drewsum/Thermal_Camera/rev_a/hdw/Thermal_Camera/Battery_Management.kicad_sch

## KiCad design rev_a/hdw/Thermal_Camera/Battery_Management.kicad_sch (2024-10-11)

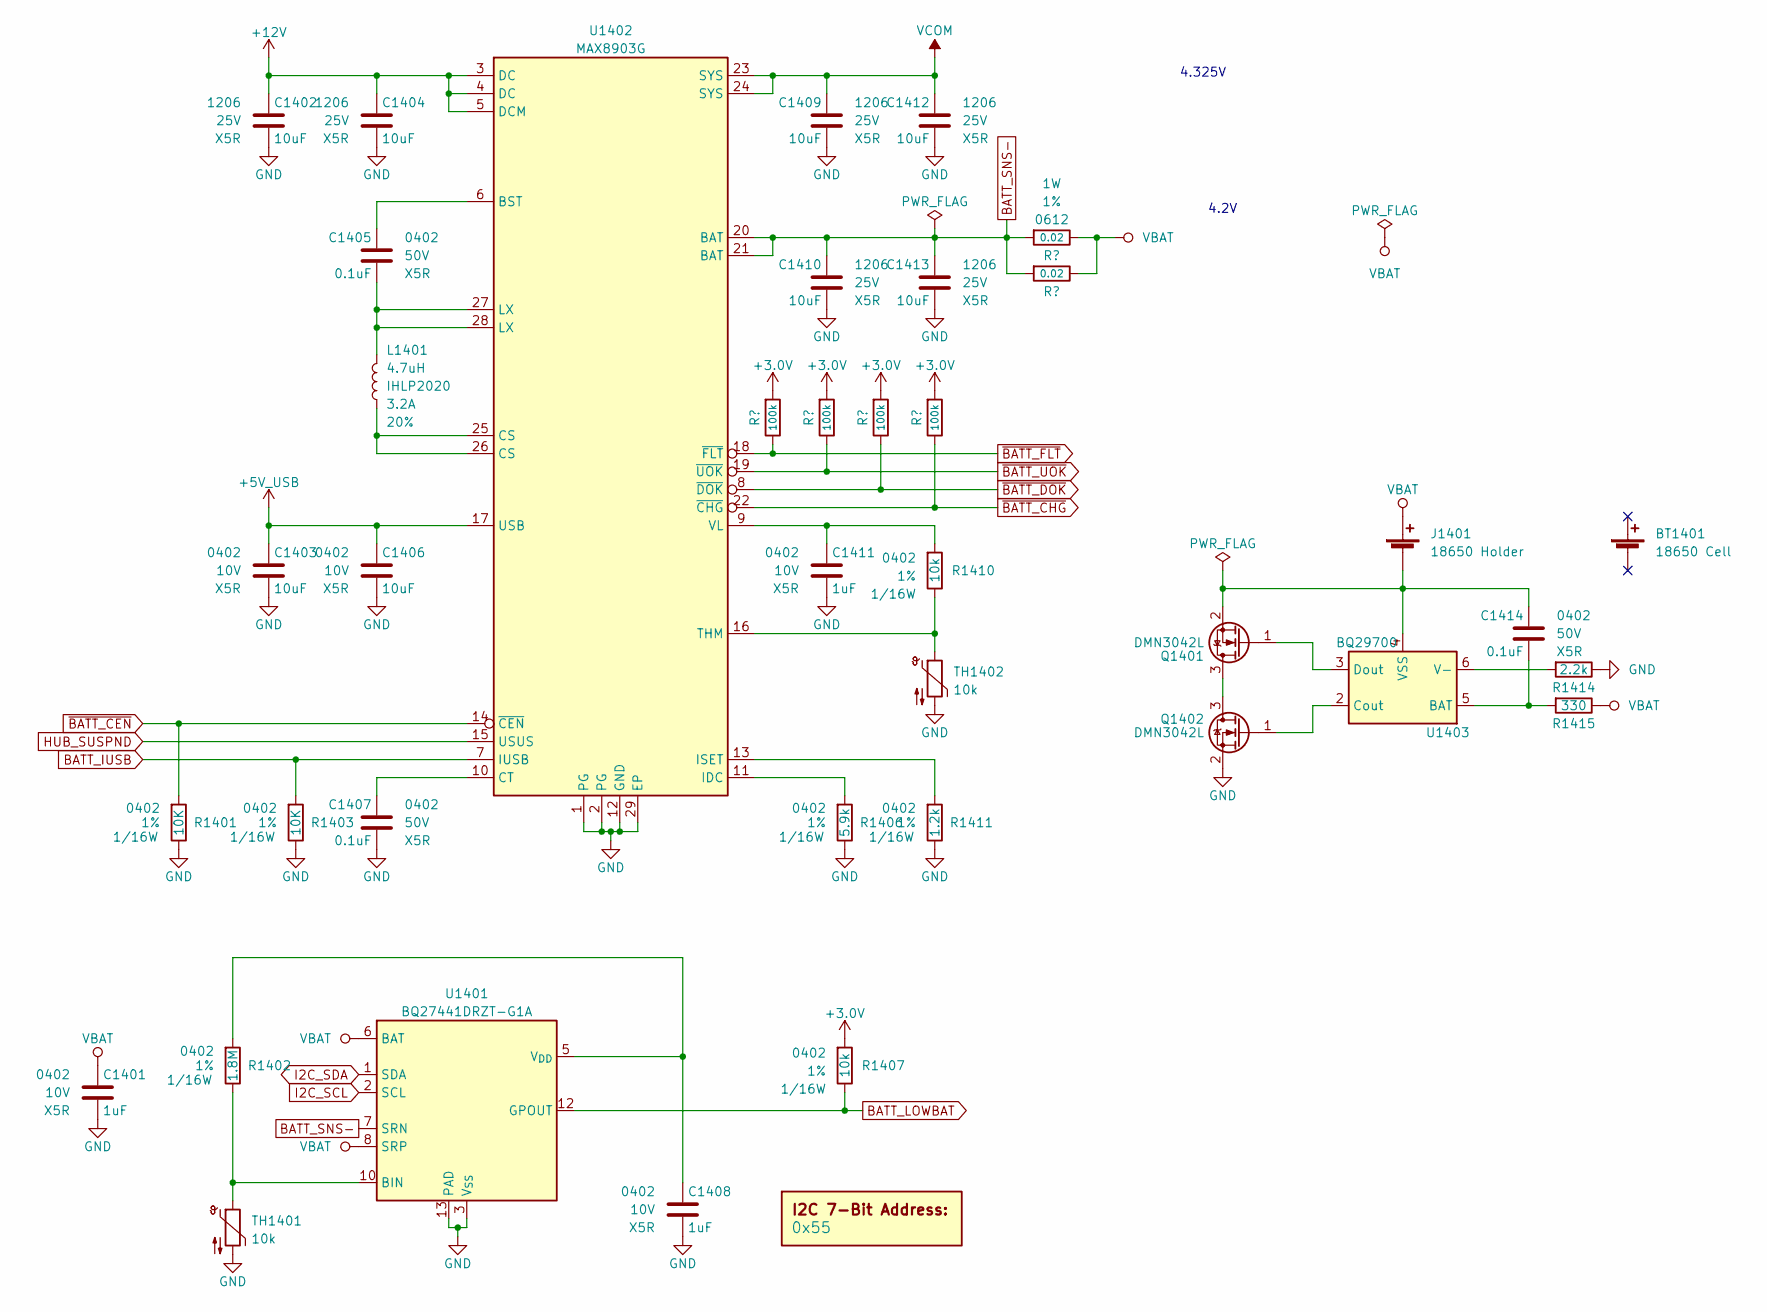
[picture p4: schematic Battery_Management.kicad_sch]

Parts:
BT1401: 18650 Cell; Digi-Key PN 1568-1488-ND
C1401, C1408, C1411: 1uF; C_0402; Voltage 10V; Digi-Key PN 311-1439-1-ND
C1402, C1404, C1409, C1410, C1412, C1413: 10uF; C_1206; Voltage 25V; Digi-Key PN 399-8153-1-ND
C1403, C1406: 10uF; C_0402; Voltage 10V; Digi-Key PN 490-GRM155R61A106ME11DCT-ND
C1405, C1407, C1414: 0.1uF; C_0402; Voltage 50V; Digi-Key PN 490-10697-1-ND
DOC1401: 0x55
J1401: 18650 Holder; BatteryHolder_MPD_BH-18650-PC2; Digi-Key PN BK-18650-PC2-ND
L1401: 4.7uH; L_Vishay_IHLP-2020; Tolerance 20%; Digi-Key PN 541-1222-1-ND
Q1401, Q1402: DMN3042L; SOT-23; Digi-Key PN DMN3042L-7DICT-ND
R1401, R1403: 10K; R_0402; Tolerance 1%; Digi-Key PN RMCF0402FT10K0CT-ND
R1402: 1.8M; R_0402; Tolerance 1%; Digi-Key PN RMCF0402FT1M80CT-ND
R1404, R1405, R1408, R1409: 100k; R_0402; Tolerance 1%; Digi-Key PN RMCF0402FT100KCT-ND
R1406: 5.9k; R_0402; Tolerance 1%; Digi-Key PN RMCF0402FT5K90CT-ND
R1407, R1410: 10k; R_0402; Tolerance 1%; Digi-Key PN RMCF0402FT10K0CT-ND
R1411: 1.2k; R_0402; Tolerance 1%; Digi-Key PN RMCF0402FT1K20CT-ND
R1412, R1413: 0.02; R_0612; Tolerance 1%; Digi-Key PN P16010CT-ND
R1414: 2.2k; R_0402; Tolerance 1%; Digi-Key PN RMCF0402FT2K20CT-ND
R1415: 330; R_0402; Tolerance 1%; Digi-Key PN RMCF0402FT330RCT-ND
TH1401, TH1402: 10k; R_0402; Digi-Key PN 445-174911-1-ND
U1401: BQ27441DRZT-G1A; Texas_S-PDSO-N12; Digi-Key PN 296-37271-1-ND
U1402: MAX8903G; QFN-28-1EP_4x4mm_P0.4mm_EP2.6x2.6mm; Digi-Key PN MAX8903GETI+-ND
U1403: BQ29700; WSON-6_1.5x1.5mm_P0.5mm; Digi-Key PN 296-43985-1-ND

Connections:
+3.0V: R1404.1, R1405.1, R1407.1, R1408.1, R1409.1
+5V_USB: C1403.1, C1406.1, U1402.17 (USB)
+12V: C1402.1, C1404.1, U1402.3 (DC), U1402.4 (DC), U1402.5 (DCM)
BATT_IUSB: R1403.1, U1402.7 (IUSB)
BATT_LOWBAT: R1407.2, U1401.12 (GPOUT)
BATT_SNS-: C1410.1, C1413.1, R1412.1, R1413.1, U1401.7 (SRN), U1402.20 (BAT), U1402.21 (BAT)
GND: C1401.2, C1402.2, C1403.2, C1404.2, C1406.2, C1407.2, C1408.2, C1409.2, C1410.2, C1411.2, C1412.2, C1413.2, Q1402.2 (S), R1401.2, R1403.2, R1406.2, R1411.2, R1414.2, TH1401.2, TH1402.2, U1401.3 (V_{SS}), U1401.13 (PAD), U1402.1 (PG), U1402.2 (PG), U1402.12 (GND), U1402.29 (EP)
HUB_SUSPND: U1402.15 (USUS)
I2C_SCL: U1401.2 (SCL)
I2C_SDA: U1401.1 (SDA)
unnamed: C1405.1, U1402.6 (BST)
unnamed: C1405.2, L1401.2, U1402.27 (LX), U1402.28 (LX)
unnamed: C1407.1, U1402.10 (CT)
unnamed: C1408.1, R1402.1, U1401.5 (V_{DD})
unnamed: C1411.1, R1410.1, U1402.9 (VL)
unnamed: C1414.1, J1401.2 (-), Q1401.2 (S), U1403.4 (VSS)
unnamed: C1414.2, R1415.1, U1403.5 (BAT)
unnamed: L1401.1, U1402.25 (CS), U1402.26 (CS)
unnamed: Q1401.1 (G), U1403.3 (Dout)
unnamed: Q1401.3 (D), Q1402.3 (D)
unnamed: Q1402.1 (G), U1403.2 (Cout)
unnamed: R1402.2, TH1401.1, U1401.10 (BIN)
unnamed: R1406.1, U1402.11 (IDC)
unnamed: R1410.2, TH1402.1, U1402.16 (THM)
unnamed: R1411.1, U1402.13 (ISET)
unnamed: R1414.1, U1403.6 (V-)
VBAT: C1401.1, J1401.1 (+), R1412.2, R1413.2, R1415.2, U1401.6 (BAT), U1401.8 (SRP)
VCOM: C1409.1, C1412.1, U1402.23 (SYS), U1402.24 (SYS)
~BATT_CEN: R1401.1, U1402.14 (~CEN)
~BATT_CHG: R1409.2, U1402.22 (~CHG)
~BATT_DOK: R1408.2, U1402.8 (~DOK)
~BATT_FLT: R1404.2, U1402.18 (~FLT)
~BATT_UOK: R1405.2, U1402.19 (~UOK)

Notes on the sheet:
4.325V
4.2V
