drewsum/Thermal_Camera/rev_a/hdw/Thermal_Camera/Capacitive_Touch.kicad_sch

## KiCad design rev_a/hdw/Thermal_Camera/Capacitive_Touch.kicad_sch (2024-10-11)

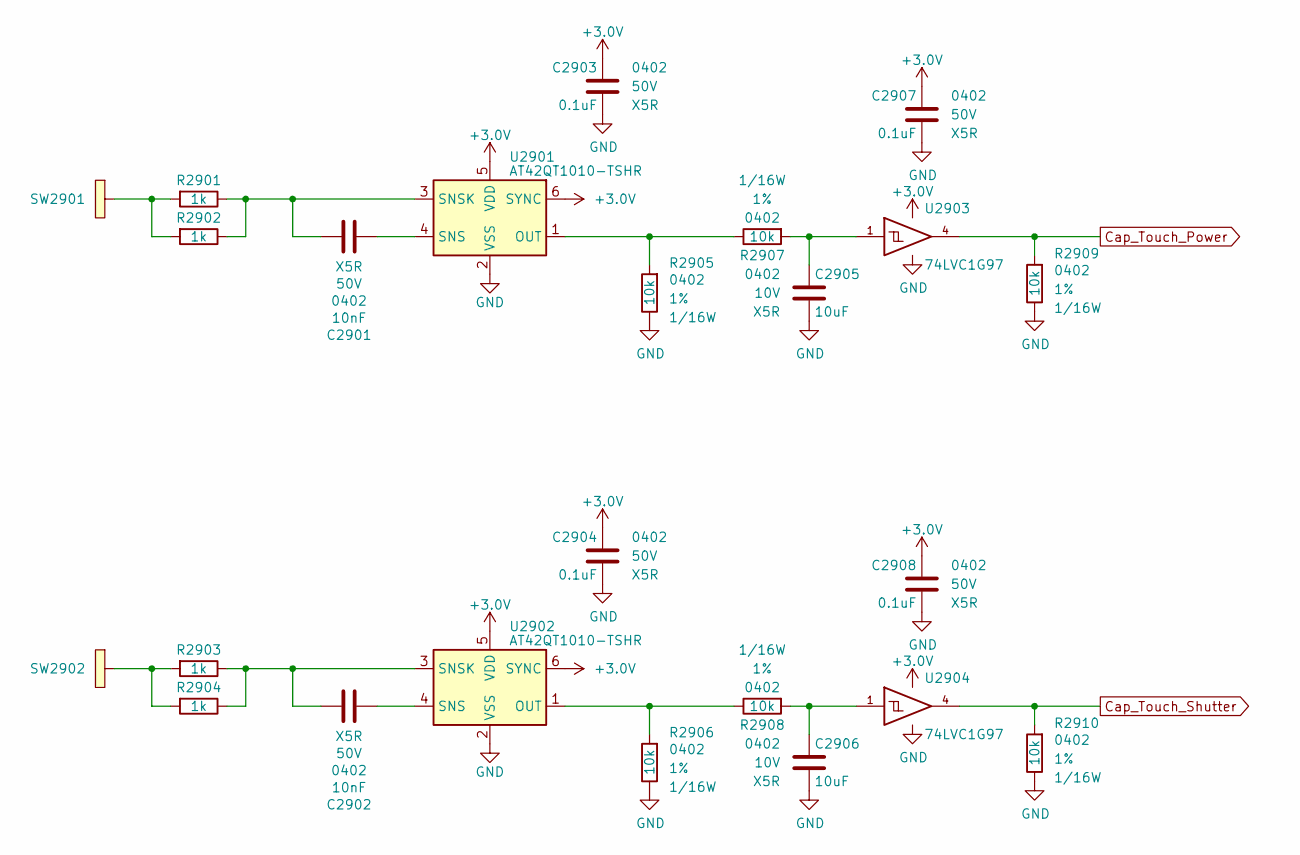
[picture p5: schematic Capacitive_Touch.kicad_sch]

Parts:
C2901, C2902: 10nF; C_0402; Voltage 50V; Digi-Key PN 445-12201-1-ND
C2903, C2904, C2907, C2908: 0.1uF; C_0402; Voltage 50V; Digi-Key PN 490-10697-1-ND
C2905, C2906: 10uF; C_0402; Voltage 10V; Digi-Key PN 490-GRM155R61A106ME11DCT-ND
R2901, R2902, R2903, R2904: 1k; R_0402; Tolerance 1%; Digi-Key PN RMCF0402FT1K00CT-ND
R2905, R2906, R2907, R2908, R2909, R2910: 10k; R_0402; Tolerance 1%; Digi-Key PN RMCF0402FT10K0CT-ND
SW2901, SW2902: Cap_Touch; Capacitive_Touch_Pad
U2901, U2902: AT42QT1010-TSHR; SOT-23-6; Digi-Key PN AT42QT1010-TSHRCT-ND
U2903, U2904: 74LVC1G97; SOT-363_SC-70-6; Digi-Key PN 296-15582-1-ND

Connections:
+3.0V: C2903.1, C2904.1, C2907.1, C2908.1, U2901.5 (VDD), U2901.6 (SYNC), U2902.5 (VDD), U2902.6 (SYNC), U2903.5 (VCC), U2904.5 (VCC)
Cap_Touch_Power: R2909.1, U2903.4
Cap_Touch_Shutter: R2910.1, U2904.4
GND: C2903.2, C2904.2, C2905.2, C2906.2, C2907.2, C2908.2, R2905.2, R2906.2, R2909.2, R2910.2, U2901.2 (VSS), U2902.2 (VSS), U2903.2 (GND), U2903.3 (GND), U2903.6 (GND), U2904.2 (GND), U2904.3 (GND), U2904.6 (GND)
unnamed: C2901.1, U2901.4 (SNS)
unnamed: C2901.2, R2901.2, R2902.2, U2901.3 (SNSK)
unnamed: C2902.1, U2902.4 (SNS)
unnamed: C2902.2, R2903.2, R2904.2, U2902.3 (SNSK)
unnamed: C2905.1, R2907.1, U2903.1
unnamed: C2906.1, R2908.1, U2904.1
unnamed: R2901.1, R2902.1, SW2901.1
unnamed: R2903.1, R2904.1, SW2902.1
unnamed: R2905.1, R2907.2, U2901.1 (OUT)
unnamed: R2906.1, R2908.2, U2902.1 (OUT)
