drewsum/Thermal_Camera/rev_a/hdw/Thermal_Camera/Elapsed_Time_Counter.kicad_sch

## KiCad design rev_a/hdw/Thermal_Camera/Elapsed_Time_Counter.kicad_sch (2024-10-11)

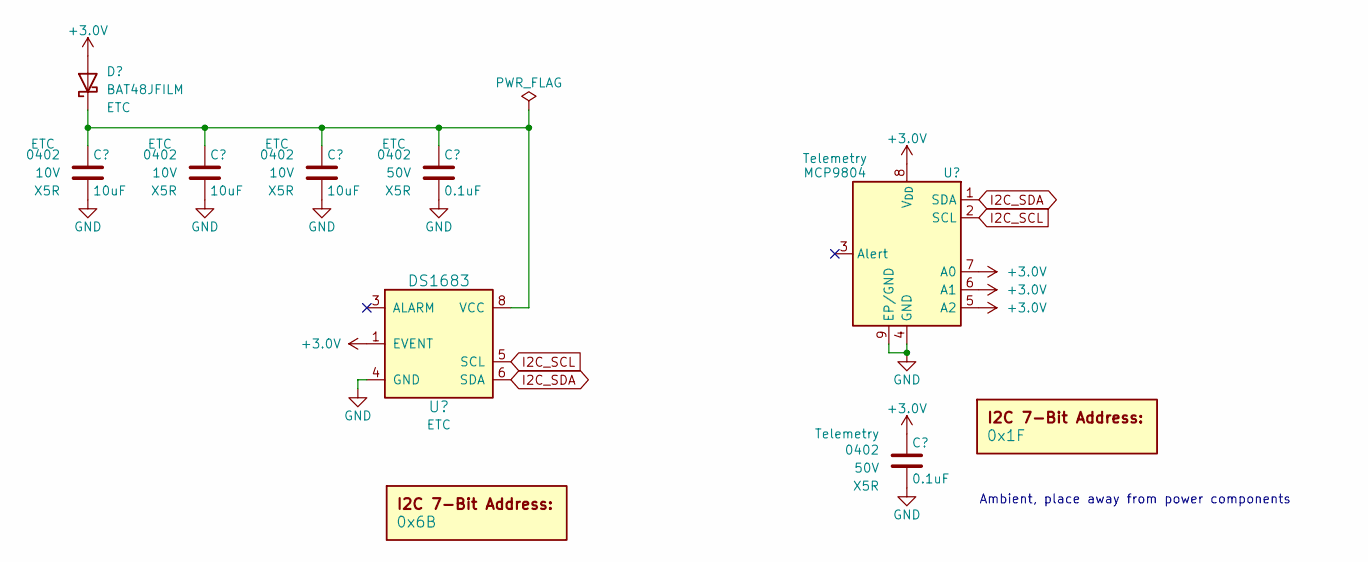
[picture p6: schematic Elapsed_Time_Counter.kicad_sch]

Parts:
C2301, C2302, C2303: 10uF; C_0402; Voltage 10V; Digi-Key PN 490-GRM155R61A106ME11DCT-ND
C2304, C2305: 0.1uF; C_0402; Voltage 50V; Digi-Key PN 490-10697-1-ND
D2301: BAT48JFILM; D_SOD-323; Digi-Key PN 497-5711-1-ND
DOC2301: 0x6B
DOC2302: 0x1F
U2301: DS1683; SOIC-8_3.9x4.9mm_Pitch1.27mm; Digi-Key PN DS1683S+-ND
U2302: MCP9804; DFN-8-1EP_3x2mm_P0.5mm_EP1.3x1.5mm; Digi-Key PN MCP9804T-E/MCCT-ND

Connections:
+3.0V: C2305.1, D2301.2 (A), U2301.1 (EVENT), U2302.5 (A2), U2302.6 (A1), U2302.7 (A0), U2302.8 (V_{DD})
GND: C2301.2, C2302.2, C2303.2, C2304.2, C2305.2, U2301.4 (GND), U2302.4 (GND), U2302.9 (EP/GND)
I2C_SCL: U2301.5 (SCL), U2302.2 (SCL)
I2C_SDA: U2301.6 (SDA), U2302.1 (SDA)
unnamed: C2301.1, C2302.1, C2303.1, C2304.1, D2301.1 (K), U2301.8 (VCC)

Notes on the sheet:
Ambient, place away from power components
