drewsum/Thermal_Camera/rev_a/hdw/Thermal_Camera/External_Storage.kicad_sch

## KiCad design rev_a/hdw/Thermal_Camera/External_Storage.kicad_sch (2024-10-11)

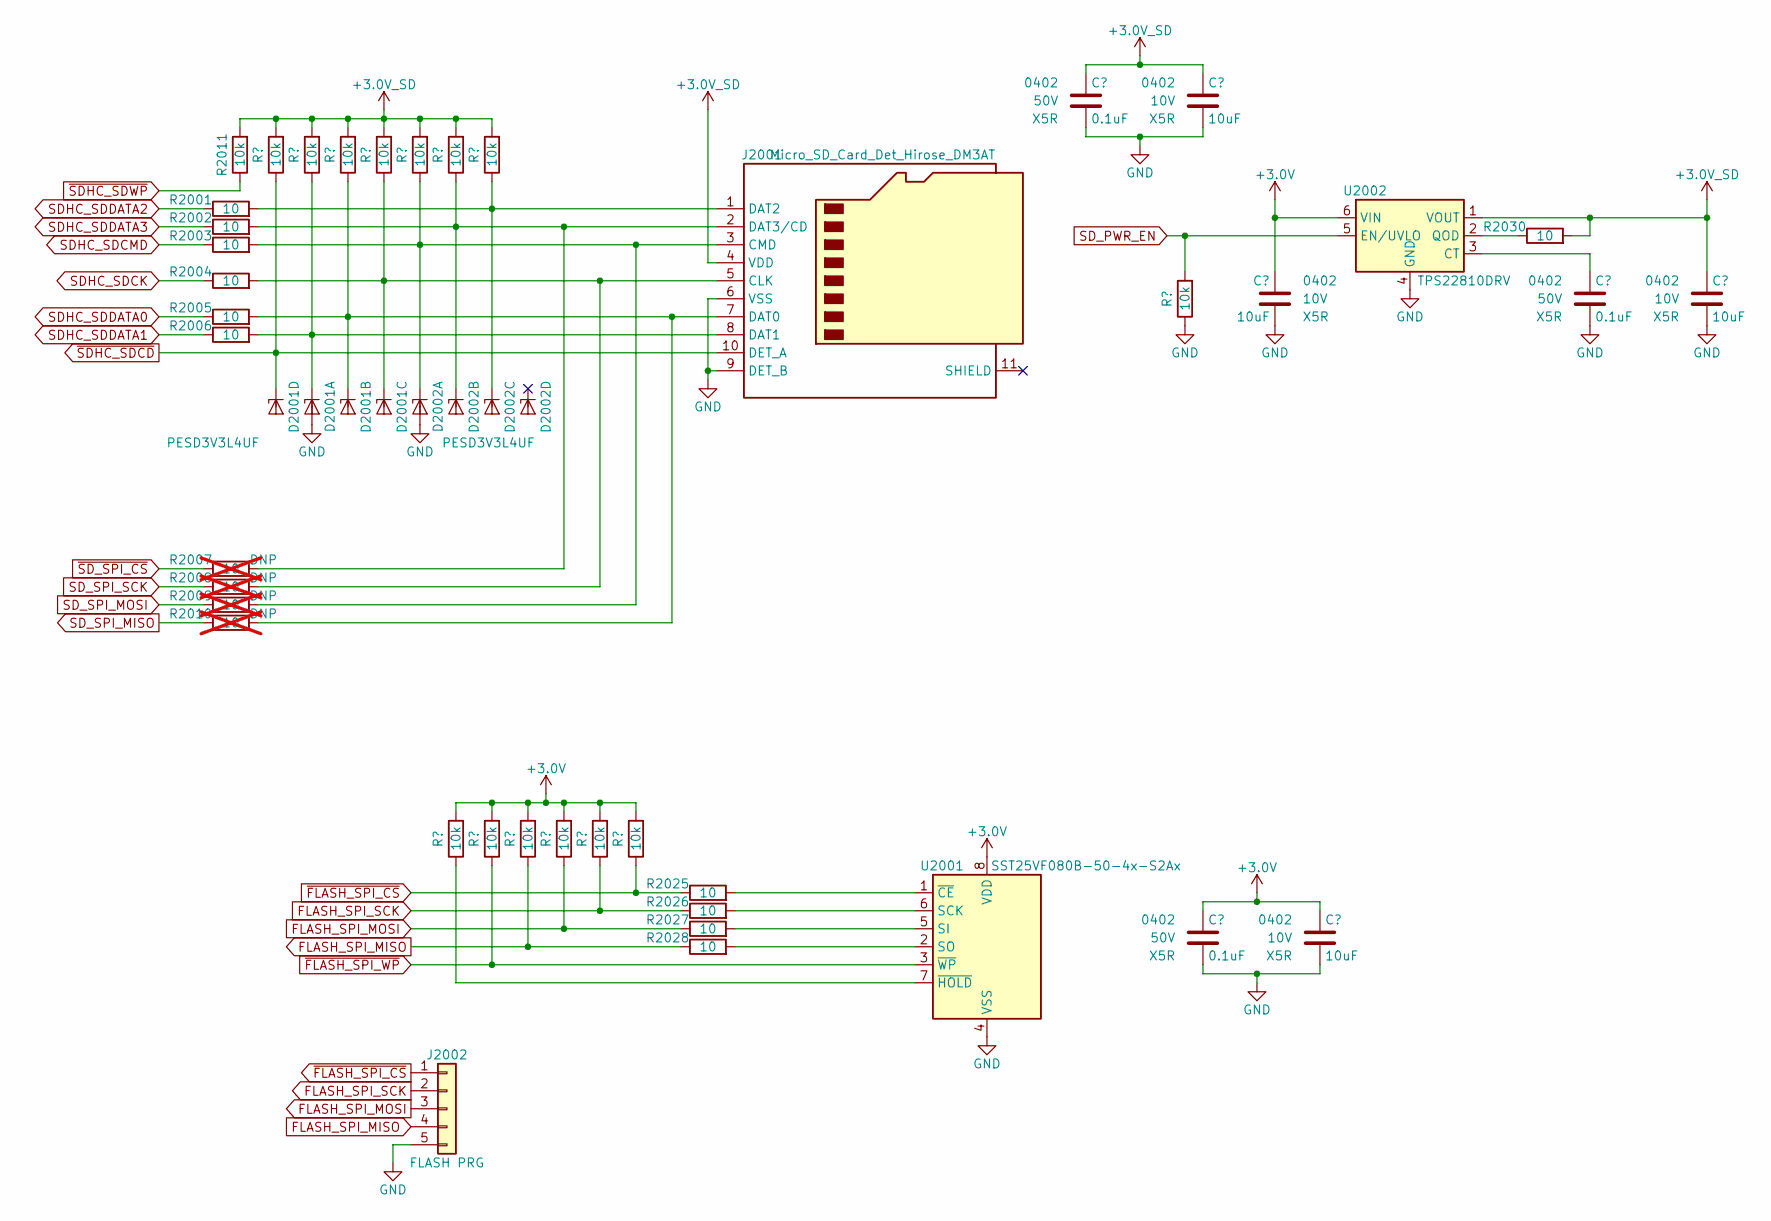
[picture p7: schematic External_Storage.kicad_sch]

Parts:
C2001, C2003, C2006: 0.1uF; C_0402; Voltage 50V; Digi-Key PN 490-10697-1-ND
C2002, C2004, C2005, C2007: 10uF; C_0402; Voltage 10V; Digi-Key PN 490-GRM155R61A106ME11DCT-ND
D2001, D2002: PESD3V3L4UF; SOT-886
J2001: Micro_SD_Card_Det_Hirose_DM3AT; Hirose_DM3AT-SF-PEJM5; Digi-Key PN HR1964CT-ND
J2002: FLASH PRG; PinSocket_1x05_P2.54mm_Vertical
R2001, R2002, R2003, R2004, R2005, R2006, R2025, R2026, R2027, R2028, R2030: 10; R_0402; Tolerance 1%; Digi-Key PN RMCF0402FT10R0CT-ND
R2007, R2008, R2009, R2010: 10; R_0402; Tolerance 1%; Digi-Key PN RMCF0402FT10R0CT-ND; not fitted
R2011, R2012, R2013, R2014, R2015, R2016, R2017, R2018, R2019, R2020, R2021, R2022, R2023, R2024, R2029: 10k; R_0402; Tolerance 1%; Digi-Key PN RMCF0402FT10K0CT-ND
U2001: SST25VF080B-50-4x-S2Ax; SOIC-8_5.275x5.275mm_P1.27mm; Digi-Key PN SST25VF080B-50-4C-S2AF-ND
U2002: TPS22810DRV; WSON-6-1EP_2x2mm_P0.65mm_EP1x1.6mm; Digi-Key PN 296-47868-1-ND

Connections:
+3.0V: C2003.1, C2004.1, C2005.1, R2018.1, R2020.1, R2021.1, R2022.1, R2023.1, R2024.1, U2001.8 (VDD), U2002.6 (VIN)
+3.0V_SD: C2001.1, C2002.1, C2007.1, J2001.4 (VDD), R2011.1, R2012.1, R2013.1, R2014.1, R2015.1, R2016.1, R2017.1, R2019.1, R2030.1, U2002.1 (VOUT)
FLASH_SPI_MISO: J2002.4, R2021.2, R2028.2
FLASH_SPI_MOSI: J2002.3, R2022.2, R2027.2
FLASH_SPI_SCK: J2002.2, R2023.2, R2026.2
GND: C2001.2, C2002.2, C2003.2, C2004.2, C2005.2, C2006.2, C2007.2, D2001.2 (A), D2001.5 (A), D2002.2 (A), D2002.5 (A), J2001.6 (VSS), J2001.9 (DET_B), J2002.5, R2029.2, U2001.4 (VSS), U2002.4 (GND), U2002.7 (GND)
unnamed: C2006.1, U2002.3 (CT)
unnamed: D2001.1 (K1), J2001.8 (DAT1), R2006.1, R2013.2
unnamed: D2001.3 (K2), J2001.7 (DAT0), R2005.1, R2010.1, R2014.2
unnamed: D2001.4 (K3), J2001.5 (CLK), R2004.1, R2008.1, R2015.2
unnamed: D2002.1 (K1), J2001.3 (CMD), R2003.1, R2009.1, R2016.2
unnamed: D2002.3 (K2), J2001.2 (DAT3/CD), R2002.1, R2007.1, R2017.2
unnamed: D2002.4 (K3), J2001.1 (DAT2), R2001.1, R2019.2
unnamed: R2018.2, U2001.7 (~HOLD)
unnamed: R2025.1, U2001.1 (~CE)
unnamed: R2026.1, U2001.6 (SCK)
unnamed: R2027.1, U2001.5 (SI)
unnamed: R2028.1, U2001.2 (SO)
unnamed: R2030.2, U2002.2 (QOD)
SDHC_SDCK: R2004.2
SDHC_SDCMD: R2003.2
SDHC_SDDATA0: R2005.2
SDHC_SDDATA1: R2006.2
SDHC_SDDATA2: R2001.2
SDHC_SDDATA3: R2002.2
SD_PWR_EN: R2029.1, U2002.5 (EN/UVLO)
SD_SPI_MISO: R2010.2
SD_SPI_MOSI: R2009.2
SD_SPI_SCK: R2008.2
~FLASH_SPI_CS: J2002.1, R2024.2, R2025.2
~FLASH_SPI_WP: R2020.2, U2001.3 (~WP)
~SDHC_SDCD: D2001.6 (K4), J2001.10 (DET_A), R2012.2
~SDHC_SDWP: R2011.2
~SD_SPI_CS: R2007.2
