drewsum/Thermal_Camera/rev_a/hdw/Thermal_Camera/FLIR_Lepton_Sensor.kicad_sch

## KiCad design rev_a/hdw/Thermal_Camera/FLIR_Lepton_Sensor.kicad_sch (2024-10-11)

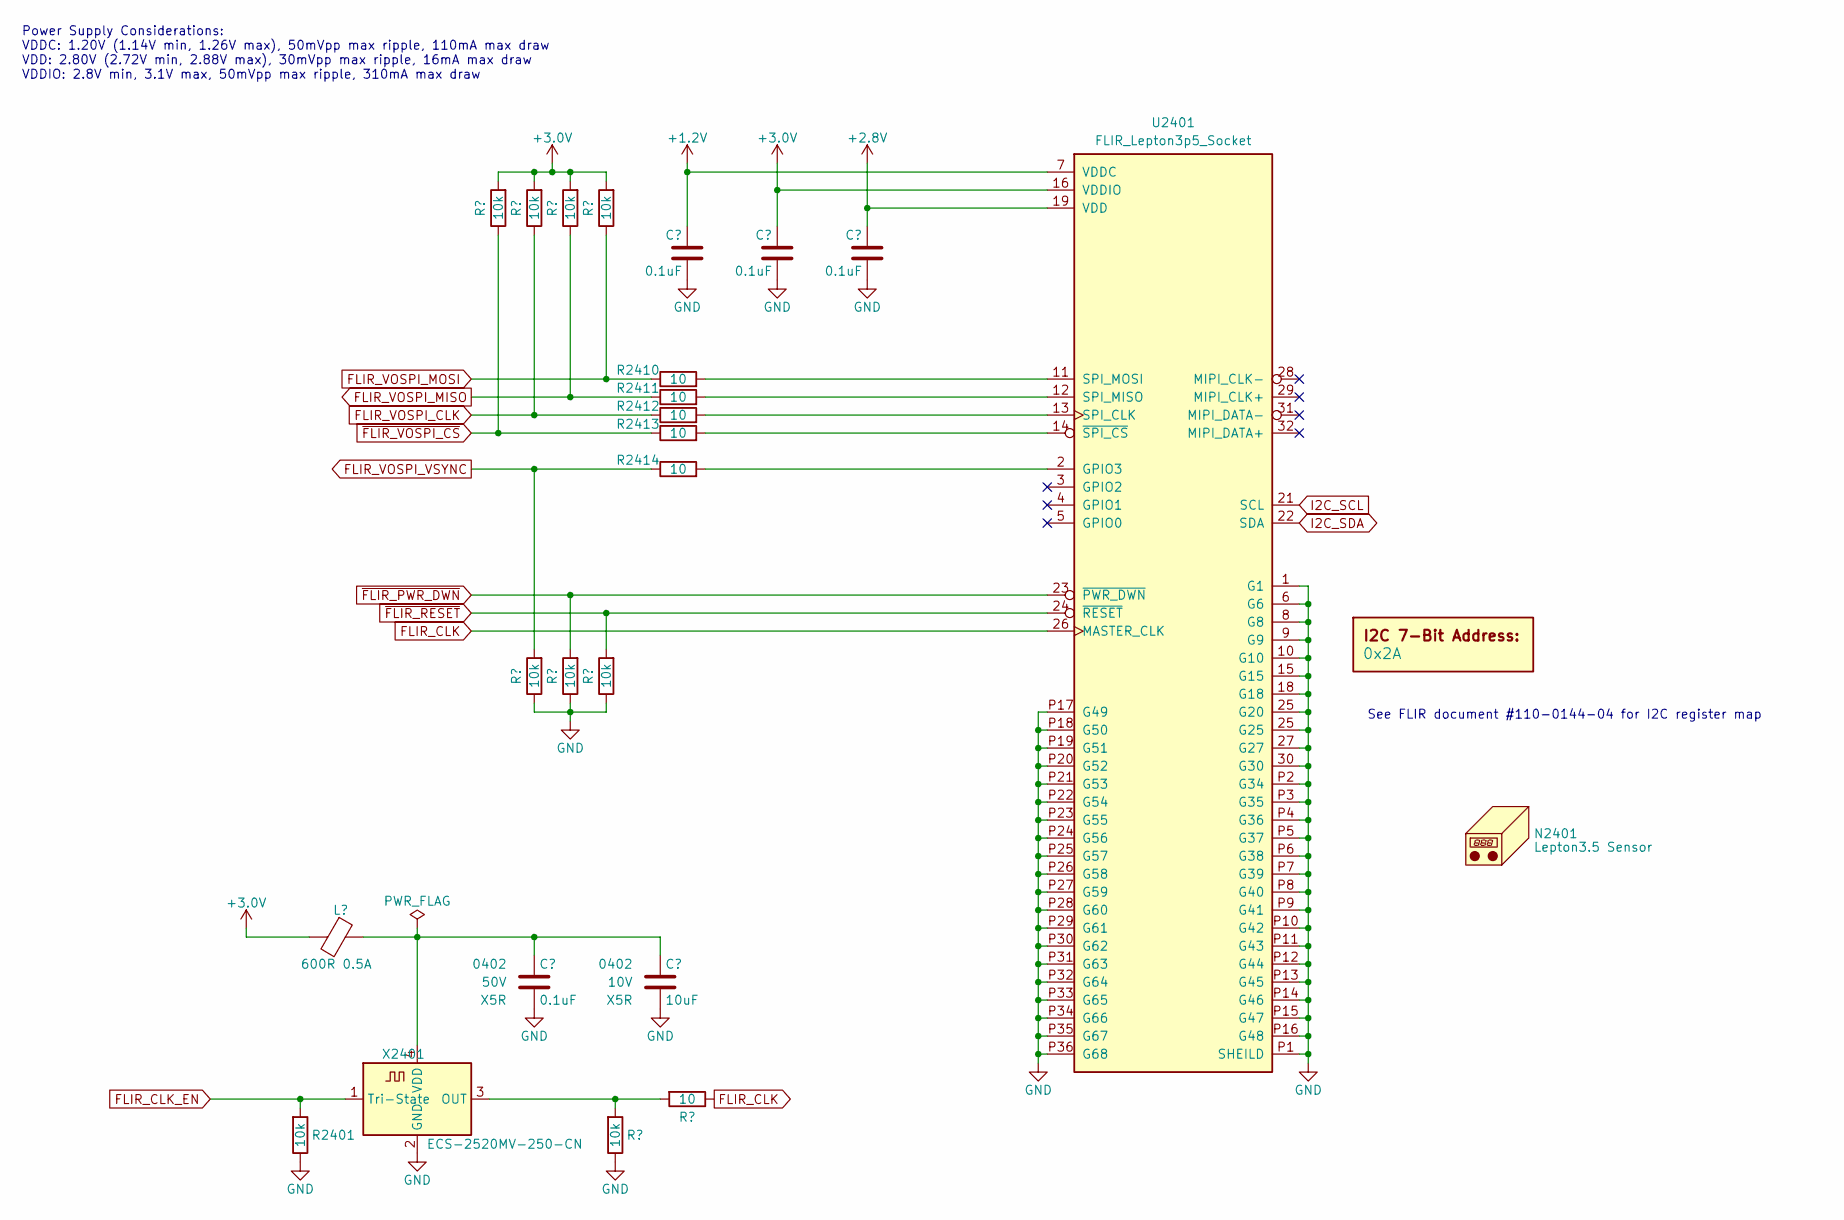
[picture p8: schematic FLIR_Lepton_Sensor.kicad_sch]

Parts:
C2401, C2403, C2404, C2405: 0.1uF; C_0402; Voltage 50V; Digi-Key PN 490-10697-1-ND
C2402: 10uF; C_0402; Voltage 10V; Digi-Key PN 490-GRM155R61A106ME11DCT-ND
DOC2401: 0x2A
L2401: 600R 0.5A; L_0402
N2401: Lepton3.5 Sensor; Digi-Key PN 500-0771-01-ND
R2401, R2402, R2403, R2404, R2405, R2406, R2407, R2408, R2409: 10k; R_0402; Tolerance 1%; Digi-Key PN RMCF0402FT10K0CT-ND
R2410, R2411, R2412, R2413, R2414, R2415: 10; R_0402; Tolerance 1%; Digi-Key PN RMCF0402FT10R0CT-ND
U2401: FLIR_Lepton3p5_Socket; MOLEX_105028-1001; Digi-Key PN 1050281001
X2401: ECS-2520MV-250-CN; Oscillator_SMD_ECS_2520MV-xxx-xx-4Pin_2.5x2.0mm; Digi-Key PN XC2752CT-ND

Connections:
+1.2V: C2403.1, U2401.7 (VDDC)
+2.8V: C2405.1, U2401.19 (VDD)
+3.0V: C2404.1, L2401.2, R2402.1, R2403.1, R2405.1, R2407.1, U2401.16 (VDDIO)
FLIR_CLK: R2415.2, U2401.26 (MASTER_CLK)
FLIR_CLK_EN: R2401.1, X2401.1 (Tri-State)
FLIR_VOSPI_CLK: R2403.2, R2412.2
FLIR_VOSPI_MISO: R2405.2, R2411.2
FLIR_VOSPI_MOSI: R2407.2, R2410.2
FLIR_VOSPI_VSYNC: R2404.1, R2414.2
GND: C2401.2, C2402.2, C2403.2, C2404.2, C2405.2, R2401.2, R2404.2, R2406.2, R2408.2, R2409.2, U2401.1 (G1), U2401.6 (G6), U2401.8 (G8), U2401.9 (G9), U2401.10 (G10), U2401.15 (G15), U2401.18 (G18), U2401.25 (G20), U2401.27 (G27), U2401.30 (G30), U2401.P1 (SHEILD), U2401.P2 (G34), U2401.P3 (G35), U2401.P4 (G36), U2401.P5 (G37), U2401.P6 (G38), U2401.P7 (G39), U2401.P8 (G40), U2401.P9 (G41), U2401.P10 (G42), U2401.P11 (G43), U2401.P12 (G44), U2401.P13 (G45), U2401.P14 (G46), U2401.P15 (G47), U2401.P16 (G48), U2401.P17 (G49), U2401.P18 (G50), U2401.P19 (G51), U2401.P20 (G52), U2401.P21 (G53), U2401.P22 (G54), U2401.P23 (G55), U2401.P24 (G56), U2401.P25 (G57), U2401.P26 (G58), U2401.P27 (G59), U2401.P28 (G60), U2401.P29 (G61), U2401.P30 (G62), U2401.P31 (G63), U2401.P32 (G64), U2401.P33 (G65), U2401.P34 (G66), U2401.P35 (G67), U2401.P36 (G68), X2401.2 (GND)
I2C_SCL: U2401.21 (SCL)
I2C_SDA: U2401.22 (SDA)
unnamed: C2401.1, C2402.1, L2401.1, X2401.4 (VDD)
unnamed: R2409.1, R2415.1, X2401.3 (OUT)
unnamed: R2410.1, U2401.11 (SPI_MOSI)
unnamed: R2411.1, U2401.12 (SPI_MISO)
unnamed: R2412.1, U2401.13 (SPI_CLK)
unnamed: R2413.1, U2401.14 (~SPI_CS)
unnamed: R2414.1, U2401.2 (GPIO3)
~FLIR_PWR_DWN: R2406.1, U2401.23 (~PWR_DWN)
~FLIR_RESET: R2408.1, U2401.24 (~RESET)
~FLIR_VOSPI_CS: R2402.2, R2413.2

Notes on the sheet:
Power Supply Considerations: VDDC: 1.20V (1.14V min, 1.26V max), 50mVpp max ripple, 110mA max draw VDD: 2.80V (2.72V min, 2.88V max), 30mVpp max ripple, 16mA max draw VDDIO: 2.8V min, 3.1V max, 50mVpp max ripple, 310mA max draw
See FLIR document #110-0144-04 for I2C register map
