drewsum/Thermal_Camera/rev_a/hdw/Thermal_Camera/Graphic_LCD.kicad_sch

## KiCad design rev_a/hdw/Thermal_Camera/Graphic_LCD.kicad_sch (2024-10-11)

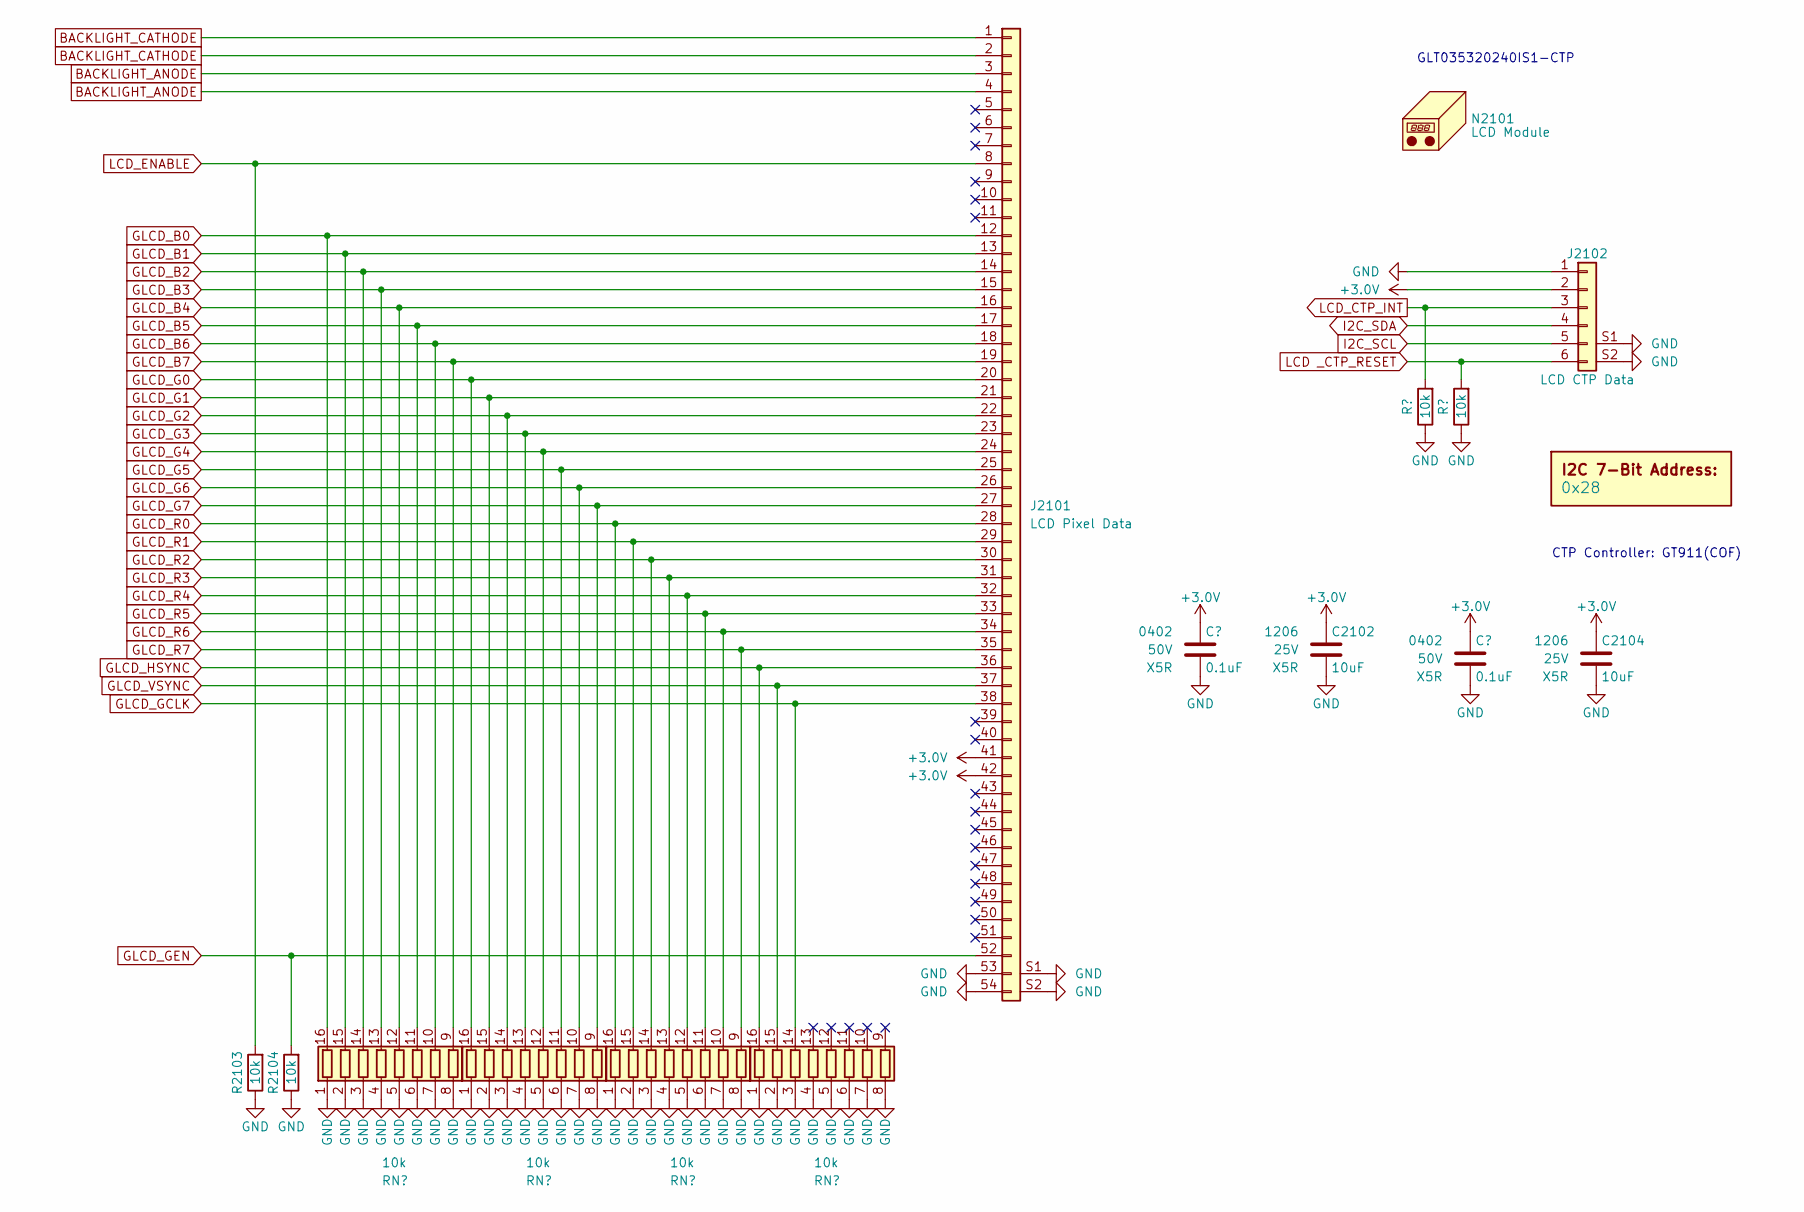
[picture p9: schematic Graphic_LCD.kicad_sch]

Parts:
C2101, C2103: 0.1uF; C_0402; Voltage 50V; Digi-Key PN 490-10697-1-ND
C2102, C2104: 10uF; C_1206; Voltage 25V; Digi-Key PN 399-8153-1-ND
DOC2101: 0x28
J2101: LCD Pixel Data; GCT_FFC2B35-54-G_REVA2; Digi-Key PN 2073-FFC2B35-54-GCT-ND
J2102: LCD CTP Data; GCT_FFC2B35-06-G_REVA2; Digi-Key PN 2073-FFC2B35-06-GCT-ND
N2101: LCD Module; GLT035320240IS1-CTP; Digi-Key PN GLT035320240IS1-CTP
R2101, R2102, R2103, R2104: 10k; R_0402; Tolerance 1%; Digi-Key PN RMCF0402FT10K0CT-ND
RN2101, RN2102, RN2103, RN2104: 10k; R_Array_Convex_8x0602; Tolerance 1%; Digi-Key PN Y1103CT-ND

Connections:
+3.0V: C2101.1, C2102.1, C2103.1, C2104.1, J2101.41, J2101.42, J2102.2
BACKLIGHT_ANODE: J2101.3, J2101.4
BACKLIGHT_CATHODE: J2101.1, J2101.2
GLCD_B0: J2101.12, RN2101.16 (R1.2)
GLCD_B1: J2101.13, RN2101.15 (R2.2)
GLCD_B2: J2101.14, RN2101.14 (R3.2)
GLCD_B3: J2101.15, RN2101.13 (R4.2)
GLCD_B4: J2101.16, RN2101.12 (R5.2)
GLCD_B5: J2101.17, RN2101.11 (R6.2)
GLCD_B6: J2101.18, RN2101.10 (R7.2)
GLCD_B7: J2101.19, RN2101.9 (R8.2)
GLCD_G0: J2101.20, RN2102.16 (R1.2)
GLCD_G1: J2101.21, RN2102.15 (R2.2)
GLCD_G2: J2101.22, RN2102.14 (R3.2)
GLCD_G3: J2101.23, RN2102.13 (R4.2)
GLCD_G4: J2101.24, RN2102.12 (R5.2)
GLCD_G5: J2101.25, RN2102.11 (R6.2)
GLCD_G6: J2101.26, RN2102.10 (R7.2)
GLCD_G7: J2101.27, RN2102.9 (R8.2)
GLCD_GCLK: J2101.38, RN2104.14 (R3.2)
GLCD_GEN: J2101.52, R2104.1
GLCD_HSYNC: J2101.36, RN2104.16 (R1.2)
GLCD_R0: J2101.28, RN2103.16 (R1.2)
GLCD_R1: J2101.29, RN2103.15 (R2.2)
GLCD_R2: J2101.30, RN2103.14 (R3.2)
GLCD_R3: J2101.31, RN2103.13 (R4.2)
GLCD_R4: J2101.32, RN2103.12 (R5.2)
GLCD_R5: J2101.33, RN2103.11 (R6.2)
GLCD_R6: J2101.34, RN2103.10 (R7.2)
GLCD_R7: J2101.35, RN2103.9 (R8.2)
GLCD_VSYNC: J2101.37, RN2104.15 (R2.2)
GND: C2101.2, C2102.2, C2103.2, C2104.2, J2101.53, J2101.54, J2101.S1, J2101.S2, J2102.1, J2102.S1, J2102.S2, R2101.2, R2102.2, R2103.2, R2104.2, RN2101.1 (R1.1), RN2101.2 (R2.1), RN2101.3 (R3.1), RN2101.4 (R4.1), RN2101.5 (R5.1), RN2101.6 (R6.1), RN2101.7 (R7.1), RN2101.8 (R8.1), RN2102.1 (R1.1), RN2102.2 (R2.1), RN2102.3 (R3.1), RN2102.4 (R4.1), RN2102.5 (R5.1), RN2102.6 (R6.1), RN2102.7 (R7.1), RN2102.8 (R8.1), RN2103.1 (R1.1), RN2103.2 (R2.1), RN2103.3 (R3.1), RN2103.4 (R4.1), RN2103.5 (R5.1), RN2103.6 (R6.1), RN2103.7 (R7.1), RN2103.8 (R8.1), RN2104.1 (R1.1), RN2104.2 (R2.1), RN2104.3 (R3.1), RN2104.4 (R4.1), RN2104.5 (R5.1), RN2104.6 (R6.1), RN2104.7 (R7.1), RN2104.8 (R8.1)
I2C_SCL: J2102.5
I2C_SDA: J2102.4
LCD _CTP_RESET: J2102.6, R2102.1
LCD_CTP_INT: J2102.3, R2101.1
LCD_ENABLE: J2101.8, R2103.1

Notes on the sheet:
GLT035320240IS1-CTP
CTP Controller: GT911(COF)
