drewsum/Thermal_Camera/rev_a/hdw/Thermal_Camera/LCD_Backlight_Power_Supply.kicad_sch

## KiCad design rev_a/hdw/Thermal_Camera/LCD_Backlight_Power_Supply.kicad_sch (2024-10-11)

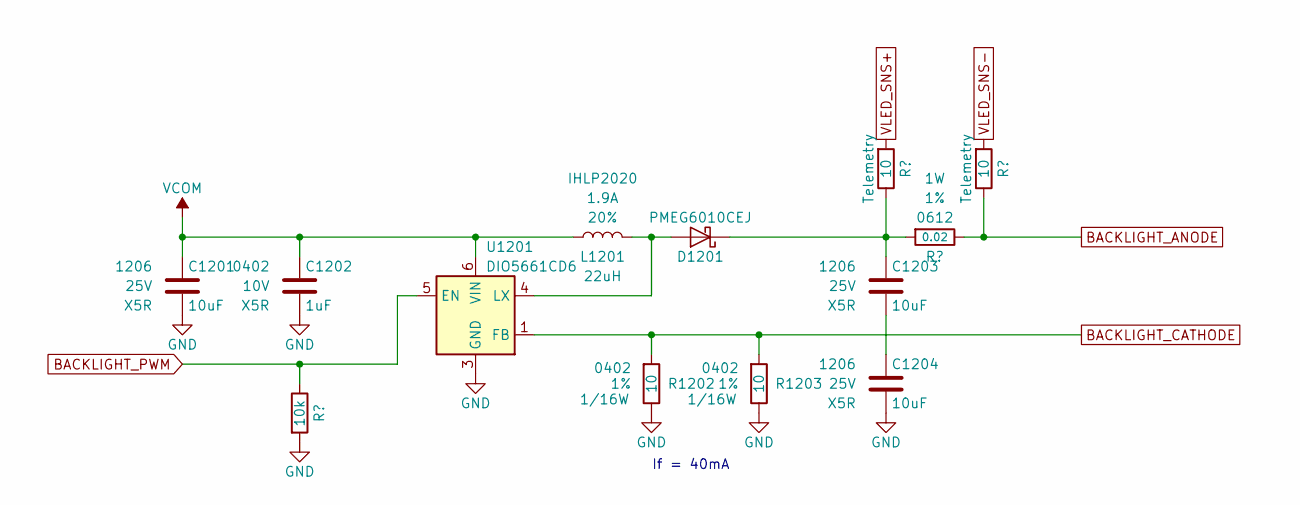
[picture p10: schematic LCD_Backlight_Power_Supply.kicad_sch]

Parts:
C1201, C1203, C1204: 10uF; C_1206; Voltage 25V; Digi-Key PN 399-8153-1-ND
C1202: 1uF; C_0402; Voltage 10V; Digi-Key PN 311-1439-1-ND
D1201: PMEG6010CEJ; D_SOD-323F; Digi-Key PN 1727-3882-1-ND
L1201: 22uH; L_Vishay_IHLP-2020; Tolerance 20%; Digi-Key PN 541-1243-1-ND
R1201: 10k; R_0402; Tolerance 1%; Digi-Key PN RMCF0402FT10K0CT-ND
R1202, R1203, R1204, R1206: 10; R_0402; Tolerance 1%; Digi-Key PN RMCF0402FT10R0CT-ND
R1205: 0.02; R_0612; Tolerance 1%; Digi-Key PN P16010CT-ND
U1201: DIO5661CD6; DFN-6-1EP_2x2mm_P0.65mm_EP1x1.6mm

Connections:
BACKLIGHT_ANODE: R1205.2, R1206.2
BACKLIGHT_CATHODE: R1202.1, R1203.1, U1201.1 (FB)
BACKLIGHT_PWM: R1201.2, U1201.5 (EN)
GND: C1201.2, C1202.2, C1204.2, R1201.1, R1202.2, R1203.2, U1201.3 (GND), U1201.7 (GND)
unnamed: C1203.1, D1201.1 (K), R1204.2, R1205.1
unnamed: C1203.2, C1204.1
unnamed: D1201.2 (A), L1201.2, U1201.4 (LX)
VCOM: C1201.1, C1202.1, L1201.1, U1201.6 (VIN)
VLED_SNS+: R1204.1
VLED_SNS-: R1206.1

Notes on the sheet:
If = 40mA
