drewsum/Thermal_Camera/rev_a/hdw/Thermal_Camera/LCD_Backlight_Telemetry.kicad_sch

## KiCad design rev_a/hdw/Thermal_Camera/LCD_Backlight_Telemetry.kicad_sch (2024-10-11)

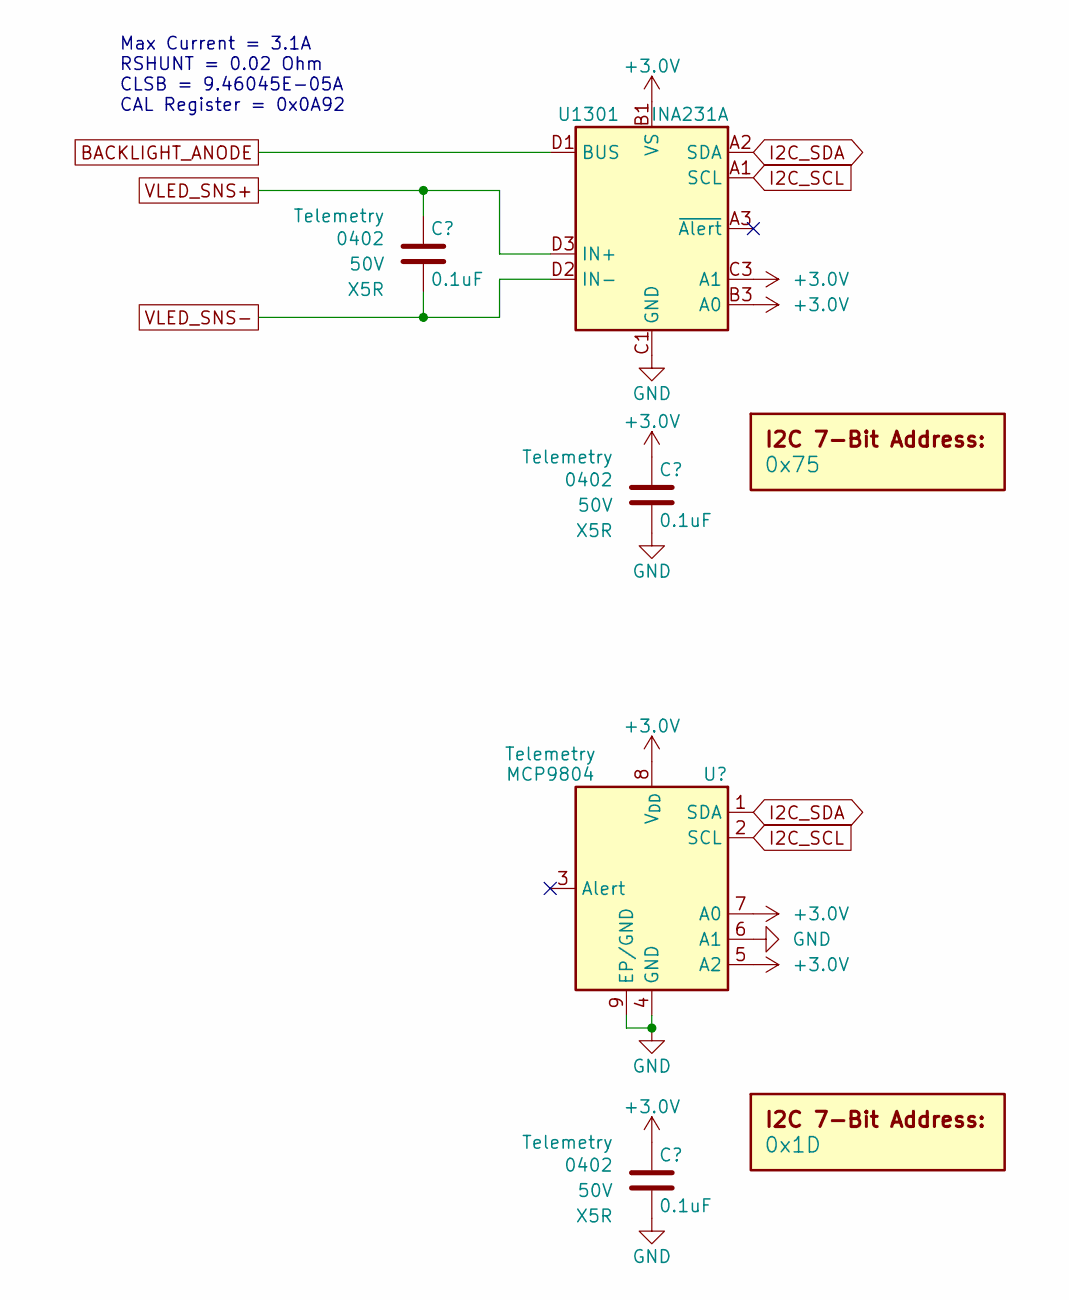
[picture p11: schematic LCD_Backlight_Telemetry.kicad_sch]

Parts:
C1301, C1302, C1303: 0.1uF; C_0402; Voltage 50V; Digi-Key PN 490-10697-1-ND
DOC1301: 0x75
DOC1302: 0x1D
U1301: INA231A; Texas_DSBGA-12_1.65x1.39mm_Layout3x4_P0.4mm; Digi-Key PN 296-41263-1-ND
U1302: MCP9804; DFN-8-1EP_3x2mm_P0.5mm_EP1.3x1.5mm; Digi-Key PN MCP9804T-E/MCCT-ND

Connections:
+3.0V: C1302.1, C1303.1, U1301.B1 (VS), U1301.B3 (A0), U1301.C3 (A1), U1302.5 (A2), U1302.7 (A0), U1302.8 (V_{DD})
BACKLIGHT_ANODE: U1301.D1 (BUS)
GND: C1302.2, C1303.2, U1301.C1 (GND), U1302.4 (GND), U1302.6 (A1), U1302.9 (EP/GND)
I2C_SCL: U1301.A1 (SCL), U1302.2 (SCL)
I2C_SDA: U1301.A2 (SDA), U1302.1 (SDA)
VLED_SNS+: C1301.1, U1301.D3 (IN+)
VLED_SNS-: C1301.2, U1301.D2 (IN-)

Notes on the sheet:
Max Current = 3.1A RSHUNT = 0.02 Ohm CLSB = 9.46045E-05A CAL Register = 0x0A92
