drewsum/Thermal_Camera/rev_a/hdw/Thermal_Camera/Mechanical.kicad_sch

## KiCad design rev_a/hdw/Thermal_Camera/Mechanical.kicad_sch (2024-10-11)

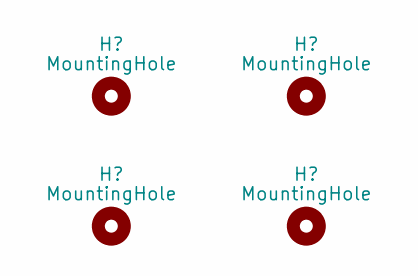
[picture p12: schematic Mechanical.kicad_sch]

Parts:
H3001, H3002, H3003, H3004: MountingHole; MountingHole_3mm
