drewsum/Thermal_Camera/rev_a/hdw/Thermal_Camera/PGOOD_LEDs.kicad_sch

## KiCad design rev_a/hdw/Thermal_Camera/PGOOD_LEDs.kicad_sch (2024-10-11)

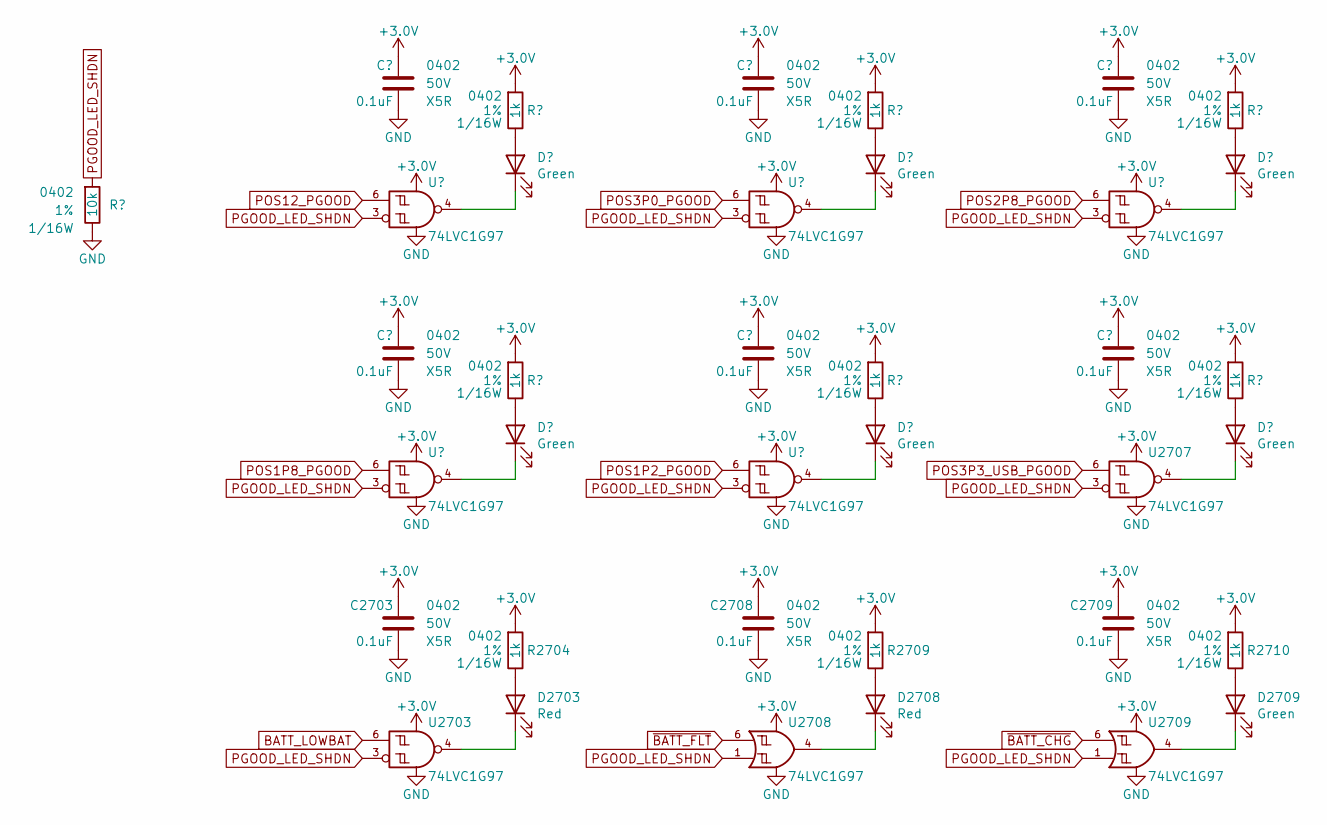
[picture p13: schematic PGOOD_LEDs.kicad_sch]

Parts:
C2701, C2702, C2703, C2704, C2705, C2706, C2707, C2708, C2709: 0.1uF; C_0402; Voltage 50V; Digi-Key PN 490-10697-1-ND
D2701, D2702, D2704, D2705, D2706, D2707, D2709: Green; LED_0402; Digi-Key PN 1497-1219-1-ND
D2703, D2708: Red; LED_0402; Digi-Key PN VLMS1500-GS08CT-ND
R2701: 10k; R_0402; Tolerance 1%; Digi-Key PN RMCF0402FT10K0CT-ND
R2702, R2703, R2704, R2705, R2706, R2707, R2708, R2709, R2710: 1k; R_0402; Tolerance 1%; Digi-Key PN RMCF0402FT1K00CT-ND
U2701, U2702, U2703, U2704, U2705, U2706, U2707: 74LVC1G97; SOT-363_SC-70-6; Digi-Key PN 296-15582-1-ND
U2708, U2709: 74LVC1G97; SOT-363_SC-70-6

Connections:
+3.0V: C2701.1, C2702.1, C2703.1, C2704.1, C2705.1, C2706.1, C2707.1, C2708.1, C2709.1, R2702.1, R2703.1, R2704.1, R2705.1, R2706.1, R2707.1, R2708.1, R2709.1, R2710.1, U2701.1 (VCC), U2701.5 (VCC), U2702.1 (VCC), U2702.5 (VCC), U2703.1 (VCC), U2703.5 (VCC), U2704.1 (VCC), U2704.5 (VCC), U2705.1 (VCC), U2705.5 (VCC), U2706.1 (VCC), U2706.5 (VCC), U2707.1 (VCC), U2707.5 (VCC), U2708.3 (VCC), U2708.5 (VCC), U2709.3 (VCC), U2709.5 (VCC)
BATT_LOWBAT: U2703.6
GND: C2701.2, C2702.2, C2703.2, C2704.2, C2705.2, C2706.2, C2707.2, C2708.2, C2709.2, R2701.2, U2701.2 (GND), U2702.2 (GND), U2703.2 (GND), U2704.2 (GND), U2705.2 (GND), U2706.2 (GND), U2707.2 (GND), U2708.2 (GND), U2709.2 (GND)
unnamed: D2701.1 (K), U2701.4
unnamed: D2701.2 (A), R2702.2
unnamed: D2702.1 (K), U2702.4
unnamed: D2702.2 (A), R2703.2
unnamed: D2703.1 (K), U2703.4
unnamed: D2703.2 (A), R2704.2
unnamed: D2704.1 (K), U2704.4
unnamed: D2704.2 (A), R2705.2
unnamed: D2705.1 (K), U2705.4
unnamed: D2705.2 (A), R2706.2
unnamed: D2706.1 (K), U2706.4
unnamed: D2706.2 (A), R2707.2
unnamed: D2707.1 (K), U2707.4
unnamed: D2707.2 (A), R2708.2
unnamed: D2708.1 (K), U2708.4
unnamed: D2708.2 (A), R2709.2
unnamed: D2709.1 (K), U2709.4
unnamed: D2709.2 (A), R2710.2
PGOOD_LED_SHDN: R2701.1, U2701.3, U2702.3, U2703.3, U2704.3, U2705.3, U2706.3, U2707.3, U2708.1, U2709.1
POS1P2_PGOOD: U2705.6
POS1P8_PGOOD: U2702.6
POS2P8_PGOOD: U2706.6
POS3P0_PGOOD: U2704.6
POS3P3_USB_PGOOD: U2707.6
POS12_PGOOD: U2701.6
~BATT_CHG: U2709.6
~BATT_FLT: U2708.6
