drewsum/Thermal_Camera/rev_a/hdw/Thermal_Camera/PIC32MZ_DA_1.kicad_sch

## KiCad design rev_a/hdw/Thermal_Camera/PIC32MZ_DA_1.kicad_sch (2024-10-11)

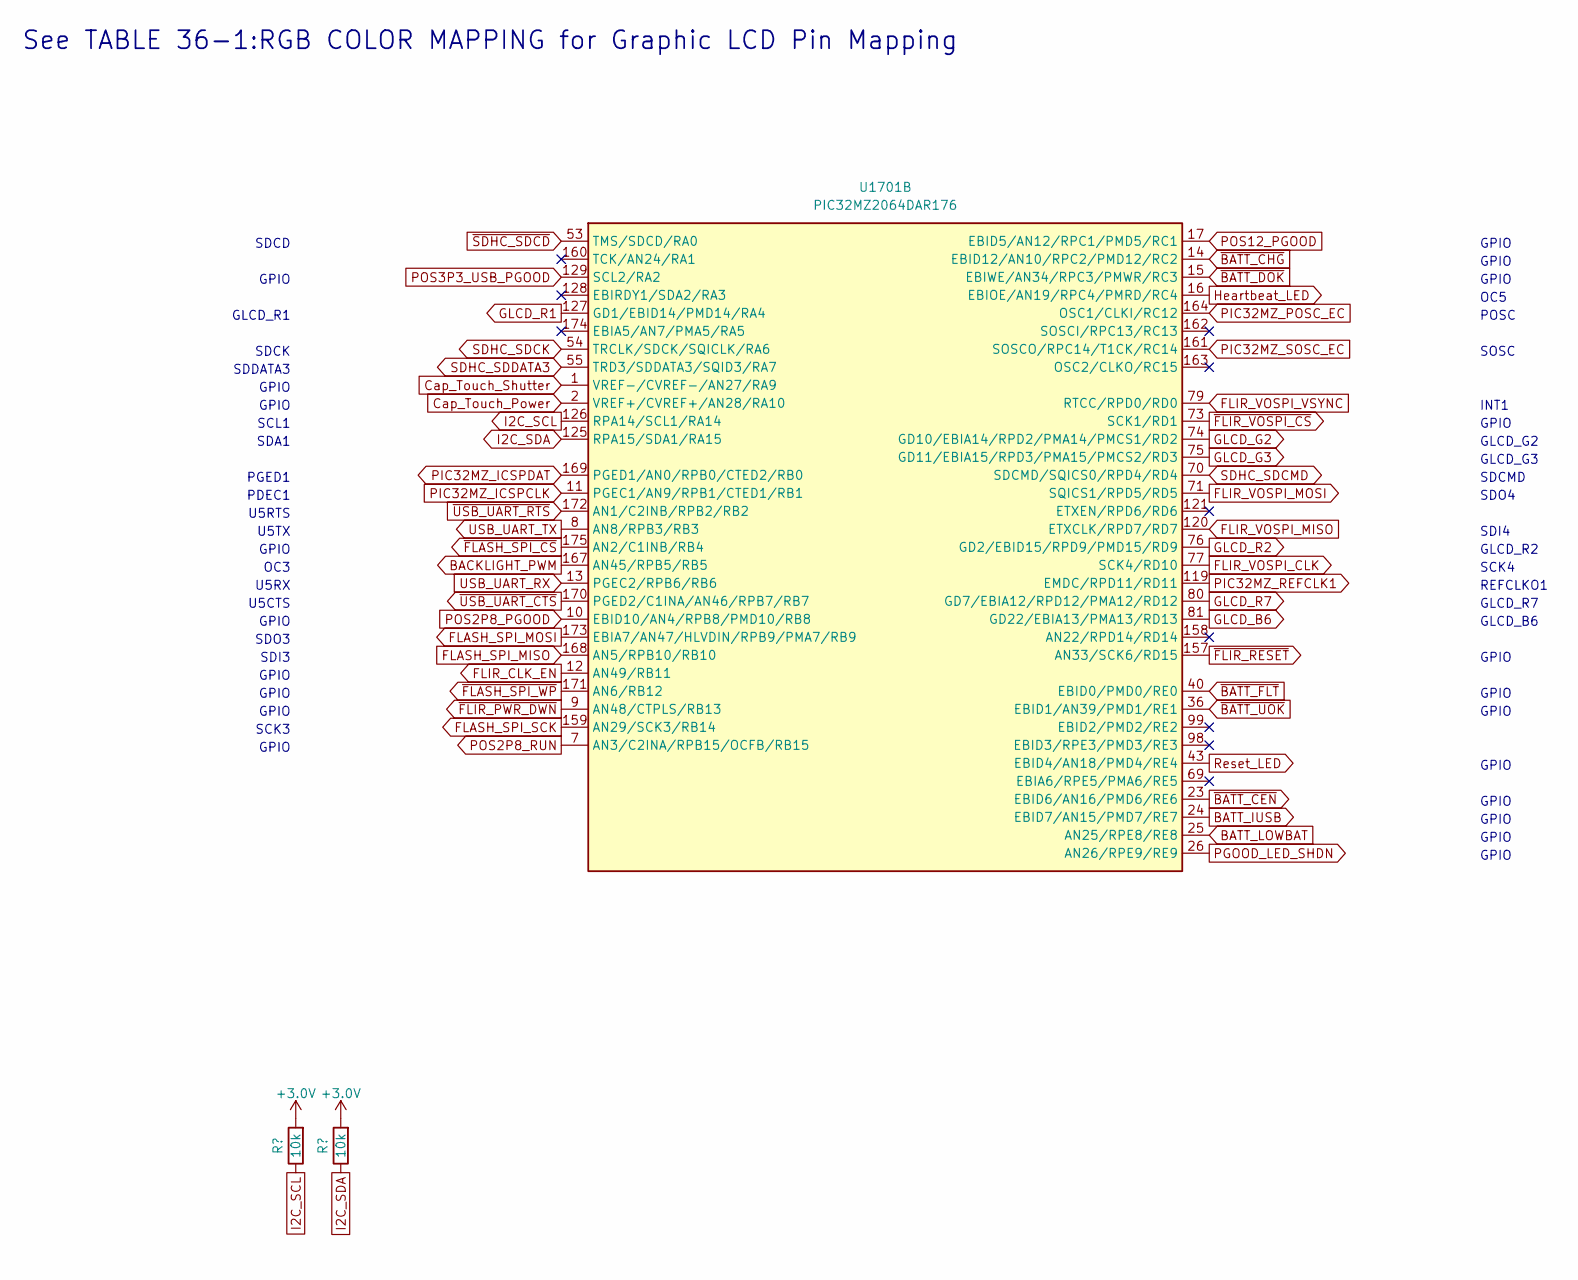
[picture p14: schematic PIC32MZ_DA_1.kicad_sch]

Parts:
R1801, R1802: 10k; R_0402; Tolerance 1%; Digi-Key PN RMCF0402FT10K0CT-ND
U1701: PIC32MZ2064DAR176; LQFP-176_20x20mm_P0.4mm_7p9x7p9mm_EP; Digi-Key PN PIC32MZ2064DAR176-I/2J-ND

Connections:
+3.0V: R1801.1, R1802.1
BACKLIGHT_PWM: U1701.167 (AN45/RPB5/RB5)
BATT_IUSB: U1701.24 (EBID7/AN15/PMD7/RE7)
BATT_LOWBAT: U1701.25 (AN25/RPE8/RE8)
Cap_Touch_Power: U1701.2 (VREF+/CVREF+/AN28/RA10)
Cap_Touch_Shutter: U1701.1 (VREF-/CVREF-/AN27/RA9)
FLASH_SPI_MISO: U1701.168 (AN5/RPB10/RB10)
FLASH_SPI_MOSI: U1701.173 (EBIA7/AN47/HLVDIN/RPB9/PMA7/RB9)
FLASH_SPI_SCK: U1701.159 (AN29/SCK3/RB14)
FLIR_CLK_EN: U1701.12 (AN49/RB11)
FLIR_VOSPI_CLK: U1701.77 (SCK4/RD10)
FLIR_VOSPI_MISO: U1701.120 (ETXCLK/RPD7/RD7)
FLIR_VOSPI_MOSI: U1701.71 (SQICS1/RPD5/RD5)
FLIR_VOSPI_VSYNC: U1701.79 (RTCC/RPD0/RD0)
GLCD_B6: U1701.81 (GD22/EBIA13/PMA13/RD13)
GLCD_G2: U1701.74 (GD10/EBIA14/RPD2/PMA14/PMCS1/RD2)
GLCD_G3: U1701.75 (GD11/EBIA15/RPD3/PMA15/PMCS2/RD3)
GLCD_R1: U1701.127 (GD1/EBID14/PMD14/RA4)
GLCD_R2: U1701.76 (GD2/EBID15/RPD9/PMD15/RD9)
GLCD_R7: U1701.80 (GD7/EBIA12/RPD12/PMA12/RD12)
Heartbeat_LED: U1701.16 (EBIOE/AN19/RPC4/PMRD/RC4)
I2C_SCL: R1801.2, U1701.126 (RPA14/SCL1/RA14)
I2C_SDA: R1802.2, U1701.125 (RPA15/SDA1/RA15)
PGOOD_LED_SHDN: U1701.26 (AN26/RPE9/RE9)
PIC32MZ_ICSPCLK: U1701.11 (PGEC1/AN9/RPB1/CTED1/RB1)
PIC32MZ_ICSPDAT: U1701.169 (PGED1/AN0/RPB0/CTED2/RB0)
PIC32MZ_POSC_EC: U1701.164 (OSC1/CLKI/RC12)
PIC32MZ_REFCLK1: U1701.119 (EMDC/RPD11/RD11)
PIC32MZ_SOSC_EC: U1701.161 (SOSCO/RPC14/T1CK/RC14)
POS2P8_PGOOD: U1701.10 (EBID10/AN4/RPB8/PMD10/RB8)
POS2P8_RUN: U1701.7 (AN3/C2INA/RPB15/OCFB/RB15)
POS3P3_USB_PGOOD: U1701.129 (SCL2/RA2)
POS12_PGOOD: U1701.17 (EBID5/AN12/RPC1/PMD5/RC1)
Reset_LED: U1701.43 (EBID4/AN18/PMD4/RE4)
SDHC_SDCK: U1701.54 (TRCLK/SDCK/SQICLK/RA6)
SDHC_SDCMD: U1701.70 (SDCMD/SQICS0/RPD4/RD4)
SDHC_SDDATA3: U1701.55 (TRD3/SDDATA3/SQID3/RA7)
USB_UART_RX: U1701.13 (PGEC2/RPB6/RB6)
USB_UART_TX: U1701.8 (AN8/RPB3/RB3)
~BATT_CEN: U1701.23 (EBID6/AN16/PMD6/RE6)
~BATT_CHG: U1701.14 (EBID12/AN10/RPC2/PMD12/RC2)
~BATT_DOK: U1701.15 (EBIWE/AN34/RPC3/PMWR/RC3)
~BATT_FLT: U1701.40 (EBID0/PMD0/RE0)
~BATT_UOK: U1701.36 (EBID1/AN39/PMD1/RE1)
~FLASH_SPI_CS: U1701.175 (AN2/C1INB/RB4)
~FLASH_SPI_WP: U1701.171 (AN6/RB12)
~FLIR_PWR_DWN: U1701.9 (AN48/CTPLS/RB13)
~FLIR_RESET: U1701.157 (AN33/SCK6/RD15)
~FLIR_VOSPI_CS: U1701.73 (SCK1/RD1)
~SDHC_SDCD: U1701.53 (TMS/SDCD/RA0)
~USB_UART_CTS: U1701.170 (PGED2/C1INA/AN46/RPB7/RB7)
~USB_UART_RTS: U1701.172 (AN1/C2INB/RPB2/RB2)

Notes on the sheet:
PGED1
GPIO
POSC
U5TX
U5CTS
SCK4
SDCMD
OC5
SOSC
SDO3
SDCK
SCL1
OC3
GLCD_G3
GLCD_B6
SDI3
REFCLKO1
U5RTS
U5RX
SDI4
SDDATA3
INT1
GLCD_R2
GLCD_G2
PDEC1
SDCD
GLCD_R7
SDO4
GLCD_R1
SCK3
SDA1
See TABLE 36-1:RGB COLOR MAPPING for Graphic LCD Pin Mapping
