drewsum/Thermal_Camera/rev_a/hdw/Thermal_Camera/PIC32MZ_DA_Clocking.kicad_sch

## KiCad design rev_a/hdw/Thermal_Camera/PIC32MZ_DA_Clocking.kicad_sch (2024-10-11)

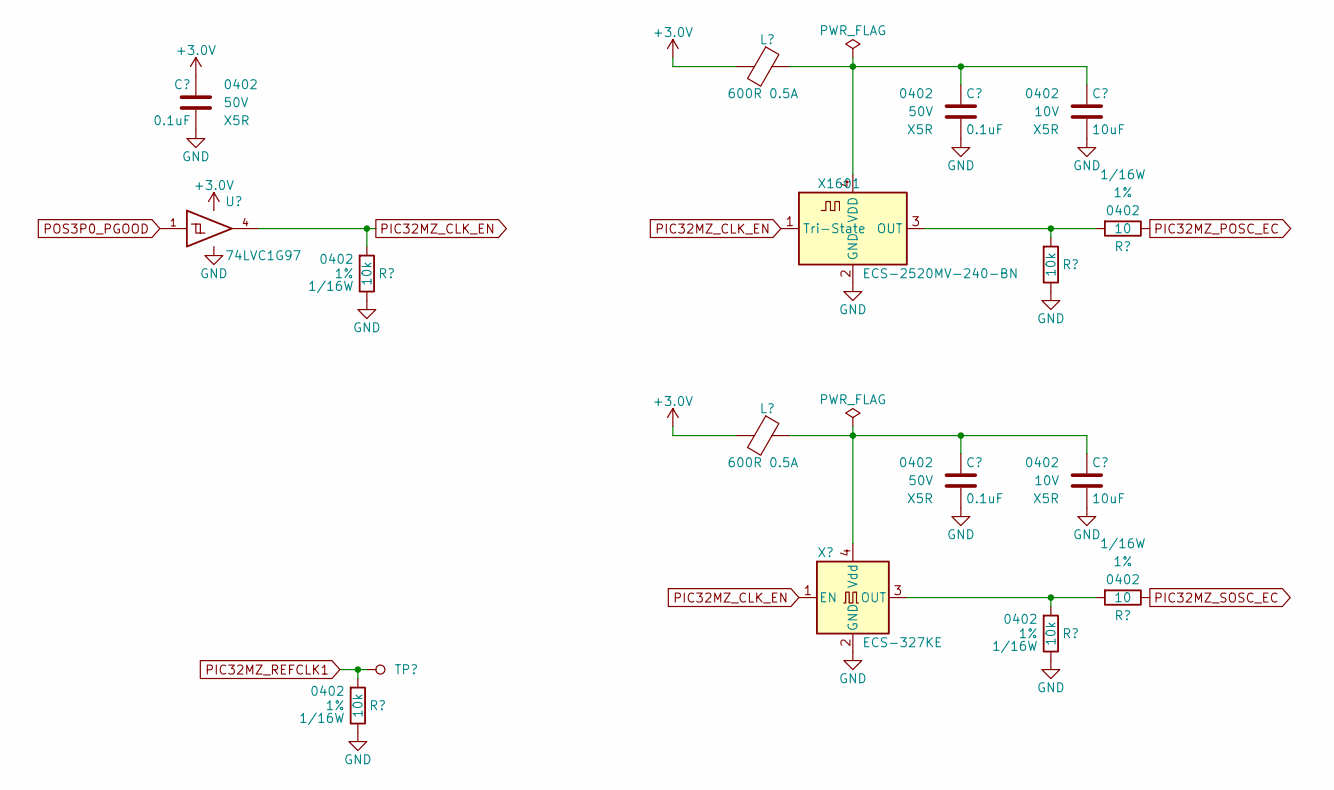
[picture p15: schematic PIC32MZ_DA_Clocking.kicad_sch]

Parts:
C1601, C1602, C1603: 0.1uF; C_0402; Voltage 50V; Digi-Key PN 490-10697-1-ND
C1604, C1605: 10uF; C_0402; Voltage 10V; Digi-Key PN 490-GRM155R61A106ME11DCT-ND
L1601, L1602: 600R 0.5A; L_0402
R1601, R1602, R1603, R1604: 10k; R_0402; Tolerance 1%; Digi-Key PN RMCF0402FT10K0CT-ND
R1605, R1606: 10; R_0402; Tolerance 1%; Digi-Key PN RMCF0402FT10R0CT-ND
TP1601: TP; Test_Point
U1601: 74LVC1G97; SOT-363_SC-70-6; Digi-Key PN 296-15582-1-ND
X1601: ECS-2520MV-240-BN; Oscillator_SMD_ECS_2520MV-xxx-xx-4Pin_2.5x2.0mm; Digi-Key PN XC2750CT-ND
X1602: ECS-327KE; Digi-Key PN XC1751CT-ND

Connections:
+3.0V: C1601.1, L1601.2, L1602.2, U1601.5 (VCC)
GND: C1601.2, C1602.2, C1603.2, C1604.2, C1605.2, R1601.2, R1602.2, R1603.2, R1604.2, U1601.2 (GND), U1601.3 (GND), U1601.6 (GND), X1601.2 (GND), X1602.2 (GND)
unnamed: C1602.1, C1604.1, L1601.1, X1601.4 (VDD)
unnamed: C1603.1, C1605.1, L1602.1, X1602.4 (Vdd)
unnamed: R1603.1, R1605.1, X1601.3 (OUT)
unnamed: R1604.1, R1606.1, X1602.3 (OUT)
PIC32MZ_CLK_EN: R1602.1, U1601.4, X1601.1 (Tri-State), X1602.1 (EN)
PIC32MZ_POSC_EC: R1605.2
PIC32MZ_REFCLK1: R1601.1, TP1601.1
PIC32MZ_SOSC_EC: R1606.2
POS3P0_PGOOD: U1601.1
