drewsum/Thermal_Camera/rev_a/hdw/Thermal_Camera/PIC32MZ_DA_Power.kicad_sch

## KiCad design rev_a/hdw/Thermal_Camera/PIC32MZ_DA_Power.kicad_sch (2024-10-11)

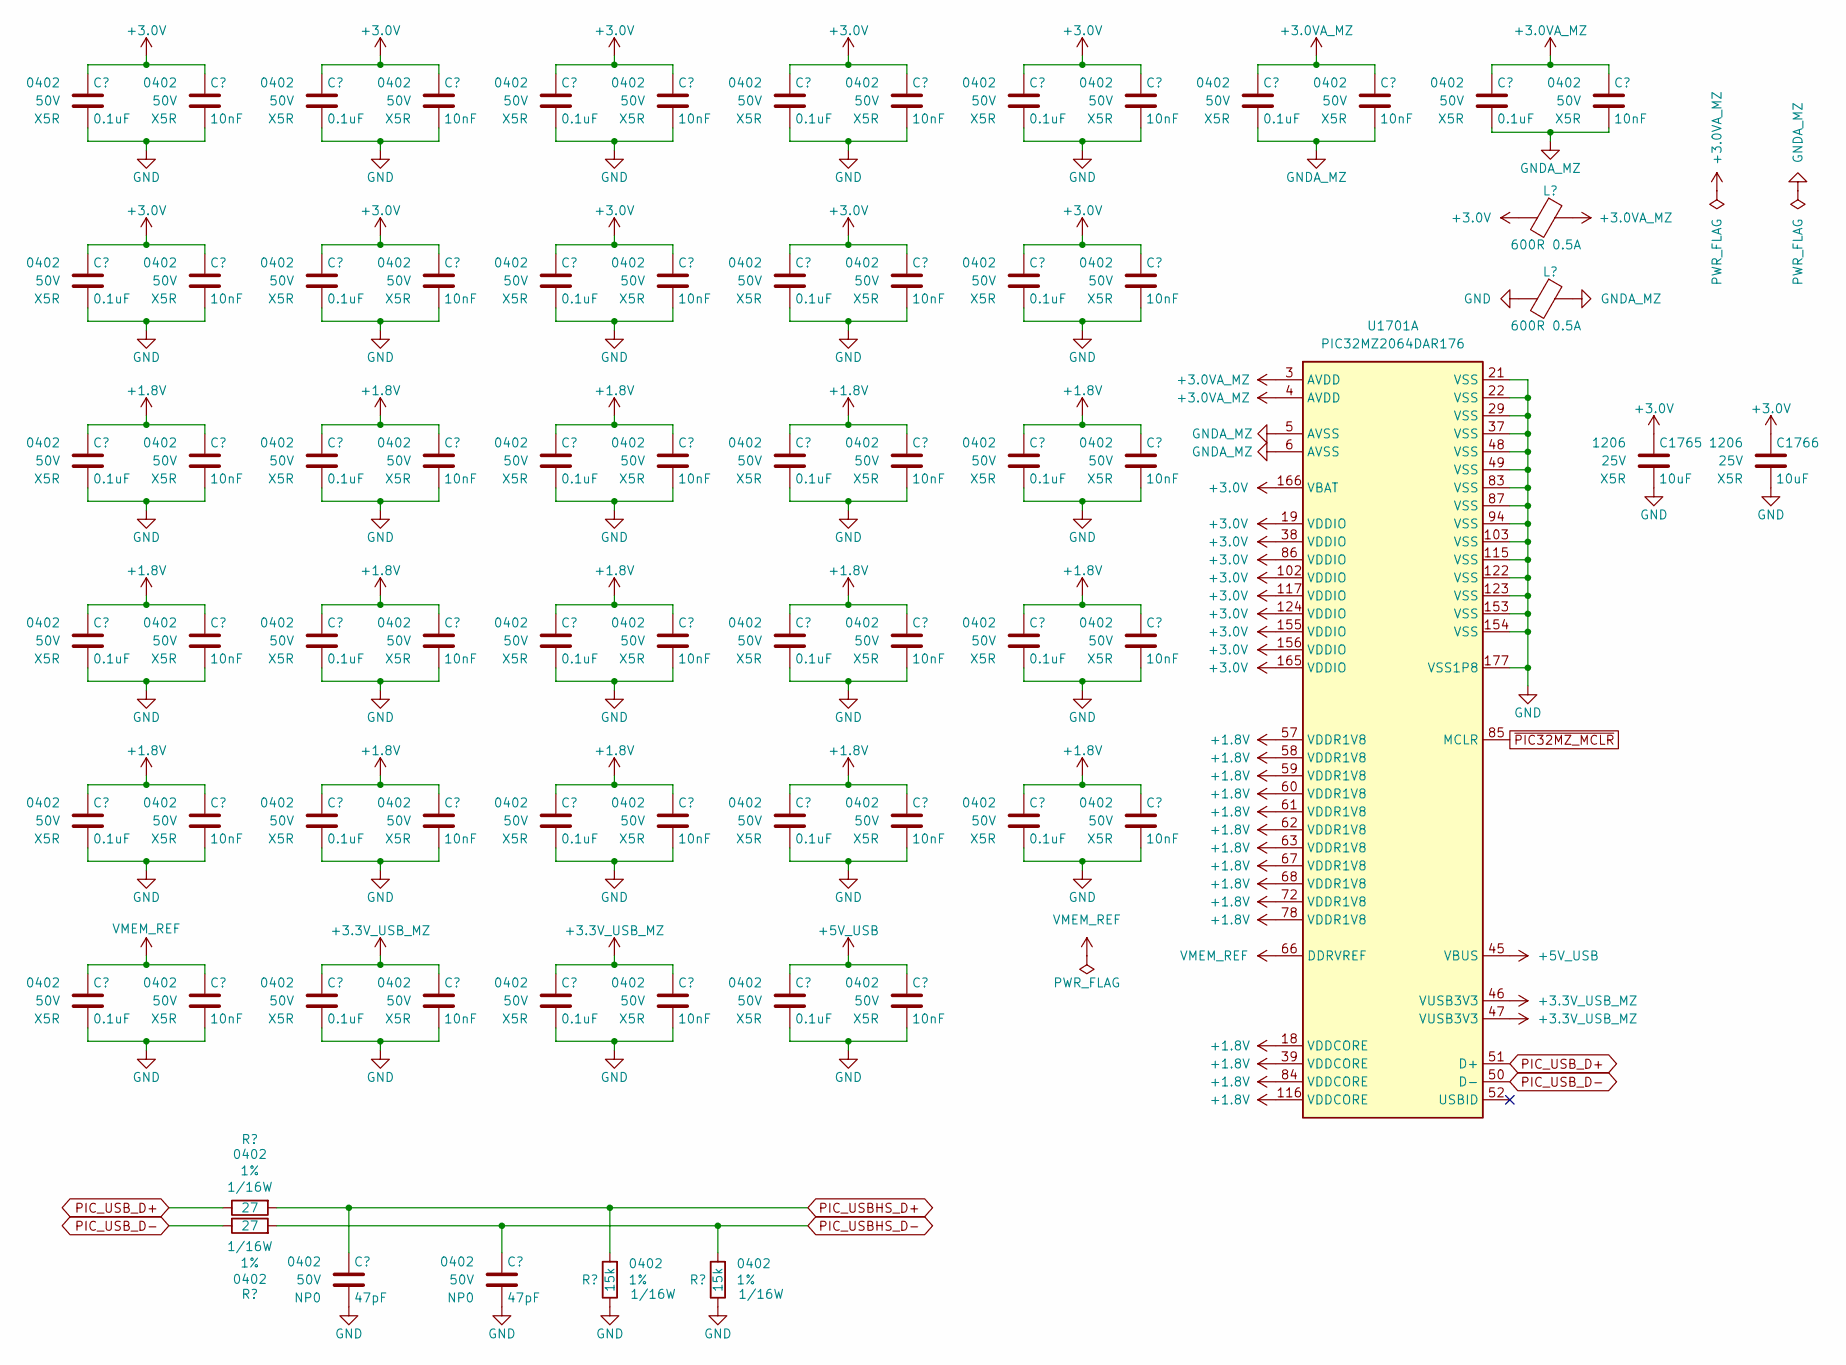
[picture p16: schematic PIC32MZ_DA_Power.kicad_sch]

Parts:
C1701, C1702, C1703, C1704, C1705, C1706, C1713, C1714, C1715, C1716, C1717, C1718, C1727, C1728, C1729, C1730, C1731, C1732, C1739, C1740, C1741, C1742, C1743, C1744, C1751, C1752, C1753, C1754, C1755, C1761, C1763: 0.1uF; C_0402; Voltage 50V; Digi-Key PN 490-10697-1-ND
C1707, C1708, C1709, C1710, C1711, C1712, C1720, C1721, C1722, C1723, C1724, C1725, C1733, C1734, C1735, C1736, C1737, C1738, C1745, C1746, C1747, C1748, C1749, C1750, C1756, C1757, C1758, C1759, C1760, C1762, C1764: 10nF; C_0402; Voltage 50V; Digi-Key PN 445-12201-1-ND
C1719, C1726: 47pF; C_0402; Voltage 50V; Digi-Key PN 490-5942-1-ND
C1765, C1766: 10uF; C_1206; Voltage 25V; Digi-Key PN 399-8153-1-ND
L1701, L1702: 600R 0.5A; L_0402
R1701, R1702: 27; R_0402; Tolerance 1%; Digi-Key PN RMCF0402FT27R0CT-ND
R1703, R1704: 15k; R_0402; Tolerance 1%; Digi-Key PN RMCF0402FT15K0CT-ND
U1701: PIC32MZ2064DAR176; LQFP-176_20x20mm_P0.4mm_7p9x7p9mm_EP; Digi-Key PN PIC32MZ2064DAR176-I/2J-ND

Connections:
+1.8V: C1703.1, C1704.1, C1705.1, C1709.1, C1710.1, C1711.1, C1715.1, C1716.1, C1717.1, C1722.1, C1723.1, C1724.1, C1729.1, C1730.1, C1731.1, C1735.1, C1736.1, C1737.1, C1741.1, C1742.1, C1743.1, C1747.1, C1748.1, C1749.1, C1753.1, C1754.1, C1755.1, C1758.1, C1759.1, C1760.1, U1701.18 (VDDCORE), U1701.39 (VDDCORE), U1701.57 (VDDR1V8), U1701.58 (VDDR1V8), U1701.59 (VDDR1V8), U1701.60 (VDDR1V8), U1701.61 (VDDR1V8), U1701.62 (VDDR1V8), U1701.63 (VDDR1V8), U1701.67 (VDDR1V8), U1701.68 (VDDR1V8), U1701.72 (VDDR1V8), U1701.78 (VDDR1V8), U1701.84 (VDDCORE), U1701.116 (VDDCORE)
+3.0V: C1701.1, C1702.1, C1707.1, C1708.1, C1713.1, C1714.1, C1720.1, C1721.1, C1727.1, C1728.1, C1733.1, C1734.1, C1739.1, C1740.1, C1745.1, C1746.1, C1751.1, C1752.1, C1756.1, C1757.1, C1765.1, C1766.1, L1701.2, U1701.19 (VDDIO), U1701.38 (VDDIO), U1701.86 (VDDIO), U1701.102 (VDDIO), U1701.117 (VDDIO), U1701.124 (VDDIO), U1701.155 (VDDIO), U1701.156 (VDDIO), U1701.165 (VDDIO), U1701.166 (VBAT)
+3.0VA_MZ: C1761.1, C1762.1, C1763.1, C1764.1, L1701.1, U1701.3 (AVDD), U1701.4 (AVDD)
+3.3V_USB_MZ: C1718.1, C1725.1, C1732.1, C1738.1, U1701.46 (VUSB3V3), U1701.47 (VUSB3V3)
+5V_USB: C1744.1, C1750.1, U1701.45 (VBUS)
GND: C1701.2, C1702.2, C1703.2, C1704.2, C1705.2, C1706.2, C1707.2, C1708.2, C1709.2, C1710.2, C1711.2, C1712.2, C1713.2, C1714.2, C1715.2, C1716.2, C1717.2, C1718.2, C1719.2, C1720.2, C1721.2, C1722.2, C1723.2, C1724.2, C1725.2, C1726.2, C1727.2, C1728.2, C1729.2, C1730.2, C1731.2, C1732.2, C1733.2, C1734.2, C1735.2, C1736.2, C1737.2, C1738.2, C1739.2, C1740.2, C1741.2, C1742.2, C1743.2, C1744.2, C1745.2, C1746.2, C1747.2, C1748.2, C1749.2, C1750.2, C1751.2, C1752.2, C1753.2, C1754.2, C1755.2, C1756.2, C1757.2, C1758.2, C1759.2, C1760.2, C1765.2, C1766.2, L1702.2, R1703.2, R1704.2, U1701.21 (VSS), U1701.22 (VSS), U1701.29 (VSS), U1701.37 (VSS), U1701.48 (VSS), U1701.49 (VSS), U1701.83 (VSS), U1701.87 (VSS), U1701.94 (VSS), U1701.103 (VSS), U1701.115 (VSS), U1701.122 (VSS), U1701.123 (VSS), U1701.153 (VSS), U1701.154 (VSS), U1701.177 (VSS1P8)
GNDA_MZ: C1761.2, C1762.2, C1763.2, C1764.2, L1702.1, U1701.5 (AVSS), U1701.6 (AVSS)
PIC_USBHS_D+: C1719.1, R1701.1, R1703.1
PIC_USBHS_D-: C1726.1, R1702.1, R1704.1
PIC_USB_D+: R1701.2, U1701.51 (D+)
PIC_USB_D-: R1702.2, U1701.50 (D-)
VMEM_REF: C1706.1, C1712.1, U1701.66 (DDRVREF)
~PIC32MZ_MCLR: U1701.85 (MCLR)
