drewsum/Thermal_Camera/rev_a/hdw/Thermal_Camera/PIC32MZ_DA_Programming.kicad_sch

## KiCad design rev_a/hdw/Thermal_Camera/PIC32MZ_DA_Programming.kicad_sch (2024-10-11)

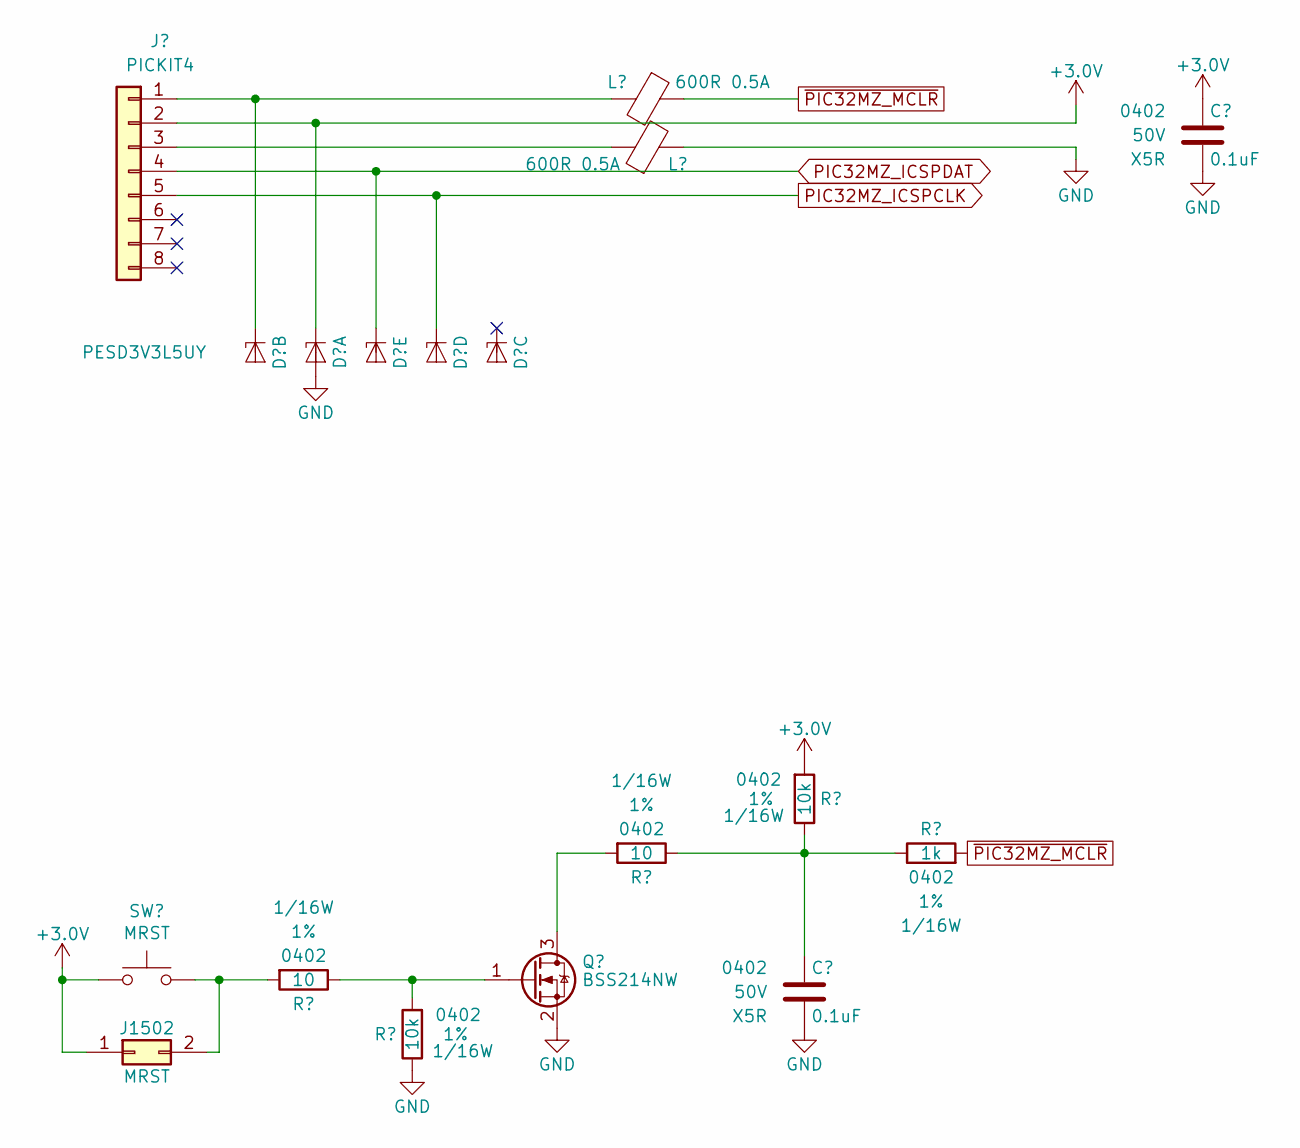
[picture p17: schematic PIC32MZ_DA_Programming.kicad_sch]

Parts:
C1501, C1502: 0.1uF; C_0402; Voltage 50V; Digi-Key PN 490-10697-1-ND
D1501: PESD3V3L5UY; SOT-363_SC-70-6; Digi-Key PN 1727-3828-1-ND
J1501: PICKIT4; PICKIT4_Header
J1502: MRST; PinHeader_1x02_P2.54mm_Vertical
L1501, L1502: 600R 0.5A; L_0402
Q1501: BSS214NW; SOT-323_SC-70; Digi-Key PN BSS214NWH6327XTSA1CT-ND
R1501, R1503: 10; R_0402; Tolerance 1%; Digi-Key PN RMCF0402FT10R0CT-ND
R1502, R1504: 10k; R_0402; Tolerance 1%; Digi-Key PN RMCF0402FT10K0CT-ND
R1505: 1k; R_0402; Tolerance 1%; Digi-Key PN RMCF0402FT1K00CT-ND
SW1501: MRST; SW_PUSH_6mm

Connections:
+3.0V: C1502.1, D1501.1 (K1), J1501.2, J1502.1, R1504.1, SW1501.1
GND: C1501.2, C1502.2, D1501.2 (A), L1502.2, Q1501.2 (S), R1502.2
unnamed: C1501.1, R1503.2, R1504.2, R1505.2
unnamed: D1501.3 (K2), J1501.1, L1501.2
unnamed: J1501.3, L1502.1
unnamed: J1502.2, R1501.1, SW1501.2
unnamed: Q1501.1 (G), R1501.2, R1502.1
unnamed: Q1501.3 (D), R1503.1
PIC32MZ_ICSPCLK: D1501.5 (K4), J1501.5
PIC32MZ_ICSPDAT: D1501.6 (K5), J1501.4
~PIC32MZ_MCLR: L1501.1, R1505.1
