drewsum/Thermal_Camera/rev_a/hdw/Thermal_Camera/POS1P2_Power_Supply.kicad_sch

## KiCad design rev_a/hdw/Thermal_Camera/POS1P2_Power_Supply.kicad_sch (2024-10-11)

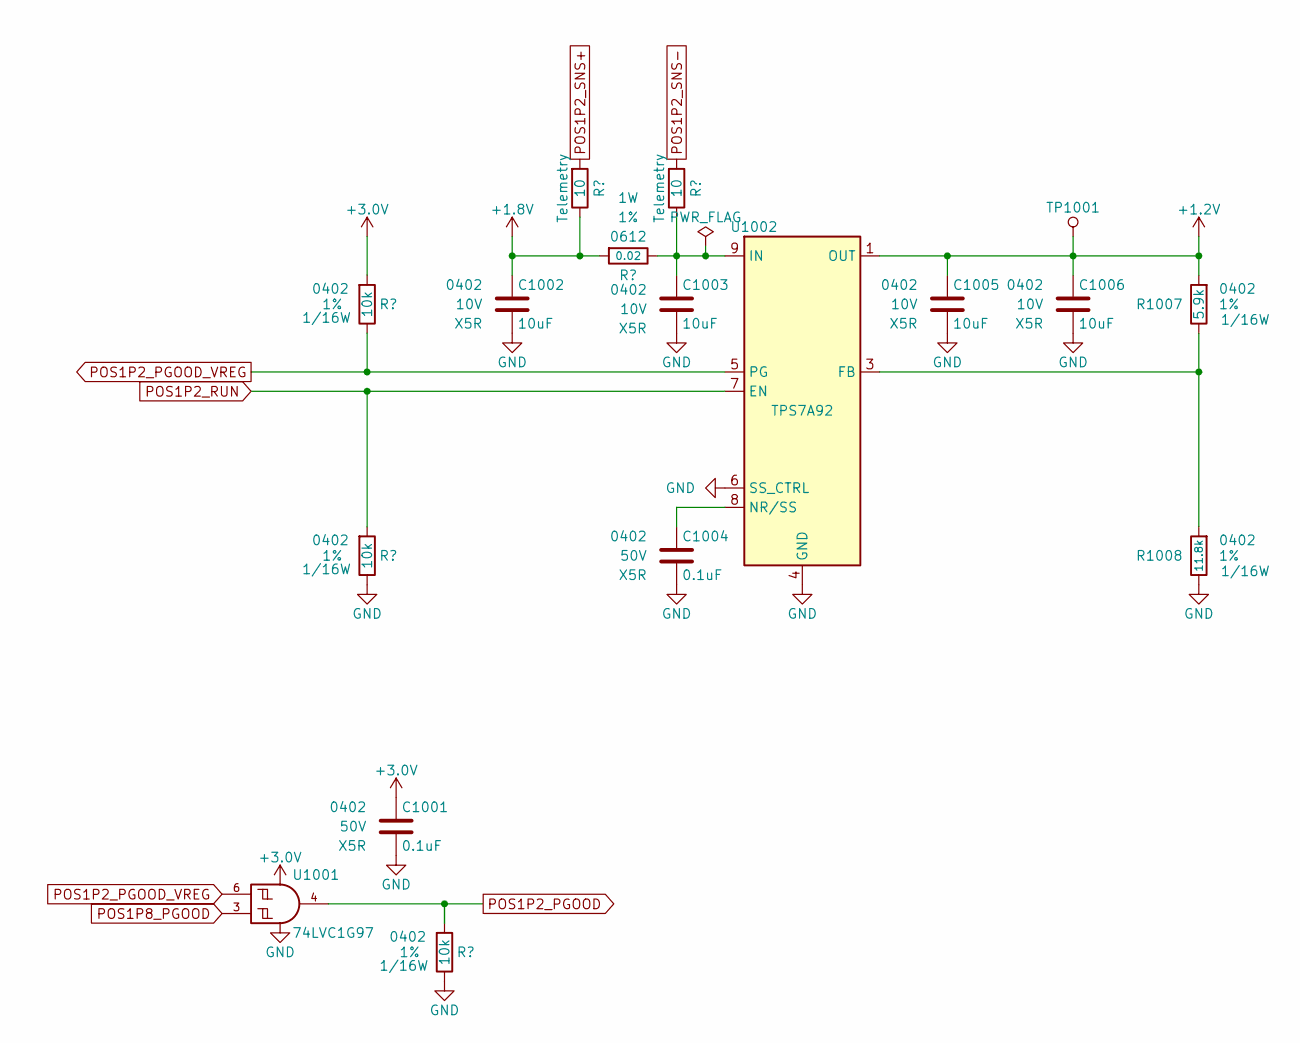
[picture p18: schematic POS1P2_Power_Supply.kicad_sch]

Parts:
C1001, C1004: 0.1uF; C_0402; Voltage 50V; Digi-Key PN 490-10697-1-ND
C1002, C1003, C1005, C1006: 10uF; C_0402; Voltage 10V; Digi-Key PN 490-GRM155R61A106ME11DCT-ND
R1001, R1002, R1003: 10k; R_0402; Tolerance 1%; Digi-Key PN RMCF0402FT10K0CT-ND
R1004, R1006: 10; R_0402; Tolerance 1%; Digi-Key PN RMCF0402FT10R0CT-ND
R1005: 0.02; R_0612; Tolerance 1%; Digi-Key PN P16010CT-ND
R1007: 5.9k; R_0402; Tolerance 1%; Digi-Key PN RMCF0402FT5K90CT-ND
R1008: 11.8k; R_0402; Tolerance 1%; Digi-Key PN RMCF0402FT11K8CT-ND
TP1001: TP; Test_Point
U1001: 74LVC1G97; SOT-363_SC-70-6; Digi-Key PN 296-15582-1-ND
U1002: TPS7A92; Texas_S-PDSO-N10_EP1.2x2mm; Digi-Key PN TPS7A9201DSKR

Connections:
+1.2V: C1005.1, C1006.1, R1007.1, TP1001.1, U1002.1 (OUT), U1002.2 (OUT)
+1.8V: C1002.1, R1004.2, R1005.1
+3.0V: C1001.1, R1001.1, U1001.5 (VCC)
GND: C1001.2, C1002.2, C1003.2, C1004.2, C1005.2, C1006.2, R1002.2, R1003.2, R1008.2, U1001.1 (GND), U1001.2 (GND), U1002.4 (GND), U1002.6 (SS_CTRL), U1002.11 (GND)
unnamed: C1003.1, R1005.2, R1006.2, U1002.9 (IN), U1002.10 (IN)
unnamed: C1004.1, U1002.8 (NR/SS)
unnamed: R1007.2, R1008.1, U1002.3 (FB)
POS1P2_PGOOD: R1003.1, U1001.4
POS1P2_PGOOD_VREG: R1001.2, U1001.6, U1002.5 (PG)
POS1P2_RUN: R1002.1, U1002.7 (EN)
POS1P2_SNS+: R1004.1
POS1P2_SNS-: R1006.1
POS1P8_PGOOD: U1001.3
