drewsum/Thermal_Camera/rev_a/hdw/Thermal_Camera/POS1P2_Telemetry.kicad_sch

## KiCad design rev_a/hdw/Thermal_Camera/POS1P2_Telemetry.kicad_sch (2024-10-11)

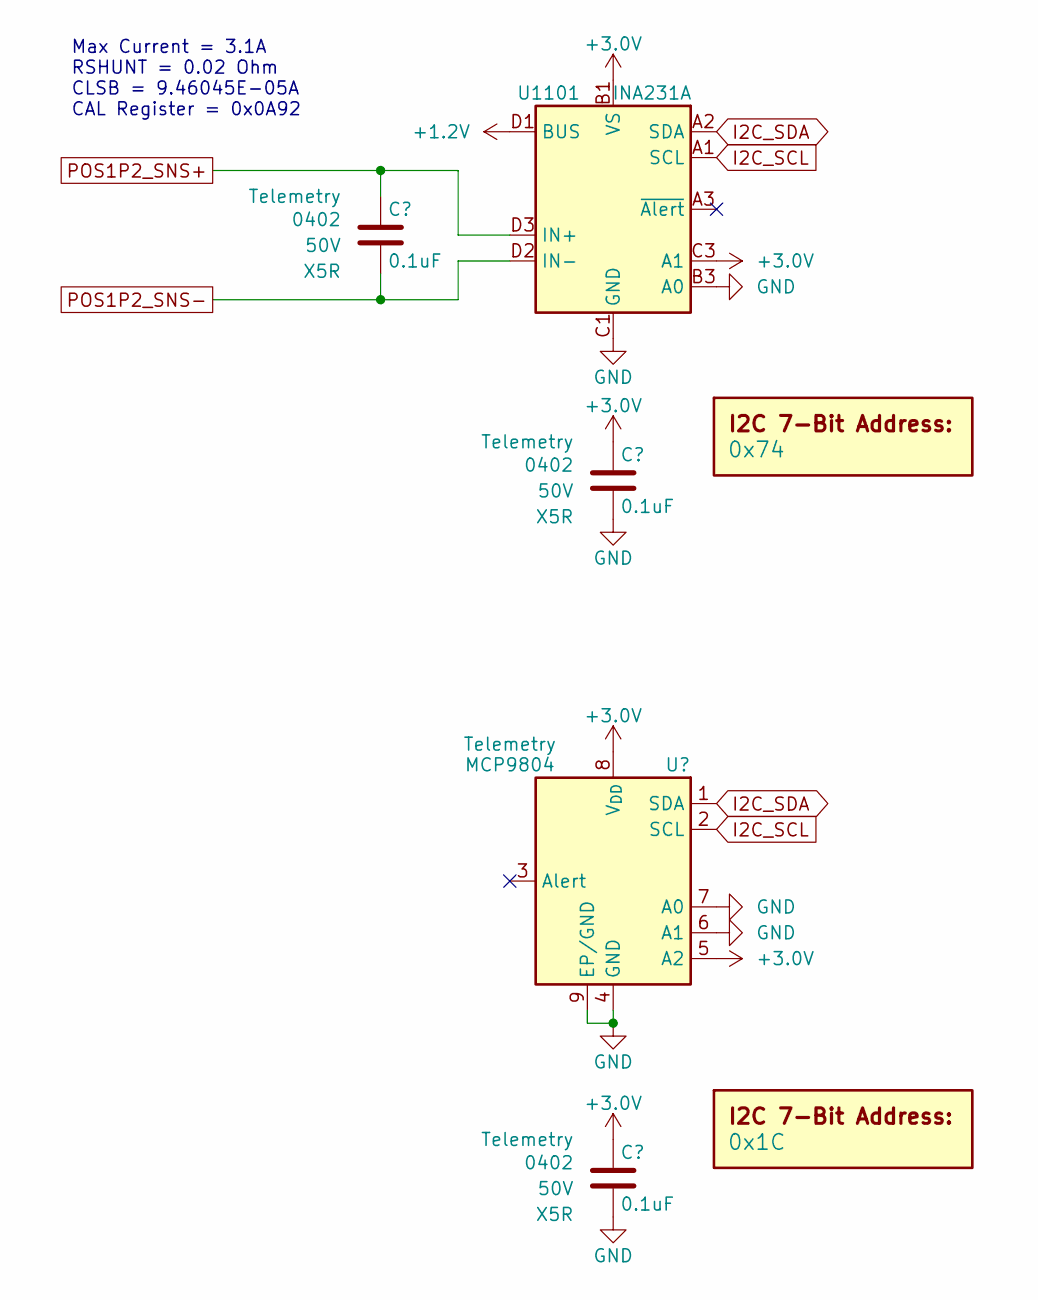
[picture p19: schematic POS1P2_Telemetry.kicad_sch]

Parts:
C1101, C1102, C1103: 0.1uF; C_0402; Voltage 50V; Digi-Key PN 490-10697-1-ND
DOC1101: 0x74
DOC1102: 0x1C
U1101: INA231A; Texas_DSBGA-12_1.65x1.39mm_Layout3x4_P0.4mm; Digi-Key PN 296-41263-1-ND
U1102: MCP9804; DFN-8-1EP_3x2mm_P0.5mm_EP1.3x1.5mm; Digi-Key PN MCP9804T-E/MCCT-ND

Connections:
+1.2V: U1101.D1 (BUS)
+3.0V: C1102.1, C1103.1, U1101.B1 (VS), U1101.C3 (A1), U1102.5 (A2), U1102.8 (V_{DD})
GND: C1102.2, C1103.2, U1101.B3 (A0), U1101.C1 (GND), U1102.4 (GND), U1102.6 (A1), U1102.7 (A0), U1102.9 (EP/GND)
I2C_SCL: U1101.A1 (SCL), U1102.2 (SCL)
I2C_SDA: U1101.A2 (SDA), U1102.1 (SDA)
POS1P2_SNS+: C1101.1, U1101.D3 (IN+)
POS1P2_SNS-: C1101.2, U1101.D2 (IN-)

Notes on the sheet:
Max Current = 3.1A RSHUNT = 0.02 Ohm CLSB = 9.46045E-05A CAL Register = 0x0A92
