drewsum/Thermal_Camera/rev_a/hdw/Thermal_Camera/POS1P8_Power_Supply.kicad_sch

## KiCad design rev_a/hdw/Thermal_Camera/POS1P8_Power_Supply.kicad_sch (2024-10-11)

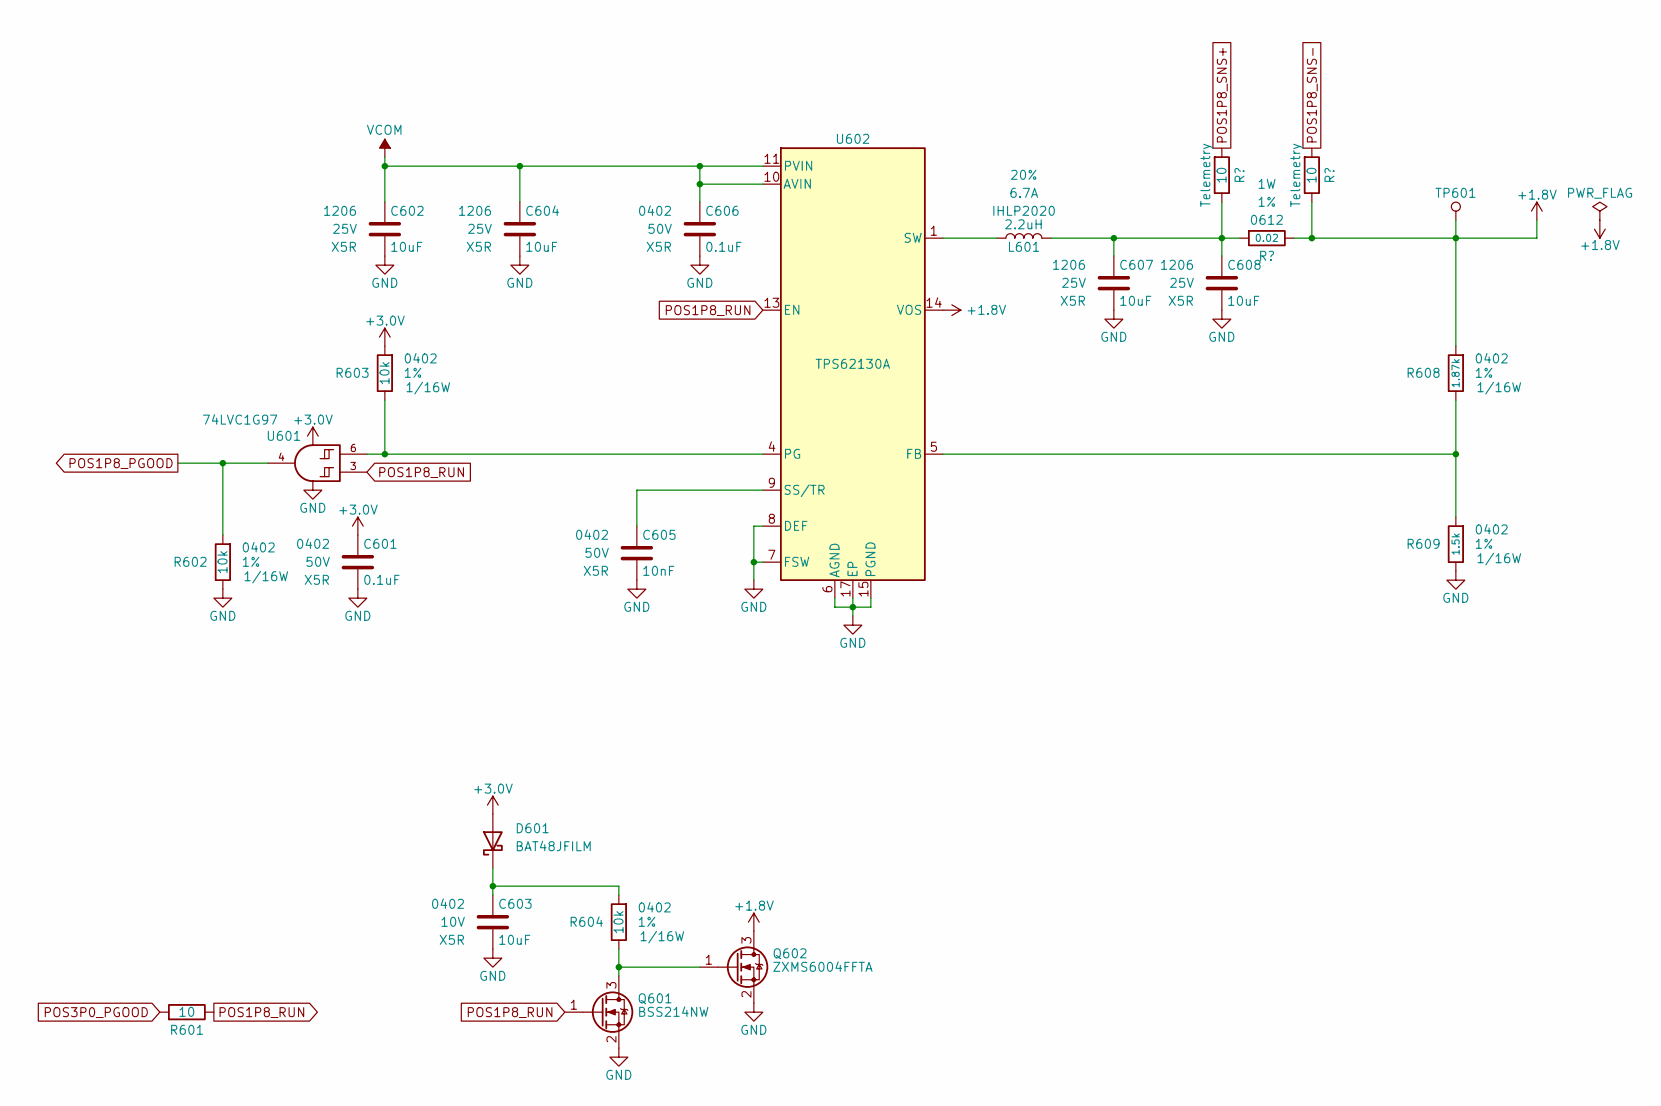
[picture p20: schematic POS1P8_Power_Supply.kicad_sch]

Parts:
C601, C606: 0.1uF; C_0402; Voltage 50V; Digi-Key PN 490-10697-1-ND
C602, C604, C607, C608: 10uF; C_1206; Voltage 25V; Digi-Key PN 399-8153-1-ND
C603: 10uF; C_0402; Voltage 10V; Digi-Key PN 490-GRM155R61A106ME11DCT-ND
C605: 10nF; C_0402; Voltage 50V; Digi-Key PN 445-12201-1-ND
D601: BAT48JFILM; D_SOD-323; Digi-Key PN 497-5711-1-ND
L601: 2.2uH; L_Vishay_IHLP-2020; Tolerance 20%; Digi-Key PN 541-1236-1-ND
Q601: BSS214NW; SOT-323_SC-70; Digi-Key PN BSS214NWH6327XTSA1CT-ND
Q602: ZXMS6004FFTA; SOT-23; Digi-Key PN ZXMS6004FFCT-ND
R601, R605, R607: 10; R_0402; Tolerance 1%; Digi-Key PN RMCF0402FT10R0CT-ND
R602, R603, R604: 10k; R_0402; Tolerance 1%; Digi-Key PN RMCF0402FT10K0CT-ND
R606: 0.02; R_0612; Tolerance 1%; Digi-Key PN P16010CT-ND
R608: 1.87k; R_0402; Tolerance 1%; Digi-Key PN RMCF0402FT1K87CT-ND
R609: 1.5k; R_0402; Tolerance 1%; Digi-Key PN RMCF0402FT1K50CT-ND
TP601: TP; Test_Point
U601: 74LVC1G97; SOT-363_SC-70-6; Digi-Key PN 296-15582-1-ND
U602: TPS62130A; QFN-16-1EP_3x3mm_P0.5mm_EP1.75x1.75mm; Digi-Key PN 296-39446-1-ND

Connections:
+1.8V: Q602.3 (D), R606.2, R607.2, R608.1, TP601.1, U602.14 (VOS)
+3.0V: C601.1, D601.2 (A), R603.1, U601.5 (VCC)
GND: C601.2, C602.2, C603.2, C604.2, C605.2, C606.2, C607.2, C608.2, Q601.2 (S), Q602.2 (S), R602.2, R609.2, U601.1 (GND), U601.2 (GND), U602.6 (AGND), U602.7 (FSW), U602.8 (DEF), U602.15 (PGND), U602.16 (PGND), U602.17 (EP)
unnamed: C603.1, D601.1 (K), R604.1
unnamed: C605.1, U602.9 (SS/TR)
unnamed: C607.1, C608.1, L601.2, R605.2, R606.1
unnamed: L601.1, U602.1 (SW), U602.2 (SW), U602.3 (SW)
unnamed: Q601.3 (D), Q602.1 (G), R604.2
unnamed: R603.2, U601.6, U602.4 (PG)
unnamed: R608.2, R609.1, U602.5 (FB)
POS1P8_PGOOD: R602.1, U601.4
POS1P8_RUN: Q601.1 (G), R601.2, U601.3, U602.13 (EN)
POS1P8_SNS+: R605.1
POS1P8_SNS-: R607.1
POS3P0_PGOOD: R601.1
VCOM: C602.1, C604.1, C606.1, U602.10 (AVIN), U602.11 (PVIN), U602.12 (PVIN)
