drewsum/Thermal_Camera/rev_a/hdw/Thermal_Camera/POS1P8_Telemetry.kicad_sch

## KiCad design rev_a/hdw/Thermal_Camera/POS1P8_Telemetry.kicad_sch (2024-10-11)

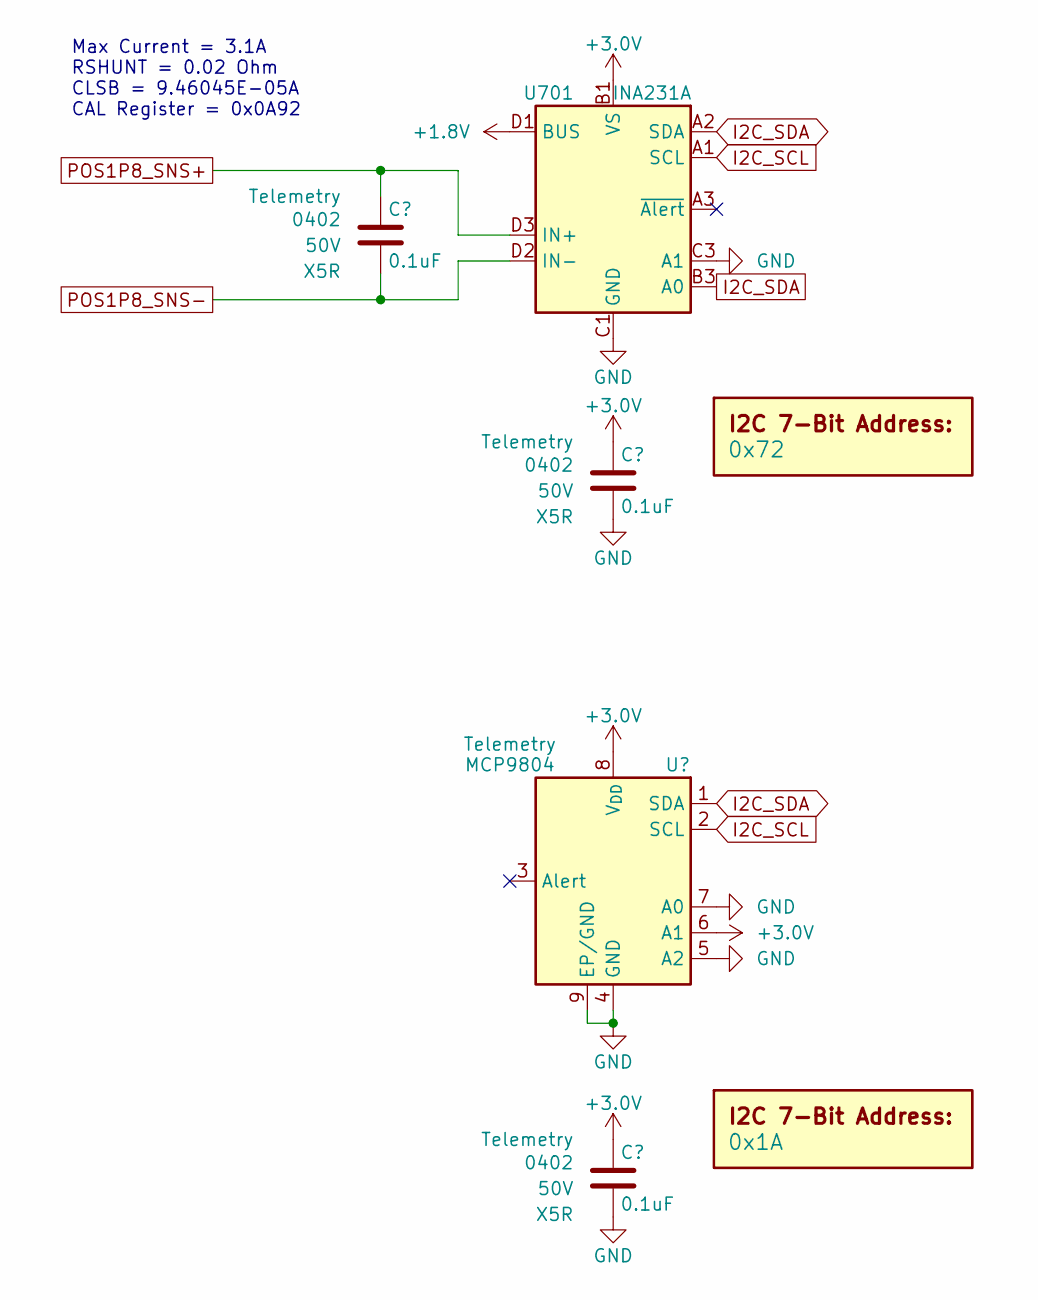
[picture p21: schematic POS1P8_Telemetry.kicad_sch]

Parts:
C701, C702, C703: 0.1uF; C_0402; Voltage 50V; Digi-Key PN 490-10697-1-ND
DOC701: 0x72
DOC702: 0x1A
U701: INA231A; Texas_DSBGA-12_1.65x1.39mm_Layout3x4_P0.4mm; Digi-Key PN 296-41263-1-ND
U702: MCP9804; DFN-8-1EP_3x2mm_P0.5mm_EP1.3x1.5mm; Digi-Key PN MCP9804T-E/MCCT-ND

Connections:
+1.8V: U701.D1 (BUS)
+3.0V: C702.1, C703.1, U701.B1 (VS), U702.6 (A1), U702.8 (V_{DD})
GND: C702.2, C703.2, U701.C1 (GND), U701.C3 (A1), U702.4 (GND), U702.5 (A2), U702.7 (A0), U702.9 (EP/GND)
I2C_SCL: U701.A1 (SCL), U702.2 (SCL)
I2C_SDA: U701.A2 (SDA), U701.B3 (A0), U702.1 (SDA)
POS1P8_SNS+: C701.1, U701.D3 (IN+)
POS1P8_SNS-: C701.2, U701.D2 (IN-)

Notes on the sheet:
Max Current = 3.1A RSHUNT = 0.02 Ohm CLSB = 9.46045E-05A CAL Register = 0x0A92
