drewsum/Thermal_Camera/rev_a/hdw/Thermal_Camera/POS2P8_Power_Supply.kicad_sch

## KiCad design rev_a/hdw/Thermal_Camera/POS2P8_Power_Supply.kicad_sch (2024-10-11)

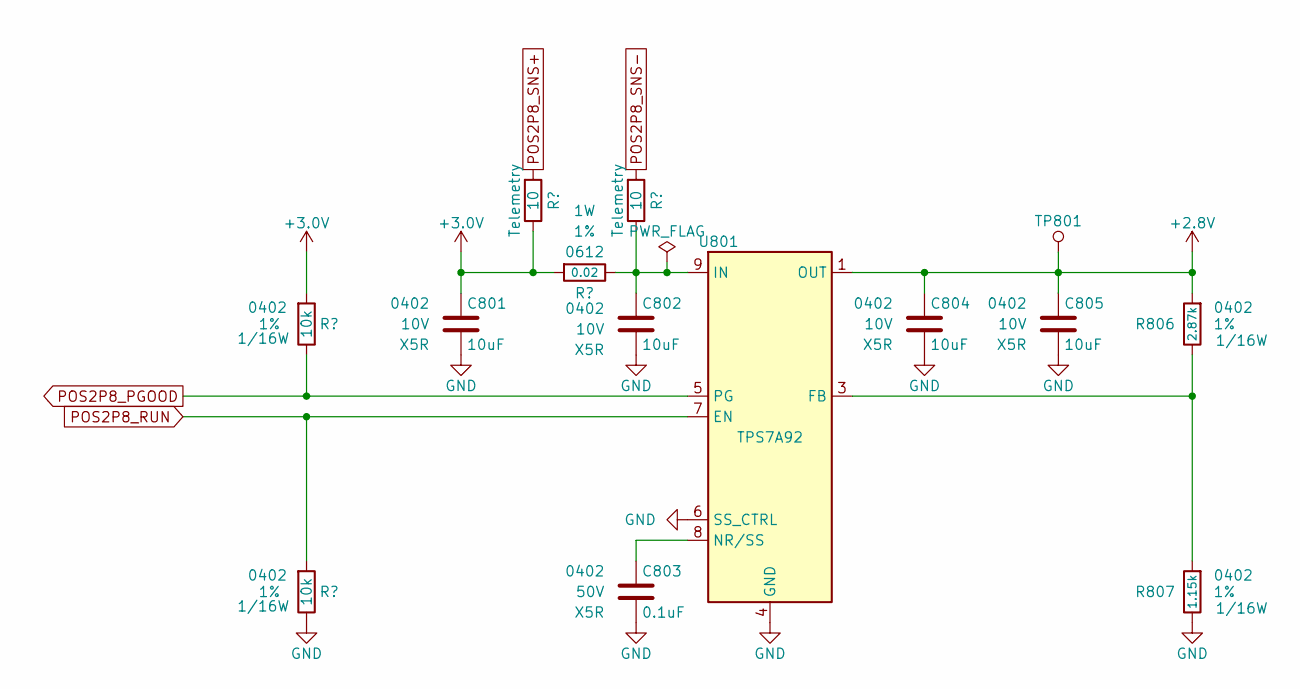
[picture p22: schematic POS2P8_Power_Supply.kicad_sch]

Parts:
C801, C802, C804, C805: 10uF; C_0402; Voltage 10V; Digi-Key PN 490-GRM155R61A106ME11DCT-ND
C803: 0.1uF; C_0402; Voltage 50V; Digi-Key PN 490-10697-1-ND
R801, R802: 10k; R_0402; Tolerance 1%; Digi-Key PN RMCF0402FT10K0CT-ND
R803, R805: 10; R_0402; Tolerance 1%; Digi-Key PN RMCF0402FT10R0CT-ND
R804: 0.02; R_0612; Tolerance 1%; Digi-Key PN P16010CT-ND
R806: 2.87k; R_0402; Tolerance 1%; Digi-Key PN RMCF0402FT2K87CT-ND
R807: 1.15k; R_0402; Tolerance 1%; Digi-Key PN RMCF0402FT1K15CT-ND
TP801: TP; Test_Point
U801: TPS7A92; Texas_S-PDSO-N10_EP1.2x2mm; Digi-Key PN TPS7A9201DSKR

Connections:
+2.8V: C804.1, C805.1, R806.1, TP801.1, U801.1 (OUT), U801.2 (OUT)
+3.0V: C801.1, R801.1, R803.2, R804.1
GND: C801.2, C802.2, C803.2, C804.2, C805.2, R802.2, R807.2, U801.4 (GND), U801.6 (SS_CTRL), U801.11 (GND)
unnamed: C802.1, R804.2, R805.2, U801.9 (IN), U801.10 (IN)
unnamed: C803.1, U801.8 (NR/SS)
unnamed: R806.2, R807.1, U801.3 (FB)
POS2P8_PGOOD: R801.2, U801.5 (PG)
POS2P8_RUN: R802.1, U801.7 (EN)
POS2P8_SNS+: R803.1
POS2P8_SNS-: R805.1
