drewsum/Thermal_Camera/rev_a/hdw/Thermal_Camera/POS2P8_Telemetry.kicad_sch

## KiCad design rev_a/hdw/Thermal_Camera/POS2P8_Telemetry.kicad_sch (2024-10-11)

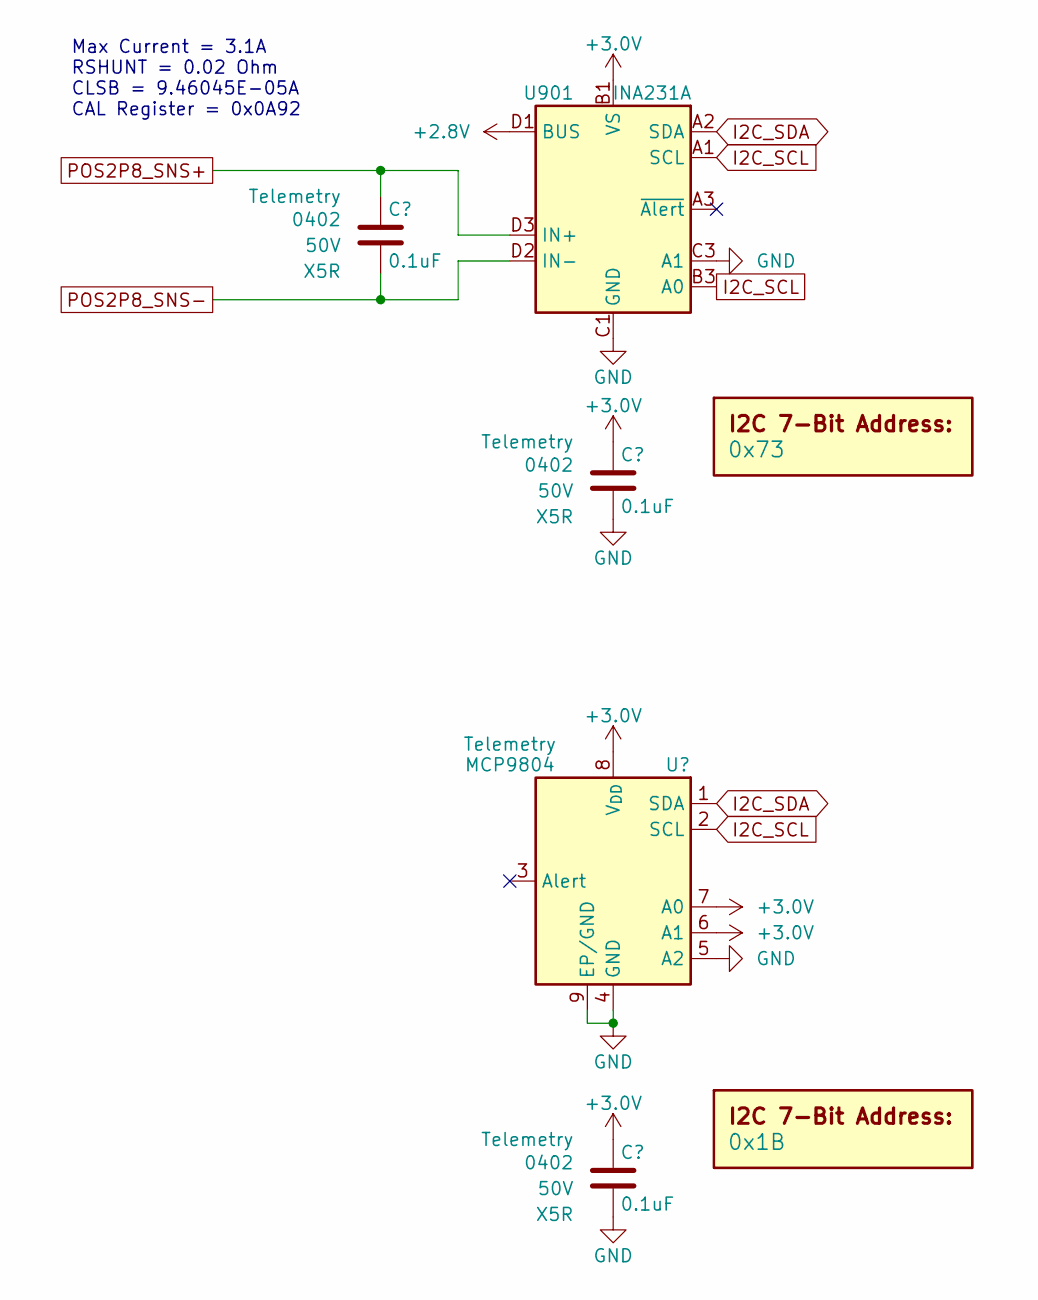
[picture p23: schematic POS2P8_Telemetry.kicad_sch]

Parts:
C901, C902, C903: 0.1uF; C_0402; Voltage 50V; Digi-Key PN 490-10697-1-ND
DOC901: 0x73
DOC902: 0x1B
U901: INA231A; Texas_DSBGA-12_1.65x1.39mm_Layout3x4_P0.4mm; Digi-Key PN 296-41263-1-ND
U902: MCP9804; DFN-8-1EP_3x2mm_P0.5mm_EP1.3x1.5mm; Digi-Key PN MCP9804T-E/MCCT-ND

Connections:
+2.8V: U901.D1 (BUS)
+3.0V: C902.1, C903.1, U901.B1 (VS), U902.6 (A1), U902.7 (A0), U902.8 (V_{DD})
GND: C902.2, C903.2, U901.C1 (GND), U901.C3 (A1), U902.4 (GND), U902.5 (A2), U902.9 (EP/GND)
I2C_SCL: U901.A1 (SCL), U901.B3 (A0), U902.2 (SCL)
I2C_SDA: U901.A2 (SDA), U902.1 (SDA)
POS2P8_SNS+: C901.1, U901.D3 (IN+)
POS2P8_SNS-: C901.2, U901.D2 (IN-)

Notes on the sheet:
Max Current = 3.1A RSHUNT = 0.02 Ohm CLSB = 9.46045E-05A CAL Register = 0x0A92
