drewsum/Thermal_Camera/rev_a/hdw/Thermal_Camera/POS3P0_Power_Supply.kicad_sch

## KiCad design rev_a/hdw/Thermal_Camera/POS3P0_Power_Supply.kicad_sch (2024-10-11)

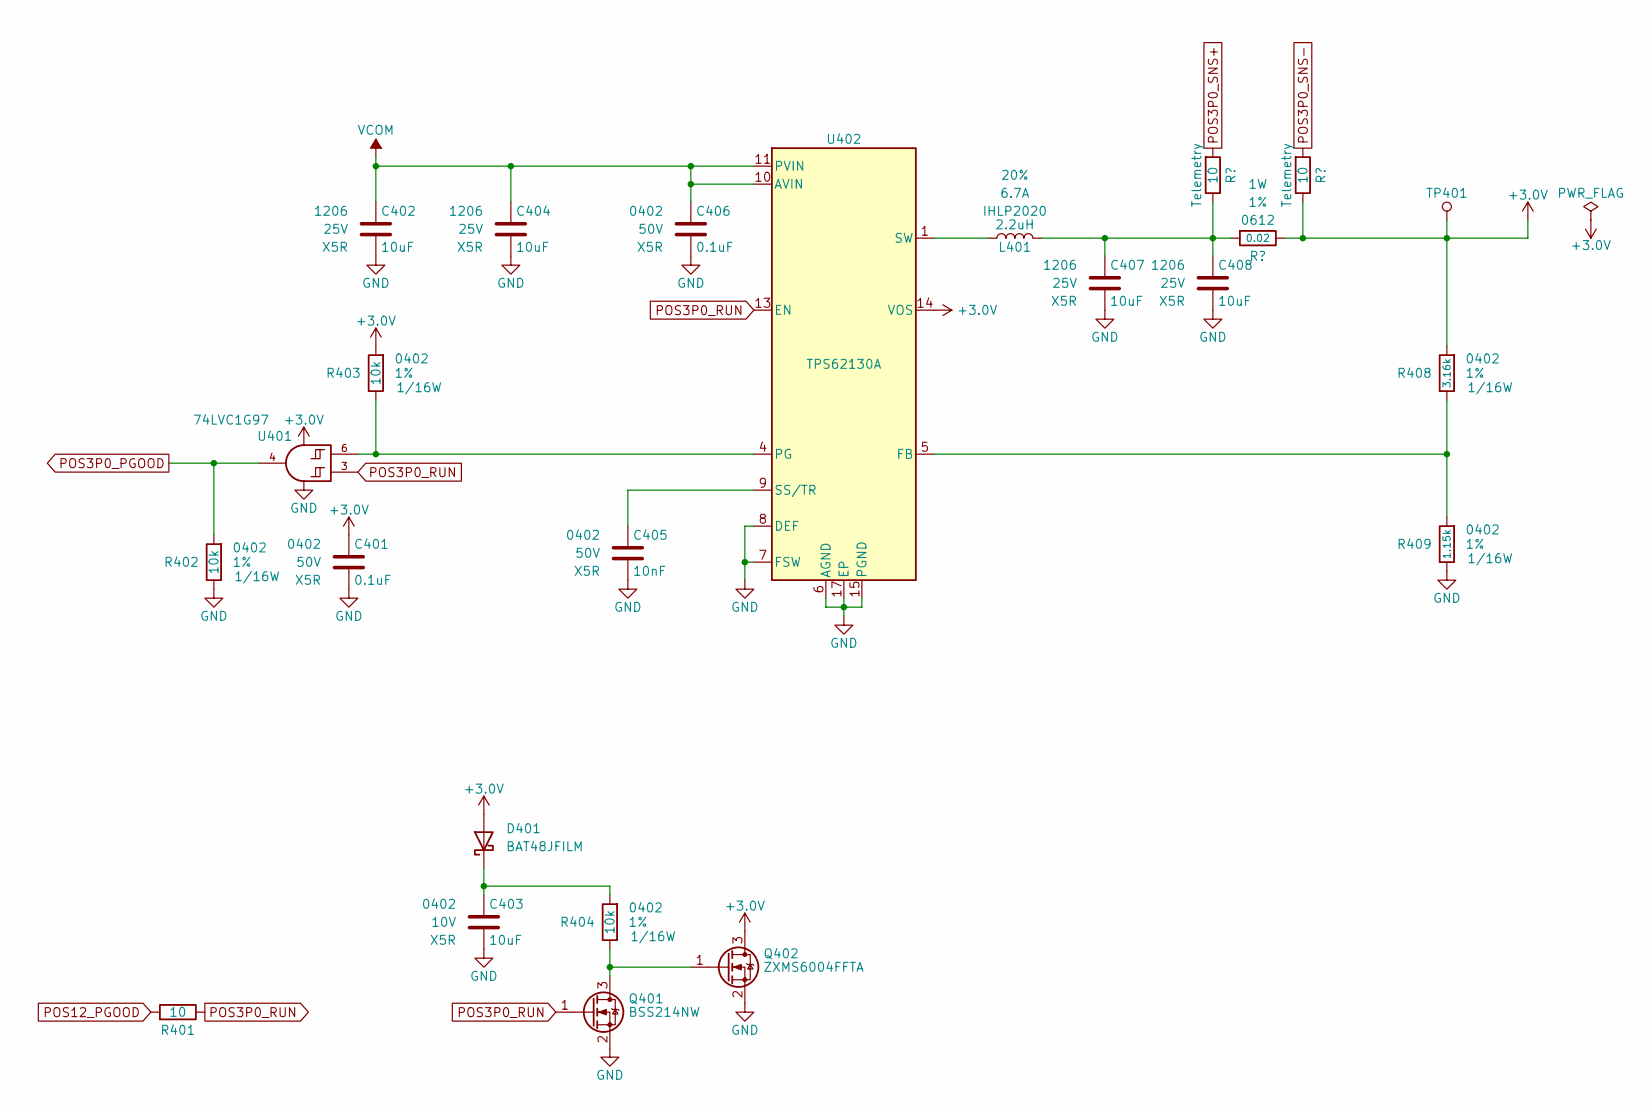
[picture p24: schematic POS3P0_Power_Supply.kicad_sch]

Parts:
C401, C406: 0.1uF; C_0402; Voltage 50V; Digi-Key PN 490-10697-1-ND
C402, C404, C407, C408: 10uF; C_1206; Voltage 25V; Digi-Key PN 399-8153-1-ND
C403: 10uF; C_0402; Voltage 10V; Digi-Key PN 490-GRM155R61A106ME11DCT-ND
C405: 10nF; C_0402; Voltage 50V; Digi-Key PN 445-12201-1-ND
D401: BAT48JFILM; D_SOD-323; Digi-Key PN 497-5711-1-ND
L401: 2.2uH; L_Vishay_IHLP-2020; Tolerance 20%; Digi-Key PN 541-1236-1-ND
Q401: BSS214NW; SOT-323_SC-70; Digi-Key PN BSS214NWH6327XTSA1CT-ND
Q402: ZXMS6004FFTA; SOT-23; Digi-Key PN ZXMS6004FFCT-ND
R401, R405, R407: 10; R_0402; Tolerance 1%; Digi-Key PN RMCF0402FT10R0CT-ND
R402, R403, R404: 10k; R_0402; Tolerance 1%; Digi-Key PN RMCF0402FT10K0CT-ND
R406: 0.02; R_0612; Tolerance 1%; Digi-Key PN P16010CT-ND
R408: 3.16k; R_0402; Tolerance 1%; Digi-Key PN RMCF0402FT3K16CT-ND
R409: 1.15k; R_0402; Tolerance 1%; Digi-Key PN RMCF0402FT1K15CT-ND
TP401: TP; Test_Point
U401: 74LVC1G97; SOT-363_SC-70-6; Digi-Key PN 296-15582-1-ND
U402: TPS62130A; QFN-16-1EP_3x3mm_P0.5mm_EP1.75x1.75mm; Digi-Key PN 296-39446-1-ND

Connections:
+3.0V: C401.1, D401.2 (A), Q402.3 (D), R403.1, R406.2, R407.2, R408.1, TP401.1, U401.5 (VCC), U402.14 (VOS)
GND: C401.2, C402.2, C403.2, C404.2, C405.2, C406.2, C407.2, C408.2, Q401.2 (S), Q402.2 (S), R402.2, R409.2, U401.1 (GND), U401.2 (GND), U402.6 (AGND), U402.7 (FSW), U402.8 (DEF), U402.15 (PGND), U402.16 (PGND), U402.17 (EP)
unnamed: C403.1, D401.1 (K), R404.1
unnamed: C405.1, U402.9 (SS/TR)
unnamed: C407.1, C408.1, L401.2, R405.2, R406.1
unnamed: L401.1, U402.1 (SW), U402.2 (SW), U402.3 (SW)
unnamed: Q401.3 (D), Q402.1 (G), R404.2
unnamed: R403.2, U401.6, U402.4 (PG)
unnamed: R408.2, R409.1, U402.5 (FB)
POS3P0_PGOOD: R402.1, U401.4
POS3P0_RUN: Q401.1 (G), R401.2, U401.3, U402.13 (EN)
POS3P0_SNS+: R405.1
POS3P0_SNS-: R407.1
POS12_PGOOD: R401.1
VCOM: C402.1, C404.1, C406.1, U402.10 (AVIN), U402.11 (PVIN), U402.12 (PVIN)
