drewsum/Thermal_Camera/rev_a/hdw/Thermal_Camera/POS3P0_Telemetry.kicad_sch

## KiCad design rev_a/hdw/Thermal_Camera/POS3P0_Telemetry.kicad_sch (2024-10-11)

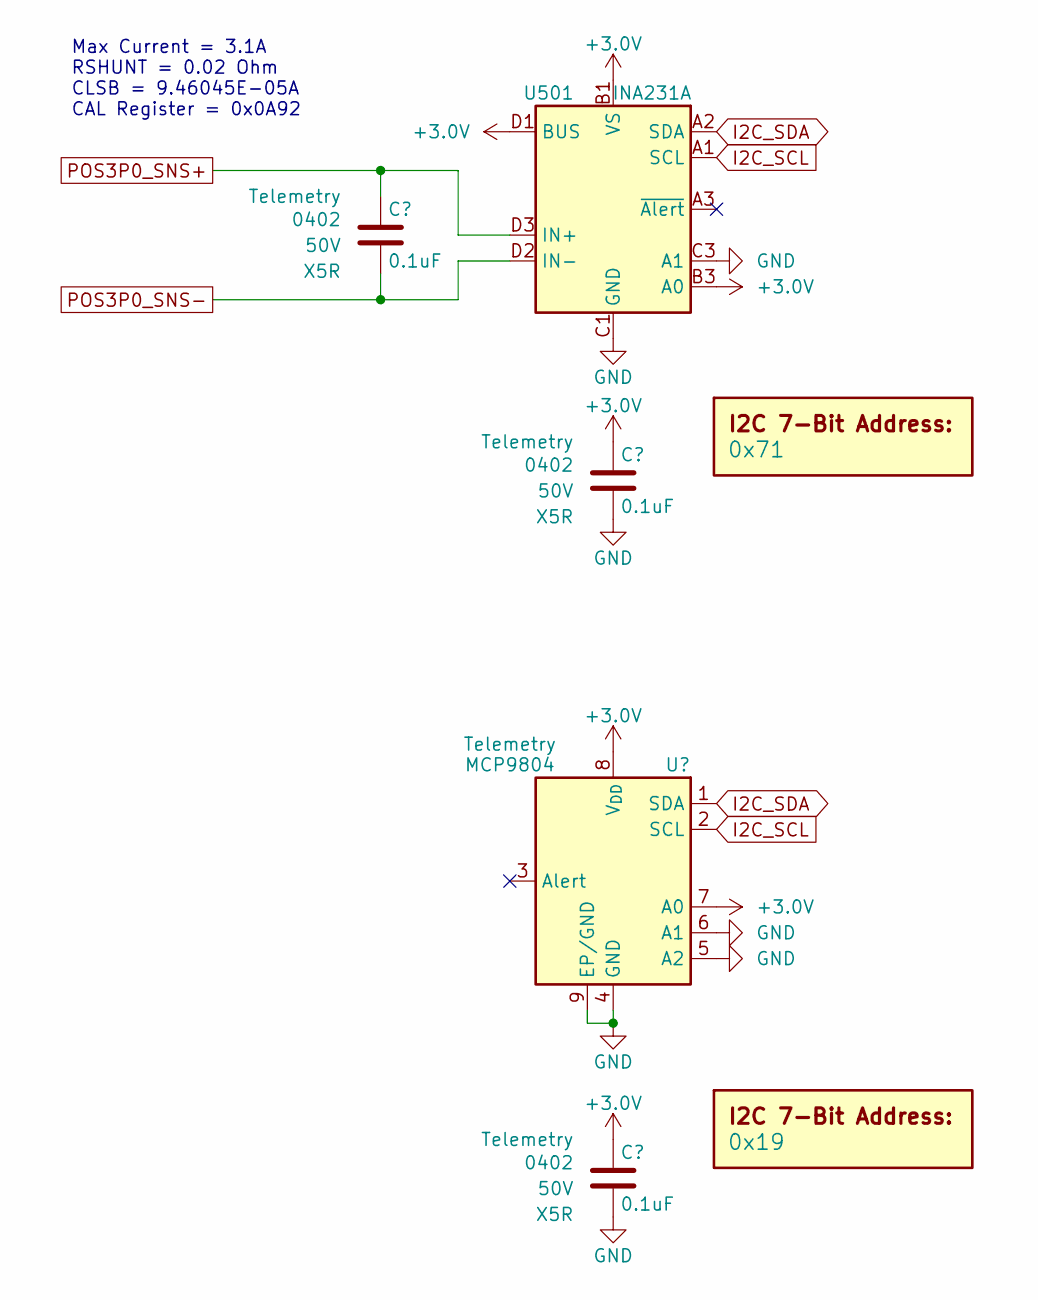
[picture p25: schematic POS3P0_Telemetry.kicad_sch]

Parts:
C501, C502, C503: 0.1uF; C_0402; Voltage 50V; Digi-Key PN 490-10697-1-ND
DOC501: 0x71
DOC502: 0x19
U501: INA231A; Texas_DSBGA-12_1.65x1.39mm_Layout3x4_P0.4mm; Digi-Key PN 296-41263-1-ND
U502: MCP9804; DFN-8-1EP_3x2mm_P0.5mm_EP1.3x1.5mm; Digi-Key PN MCP9804T-E/MCCT-ND

Connections:
+3.0V: C502.1, C503.1, U501.B1 (VS), U501.B3 (A0), U501.D1 (BUS), U502.7 (A0), U502.8 (V_{DD})
GND: C502.2, C503.2, U501.C1 (GND), U501.C3 (A1), U502.4 (GND), U502.5 (A2), U502.6 (A1), U502.9 (EP/GND)
I2C_SCL: U501.A1 (SCL), U502.2 (SCL)
I2C_SDA: U501.A2 (SDA), U502.1 (SDA)
POS3P0_SNS+: C501.1, U501.D3 (IN+)
POS3P0_SNS-: C501.2, U501.D2 (IN-)

Notes on the sheet:
Max Current = 3.1A RSHUNT = 0.02 Ohm CLSB = 9.46045E-05A CAL Register = 0x0A92
