drewsum/Thermal_Camera/rev_a/hdw/Thermal_Camera/POS12_Input.kicad_sch

## KiCad design rev_a/hdw/Thermal_Camera/POS12_Input.kicad_sch (2024-10-11)

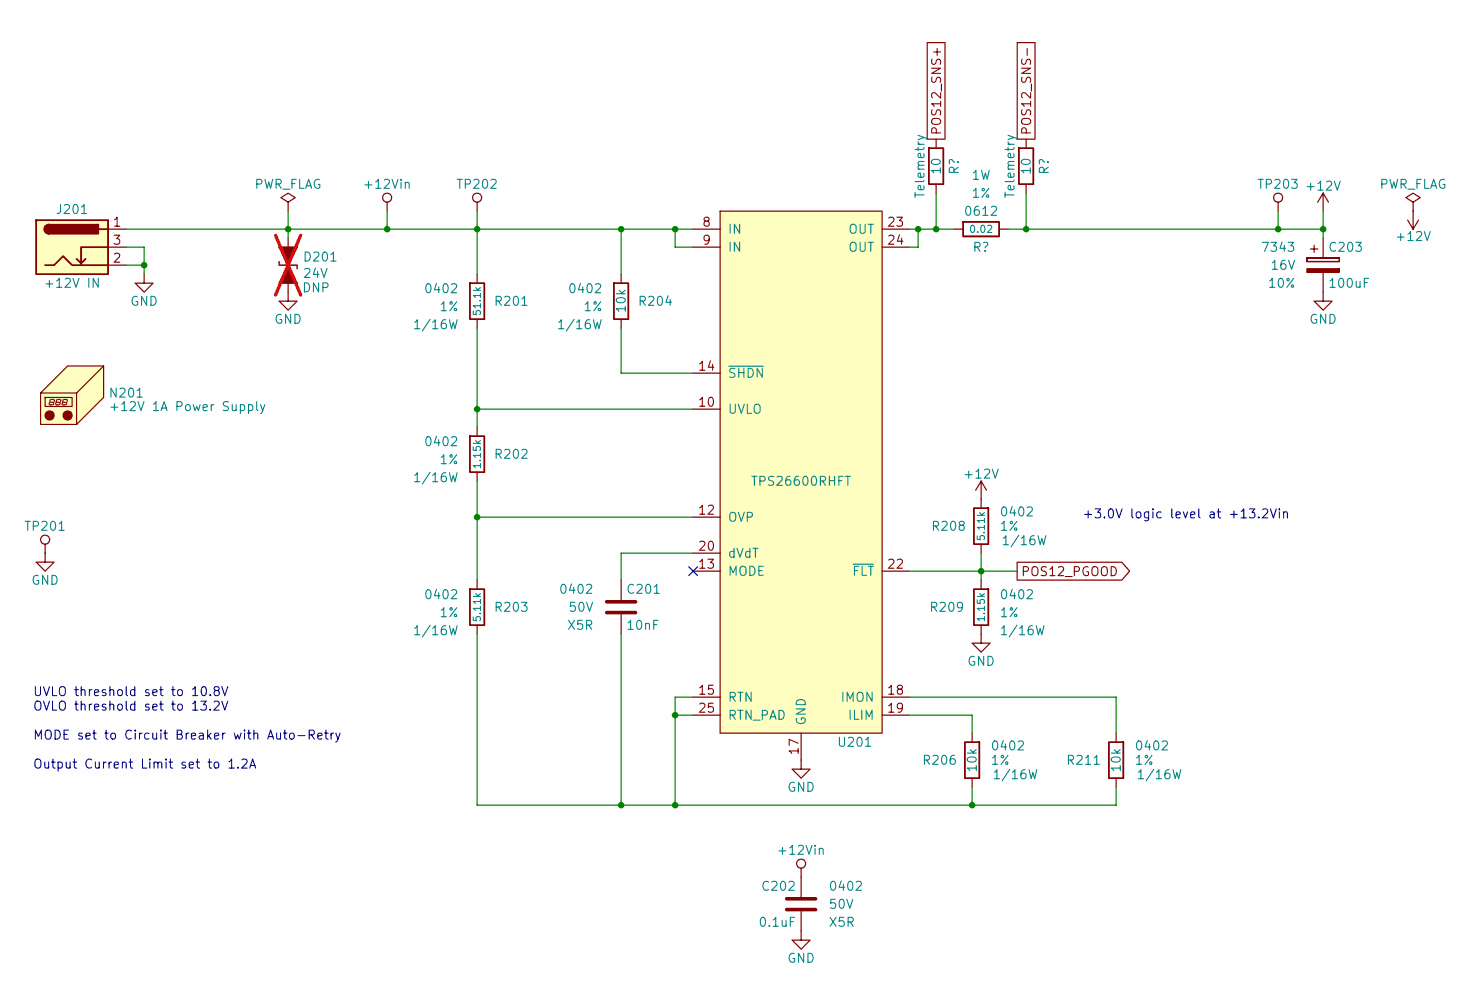
[picture p26: schematic POS12_Input.kicad_sch]

Parts:
C201: 10nF; C_0402; Voltage 50V; Digi-Key PN 445-12201-1-ND
C202: 0.1uF; C_0402; Voltage 50V; Digi-Key PN 490-10697-1-ND
C203: 100uF; CP_EIA-7343-43_Kemet-X; Voltage 16V; Tolerance 10%; Digi-Key PN 718-1102-1-ND
D201: 24V; D_SMA; Digi-Key PN SMAJ24CALFCT-ND; not fitted
J201: +12V IN; BARREL_JACK
N201: +12V 1A Power Supply; Digi-Key PN 993-1335-ND
R201: 51.1k; R_0402; Tolerance 1%; Digi-Key PN RMCF0402FT51K1CT-ND
R202, R209: 1.15k; R_0402; Tolerance 1%; Digi-Key PN RMCF0402FT1K15CT-ND
R203, R208: 5.11k; R_0402; Tolerance 1%; Digi-Key PN RMCF0402FT5K11CT-ND
R204, R206, R211: 10k; R_0402; Tolerance 1%; Digi-Key PN RMCF0402FT10K0CT-ND
R205, R210: 10; R_0402; Tolerance 1%; Digi-Key PN RMCF0402FT10R0CT-ND
R207: 0.02; R_0612; Tolerance 1%; Digi-Key PN P16010CT-ND
TP201: TP; PinHeader_1x01_P2.54mm_Horizontal
TP202, TP203: TP; Test_Point
U201: TPS26600RHFT; QFN-24-1EP_4x5mm_Pitch0.5mm; Digi-Key PN 296-45478-1-ND

Connections:
+12V: C203.1, R207.2, R208.1, R210.2, TP203.1
+12Vin: C202.1, D201.1 (A1), J201.1, R201.1, R204.1, TP202.1, U201.8 (IN), U201.9 (IN)
GND: C202.2, C203.2, D201.2 (A2), J201.2, J201.3, R209.2, TP201.1, U201.17 (GND)
unnamed: C201.1, U201.20 (dVdT)
unnamed: C201.2, R203.2, R206.2, R211.2, U201.15 (RTN), U201.25 (RTN_PAD)
unnamed: R201.2, R202.1, U201.10 (UVLO)
unnamed: R202.2, R203.1, U201.12 (OVP)
unnamed: R204.2, U201.14 (~SHDN)
unnamed: R205.2, R207.1, U201.23 (OUT), U201.24 (OUT)
unnamed: R206.1, U201.19 (ILIM)
unnamed: R211.1, U201.18 (IMON)
POS12_PGOOD: R208.2, R209.1, U201.22 (~FLT)
POS12_SNS+: R205.1
POS12_SNS-: R210.1

Notes on the sheet:
UVLO threshold set to 10.8V OVLO threshold set to 13.2V MODE set to Circuit Breaker with Auto-Retry Output Current Limit set to 1.2A
+3.0V logic level at +13.2Vin
