drewsum/Thermal_Camera/rev_a/hdw/Thermal_Camera/POS12_Telemetry.kicad_sch

## KiCad design rev_a/hdw/Thermal_Camera/POS12_Telemetry.kicad_sch (2024-10-11)

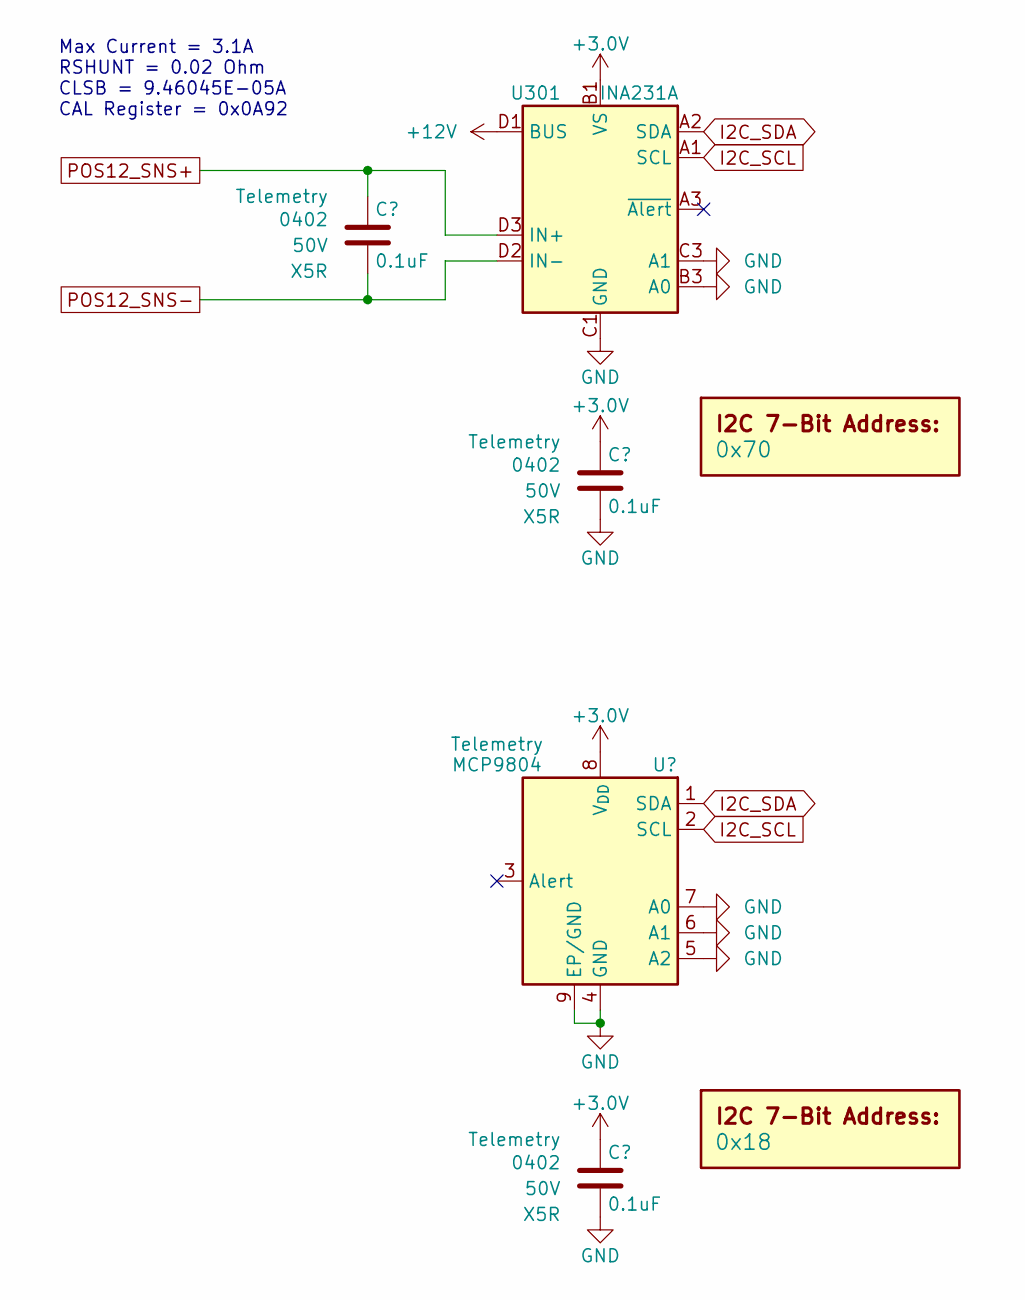
[picture p27: schematic POS12_Telemetry.kicad_sch]

Parts:
C301, C302, C303: 0.1uF; C_0402; Voltage 50V; Digi-Key PN 490-10697-1-ND
DOC301: 0x70
DOC302: 0x18
U301: INA231A; Texas_DSBGA-12_1.65x1.39mm_Layout3x4_P0.4mm; Digi-Key PN 296-41263-1-ND
U302: MCP9804; DFN-8-1EP_3x2mm_P0.5mm_EP1.3x1.5mm; Digi-Key PN MCP9804T-E/MCCT-ND

Connections:
+3.0V: C302.1, C303.1, U301.B1 (VS), U302.8 (V_{DD})
+12V: U301.D1 (BUS)
GND: C302.2, C303.2, U301.B3 (A0), U301.C1 (GND), U301.C3 (A1), U302.4 (GND), U302.5 (A2), U302.6 (A1), U302.7 (A0), U302.9 (EP/GND)
I2C_SCL: U301.A1 (SCL), U302.2 (SCL)
I2C_SDA: U301.A2 (SDA), U302.1 (SDA)
POS12_SNS+: C301.1, U301.D3 (IN+)
POS12_SNS-: C301.2, U301.D2 (IN-)

Notes on the sheet:
Max Current = 3.1A RSHUNT = 0.02 Ohm CLSB = 9.46045E-05A CAL Register = 0x0A92
