drewsum/Thermal_Camera/rev_a/hdw/Thermal_Camera/Status_LEDs.kicad_sch

## KiCad design rev_a/hdw/Thermal_Camera/Status_LEDs.kicad_sch (2024-10-11)

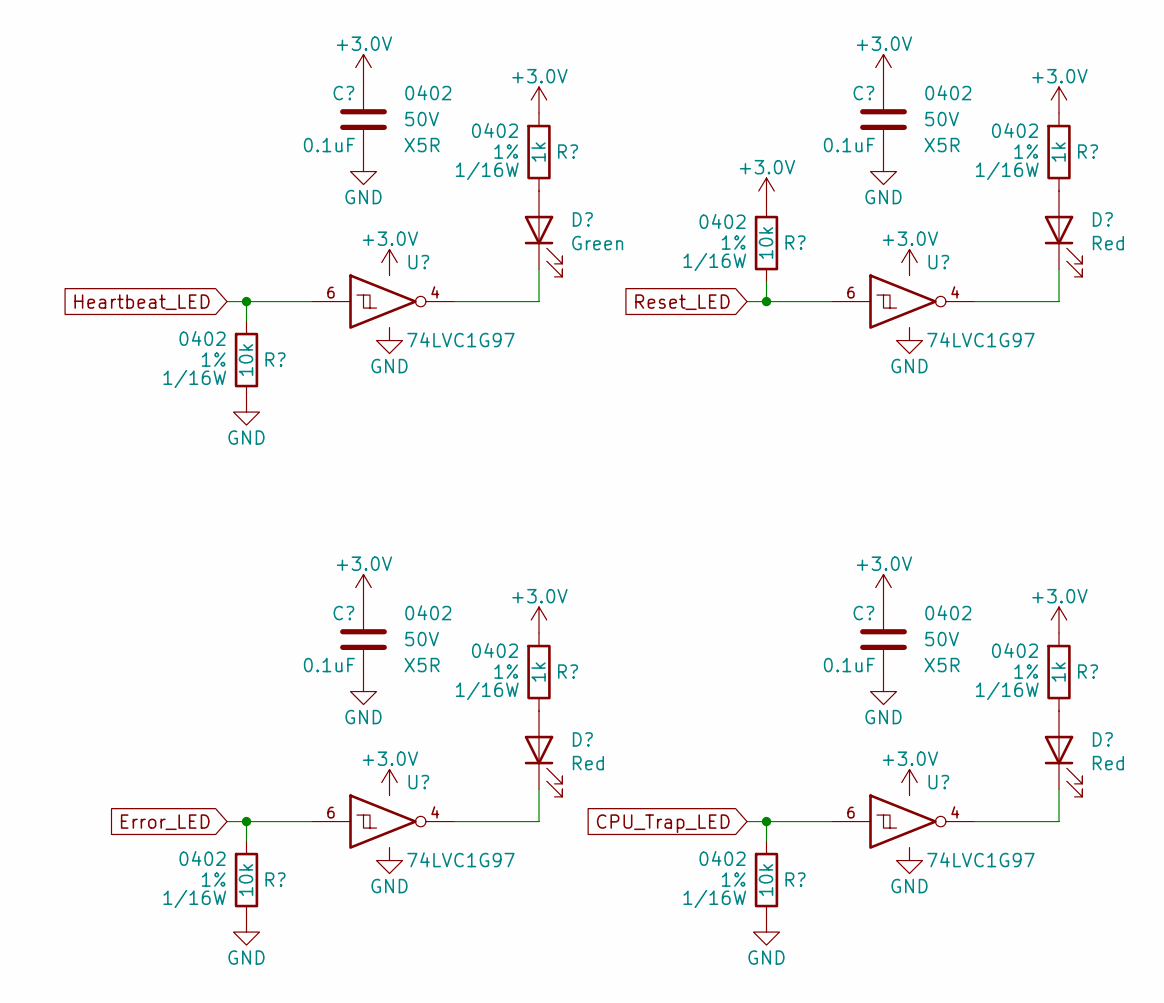
[picture p28: schematic Status_LEDs.kicad_sch]

Parts:
C2801, C2802, C2803, C2804: 0.1uF; C_0402; Voltage 50V; Digi-Key PN 490-10697-1-ND
D2801: Green; LED_0402; Digi-Key PN 1497-1219-1-ND
D2802, D2803, D2804: Red; LED_0402; Digi-Key PN VLMS1500-GS08CT-ND
R2801, R2802, R2805, R2806: 10k; R_0402; Tolerance 1%; Digi-Key PN RMCF0402FT10K0CT-ND
R2803, R2804, R2807, R2808: 1k; R_0402; Tolerance 1%; Digi-Key PN RMCF0402FT1K00CT-ND
U2801, U2802, U2803, U2804: 74LVC1G97; SOT-363_SC-70-6; Digi-Key PN 296-15582-1-ND

Connections:
+3.0V: C2801.1, C2802.1, C2803.1, C2804.1, R2803.1, R2804.1, R2805.1, R2807.1, R2808.1, U2801.1 (VCC), U2801.5 (VCC), U2802.1 (VCC), U2802.5 (VCC), U2803.1 (VCC), U2803.5 (VCC), U2804.1 (VCC), U2804.5 (VCC)
CPU_Trap_LED: R2806.1, U2804.6
Error_LED: R2802.1, U2802.6
GND: C2801.2, C2802.2, C2803.2, C2804.2, R2801.2, R2802.2, R2806.2, U2801.2 (GND), U2801.3 (GND), U2802.2 (GND), U2802.3 (GND), U2803.2 (GND), U2803.3 (GND), U2804.2 (GND), U2804.3 (GND)
Heartbeat_LED: R2801.1, U2801.6
unnamed: D2801.1 (K), U2801.4
unnamed: D2801.2 (A), R2803.2
unnamed: D2802.1 (K), U2802.4
unnamed: D2802.2 (A), R2804.2
unnamed: D2803.1 (K), U2803.4
unnamed: D2803.2 (A), R2807.2
unnamed: D2804.1 (K), U2804.4
unnamed: D2804.2 (A), R2808.2
Reset_LED: R2805.2, U2803.6
