drewsum/Thermal_Camera/rev_a/hdw/Thermal_Camera/USB_Hub.kicad_sch

## KiCad design rev_a/hdw/Thermal_Camera/USB_Hub.kicad_sch (2024-10-11)

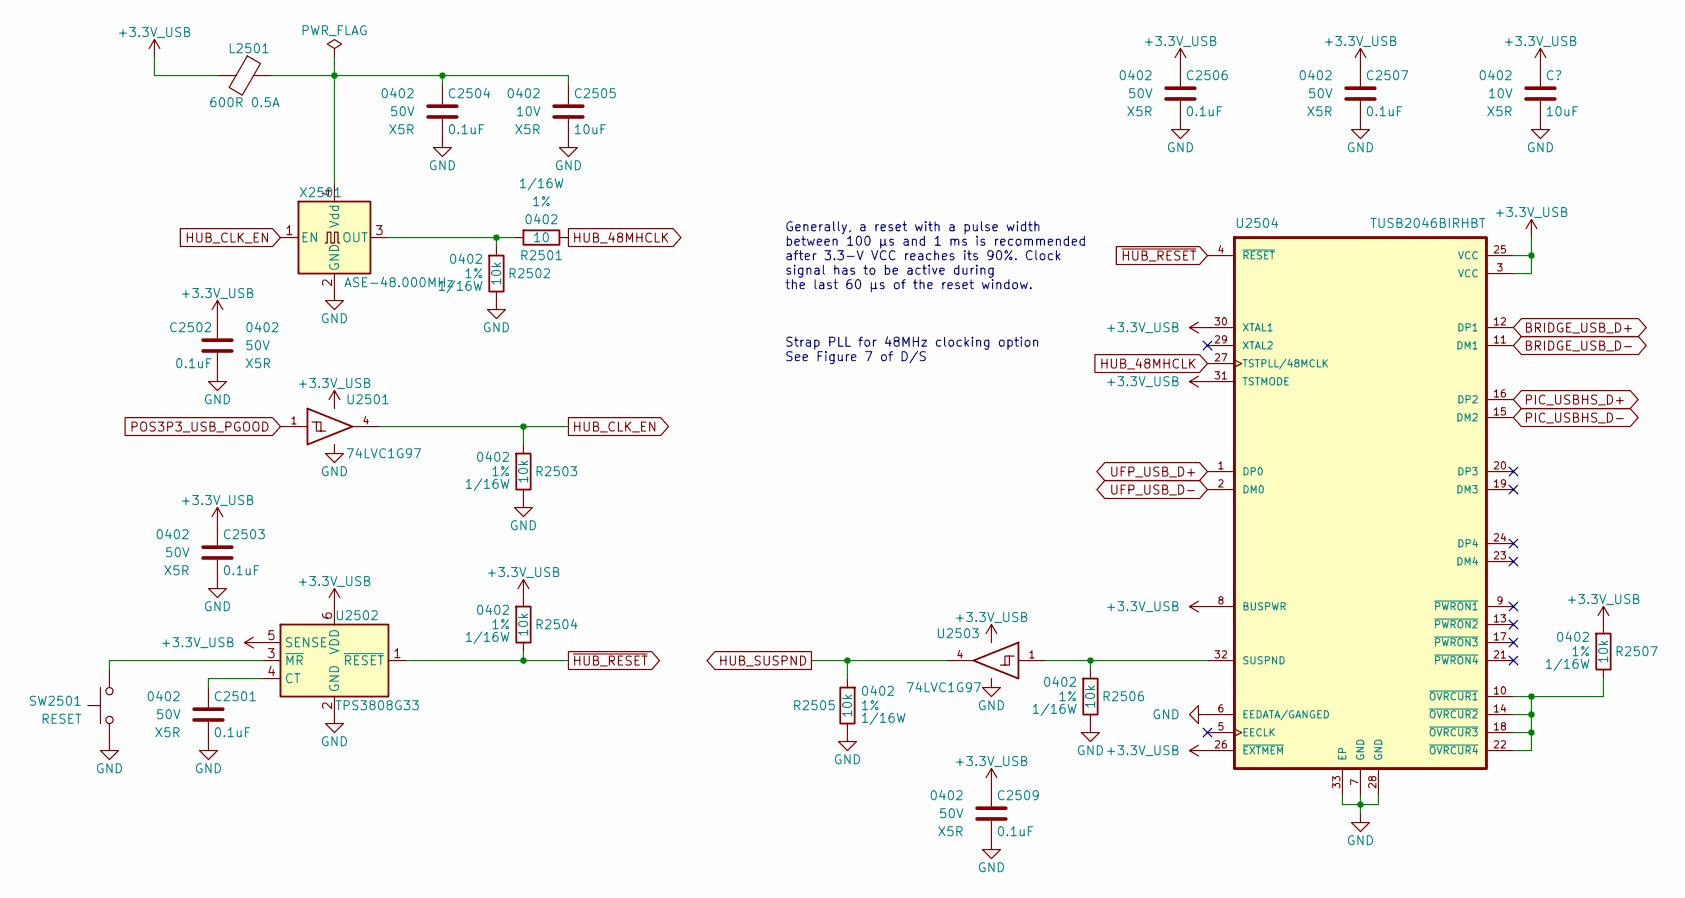
[picture p29: schematic USB_Hub.kicad_sch]

Parts:
C2501, C2502, C2503, C2504, C2506, C2507, C2509: 0.1uF; C_0402; Voltage 50V; Digi-Key PN 490-10697-1-ND
C2505, C2508: 10uF; C_0402; Voltage 10V; Digi-Key PN 490-GRM155R61A106ME11DCT-ND
L2501: 600R 0.5A; L_0402
R2501: 10; R_0402; Tolerance 1%; Digi-Key PN RMCF0402FT10R0CT-ND
R2502, R2503, R2504, R2505, R2506, R2507: 10k; R_0402; Tolerance 1%; Digi-Key PN RMCF0402FT10K0CT-ND
SW2501: RESET; SW_PUSH_6mm
U2501, U2503: 74LVC1G97; SOT-363_SC-70-6; Digi-Key PN 296-15582-1-ND
U2502: TPS3808G33; SOT-23-6; Digi-Key PN 296-17195-1-ND
U2504: TUSB2046BIRHBT; VQFN-32-1EP_5x5mm_P0.5mm_EP3.5x3.5mm; Digi-Key PN 296-27130-1-ND
X2501: ASE-48.000MHz; Oscillator_SMD_Abracon_ASE-4Pin_3.2x2.5mm; Digi-Key PN 535-ASE-48.000MHZ-L-C-TCT-ND

Connections:
+3.3V_USB: C2502.1, C2503.1, C2506.1, C2507.1, C2508.1, C2509.1, L2501.2, R2504.1, R2507.1, U2501.5 (VCC), U2502.5 (SENSE), U2502.6 (VDD), U2503.5 (VCC), U2504.3 (VCC), U2504.8 (BUSPWR), U2504.25 (VCC), U2504.26 (~EXTMEM), U2504.30 (XTAL1), U2504.31 (TSTMODE)
BRIDGE_USB_D+: U2504.12 (DP1)
BRIDGE_USB_D-: U2504.11 (DM1)
GND: C2501.2, C2502.2, C2503.2, C2504.2, C2505.2, C2506.2, C2507.2, C2508.2, C2509.2, R2502.2, R2503.2, R2505.2, R2506.2, SW2501.1, U2501.2 (GND), U2501.3 (GND), U2501.6 (GND), U2502.2 (GND), U2503.2 (GND), U2503.3 (GND), U2503.6 (GND), U2504.6 (EEDATA/GANGED), U2504.7 (GND), U2504.28 (GND), U2504.33 (EP), X2501.2 (GND)
HUB_48MHCLK: R2501.2, U2504.27 (TSTPLL/48MCLK)
HUB_CLK_EN: R2503.1, U2501.4, X2501.1 (EN)
HUB_SUSPND: R2505.1, U2503.4
unnamed: C2501.1, U2502.4 (CT)
unnamed: C2504.1, C2505.1, L2501.1, X2501.4 (Vdd)
unnamed: R2501.1, R2502.1, X2501.3 (OUT)
unnamed: R2506.1, U2503.1, U2504.32 (SUSPND)
unnamed: R2507.2, U2504.10 (~OVRCUR1), U2504.14 (~OVRCUR2), U2504.18 (~OVRCUR3), U2504.22 (~OVRCUR4)
unnamed: SW2501.2, U2502.3 (~MR)
PIC_USBHS_D+: U2504.16 (DP2)
PIC_USBHS_D-: U2504.15 (DM2)
POS3P3_USB_PGOOD: U2501.1
UFP_USB_D+: U2504.1 (DP0)
UFP_USB_D-: U2504.2 (DM0)
~HUB_RESET: R2504.2, U2502.1 (~RESET), U2504.4 (~RESET)

Notes on the sheet:
Generally, a reset with a pulse width between 100 μs and 1 ms is recommended after 3.3-V VCC reaches its 90%. Clock signal has to be active during the last 60 μs of the reset window.
Strap PLL for 48MHz clocking option See Figure 7 of D/S
