drewsum/Thermal_Camera/rev_a/hdw/Thermal_Camera/USB_UART.kicad_sch

## KiCad design rev_a/hdw/Thermal_Camera/USB_UART.kicad_sch (2024-10-11)

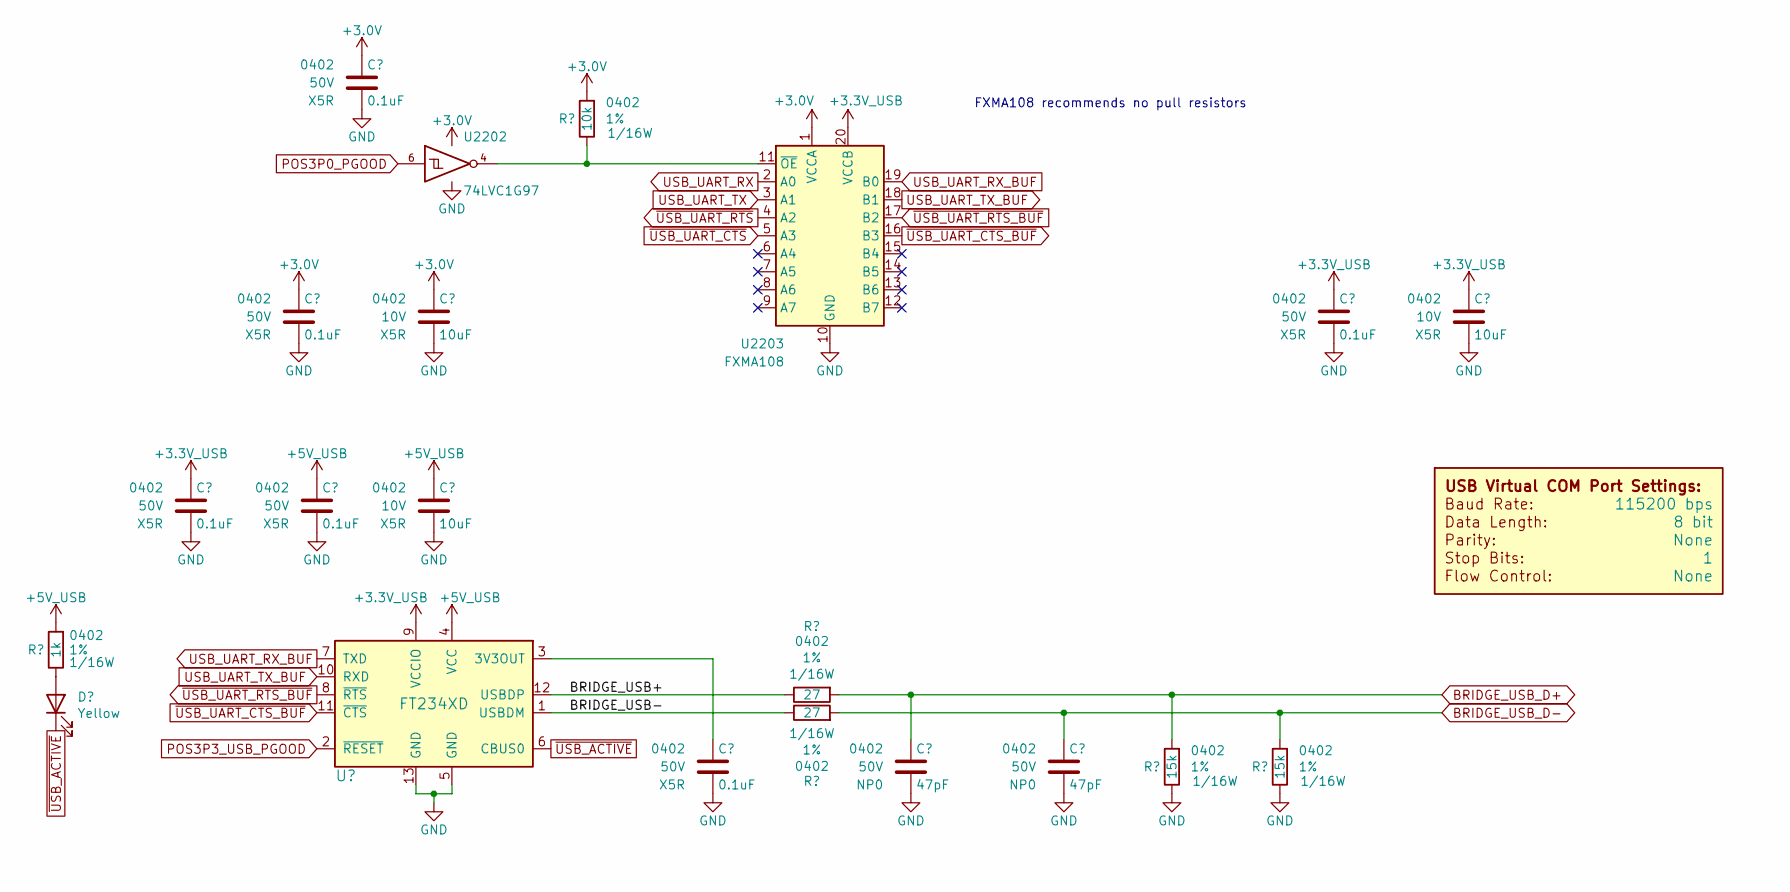
[picture p30: schematic USB_UART.kicad_sch]

Parts:
C2201, C2202, C2203, C2204, C2207, C2210: 0.1uF; C_0402; Voltage 50V; Digi-Key PN 490-10697-1-ND
C2205, C2206, C2211: 10uF; C_0402; Voltage 10V; Digi-Key PN 490-GRM155R61A106ME11DCT-ND
C2208, C2209: 47pF; C_0402; Voltage 50V; Digi-Key PN 490-5942-1-ND
D2201: Yellow; LED_0402; Digi-Key PN VLMY1500-GS08CT-ND
DOC2201: COM_Port_Settings
R2201: 1k; R_0402; Tolerance 1%; Digi-Key PN RMCF0402FT1K00CT-ND
R2202: 10k; R_0402; Tolerance 1%; Digi-Key PN RMCF0402FT10K0CT-ND
R2203, R2204: 27; R_0402; Tolerance 1%; Digi-Key PN RMCF0402FT27R0CT-ND
R2205, R2206: 15k; R_0402; Tolerance 1%; Digi-Key PN RMCF0402FT15K0CT-ND
U2201: FT234XD; DFN-12-1EP_3x3mm_Pitch0.45mm; Digi-Key PN 768-1178-1-ND
U2202: 74LVC1G97; SOT-363_SC-70-6; Digi-Key PN 296-15582-1-ND
U2203: FXMA108; WQFN-20-1EP_2.5x4.5mm_P0.5mm_EP1x2.9mm; Digi-Key PN FXMA108BQX

Connections:
+3.0V: C2202.1, C2204.1, C2205.1, R2202.1, U2202.1 (VCC), U2202.5 (VCC), U2203.1 (VCCA)
+3.3V_USB: C2201.1, C2210.1, C2211.1, U2201.9 (VCCIO), U2203.20 (VCCB)
+5V_USB: C2203.1, C2206.1, R2201.1, U2201.4 (VCC)
BRIDGE_USB+: R2203.2, U2201.12 (USBDP)
BRIDGE_USB-: R2204.2, U2201.1 (USBDM)
BRIDGE_USB_D+: C2208.1, R2203.1, R2205.1
BRIDGE_USB_D-: C2209.1, R2204.1, R2206.1
GND: C2201.2, C2202.2, C2203.2, C2204.2, C2205.2, C2206.2, C2207.2, C2208.2, C2209.2, C2210.2, C2211.2, R2205.2, R2206.2, U2201.5 (GND), U2201.13 (GND), U2202.2 (GND), U2202.3 (GND), U2203.10 (GND)
unnamed: C2207.1, U2201.3 (3V3OUT)
unnamed: D2201.2 (A), R2201.2
unnamed: R2202.2, U2202.4, U2203.11 (~OE)
POS3P0_PGOOD: U2202.6
POS3P3_USB_PGOOD: U2201.2 (~RESET)
USB_UART_RX: U2203.2 (A0)
USB_UART_RX_BUF: U2201.7 (TXD), U2203.19 (B0)
USB_UART_TX: U2203.3 (A1)
USB_UART_TX_BUF: U2201.10 (RXD), U2203.18 (B1)
~USB_ACTIVE: D2201.1 (K), U2201.6 (CBUS0)
~USB_UART_CTS_BUF: U2201.11 (~CTS), U2203.16 (B3)
~USB_UART_CTS: U2203.5 (A3)
~USB_UART_RTS_BUF: U2201.8 (~RTS), U2203.17 (B2)
~USB_UART_RTS: U2203.4 (A2)

Notes on the sheet:
FXMA108 recommends no pull resistors
