drewsum/Thermal_Camera/rev_a/hdw/Thermal_Camera/Upstream_USB_Port.kicad_sch

## KiCad design rev_a/hdw/Thermal_Camera/Upstream_USB_Port.kicad_sch (2024-10-11)

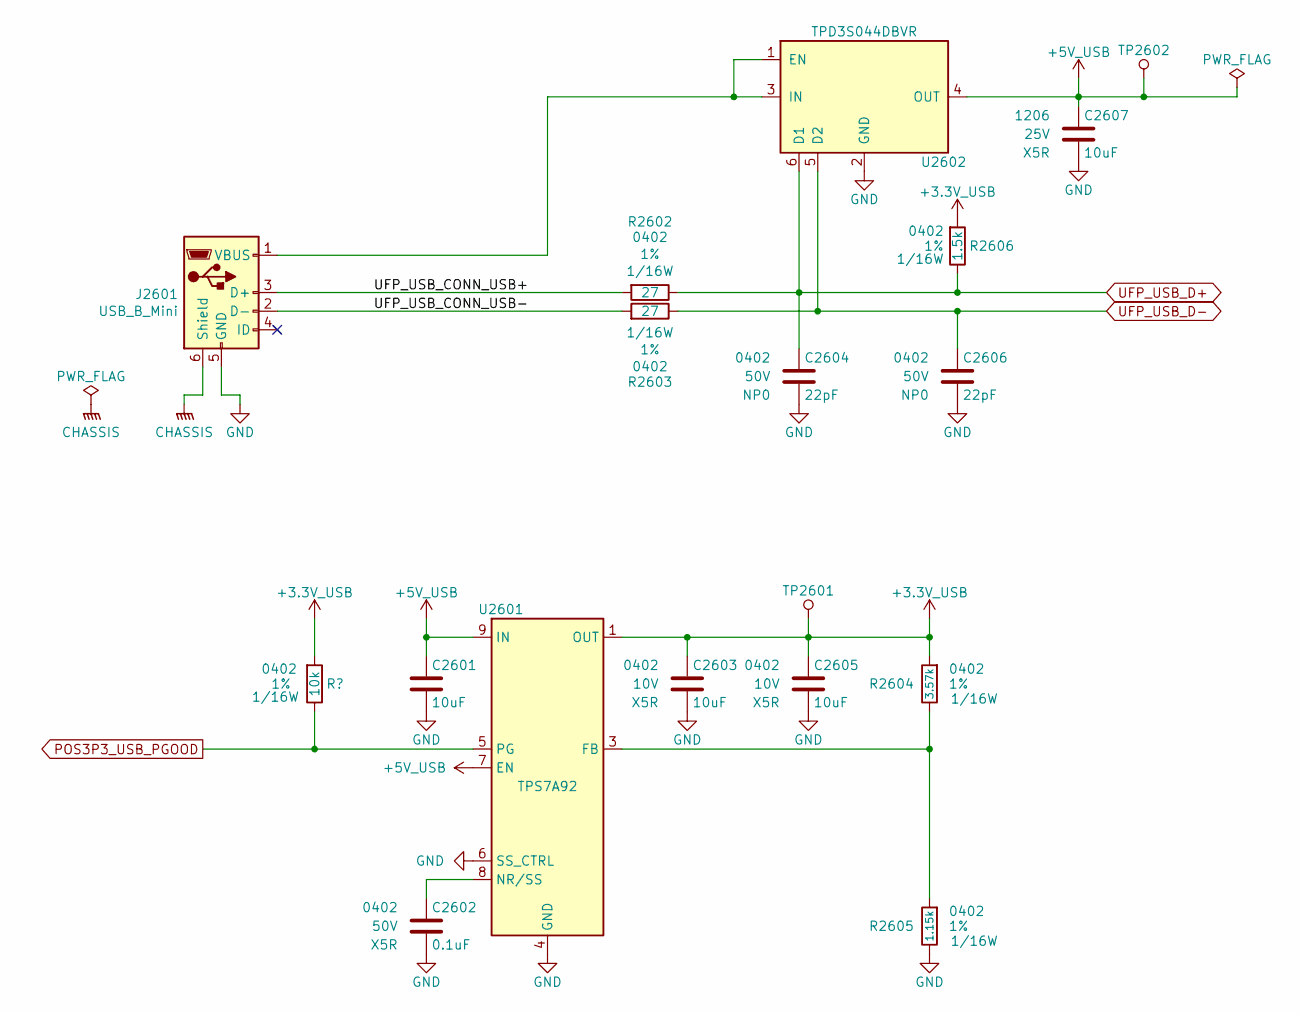
[picture p31: schematic Upstream_USB_Port.kicad_sch]

Parts:
C2601, C2603, C2605: 10uF; C_0402; Voltage 10V; Digi-Key PN 490-GRM155R61A106ME11DCT-ND
C2602: 0.1uF; C_0402; Voltage 50V; Digi-Key PN 490-10697-1-ND
C2604, C2606: 22pF; C_0402; Voltage 50V; Digi-Key PN 490-5868-1-ND
C2607: 10uF; C_1206; Voltage 25V; Digi-Key PN 399-8153-1-ND
J2601: USB_B_Mini; USB_Mini-B; Digi-Key PN 732-2109-1-ND
R2601: 10k; R_0402; Tolerance 1%; Digi-Key PN RMCF0402FT10K0CT-ND
R2602, R2603: 27; R_0402; Tolerance 1%; Digi-Key PN RMCF0402FT27R0CT-ND
R2604: 3.57k; R_0402; Tolerance 1%; Digi-Key PN RMCF0402FT3K57CT-ND
R2605: 1.15k; R_0402; Tolerance 1%; Digi-Key PN RMCF0402FT1K15CT-ND
R2606: 1.5k; R_0402; Tolerance 1%; Digi-Key PN RMCF0402FT1K50CT-ND
TP2601, TP2602: TP; Test_Point
U2601: TPS7A92; Texas_S-PDSO-N10_EP1.2x2mm; Digi-Key PN TPS7A9201DSKR
U2602: TPD3S044DBVR; SOT-23-6; Digi-Key PN 296-38836-1-ND

Connections:
+3.3V_USB: C2603.1, C2605.1, R2601.1, R2604.1, R2606.1, TP2601.1, U2601.1 (OUT), U2601.2 (OUT)
+5V_USB: C2601.1, C2607.1, TP2602.1, U2601.7 (EN), U2601.9 (IN), U2601.10 (IN), U2602.4 (OUT)
CHASSIS: J2601.6 (Shield)
GND: C2601.2, C2602.2, C2603.2, C2604.2, C2605.2, C2606.2, C2607.2, J2601.5 (GND), R2605.2, U2601.4 (GND), U2601.6 (SS_CTRL), U2601.11 (GND), U2602.2 (GND)
unnamed: C2602.1, U2601.8 (NR/SS)
unnamed: J2601.1 (VBUS), U2602.1 (EN), U2602.3 (IN)
unnamed: R2604.2, R2605.1, U2601.3 (FB)
POS3P3_USB_PGOOD: R2601.2, U2601.5 (PG)
UFP_USB_CONN_USB+: J2601.3 (D+), R2602.1
UFP_USB_CONN_USB-: J2601.2 (D-), R2603.1
UFP_USB_D+: C2604.1, R2602.2, R2606.2, U2602.6 (D1)
UFP_USB_D-: C2606.1, R2603.2, U2602.5 (D2)
