drewsum/Thermal_Camera/rev_a/hdw/Thermal_Camera/stitching_caps.kicad_sch

## KiCad design rev_a/hdw/Thermal_Camera/stitching_caps.kicad_sch (2024-10-11)

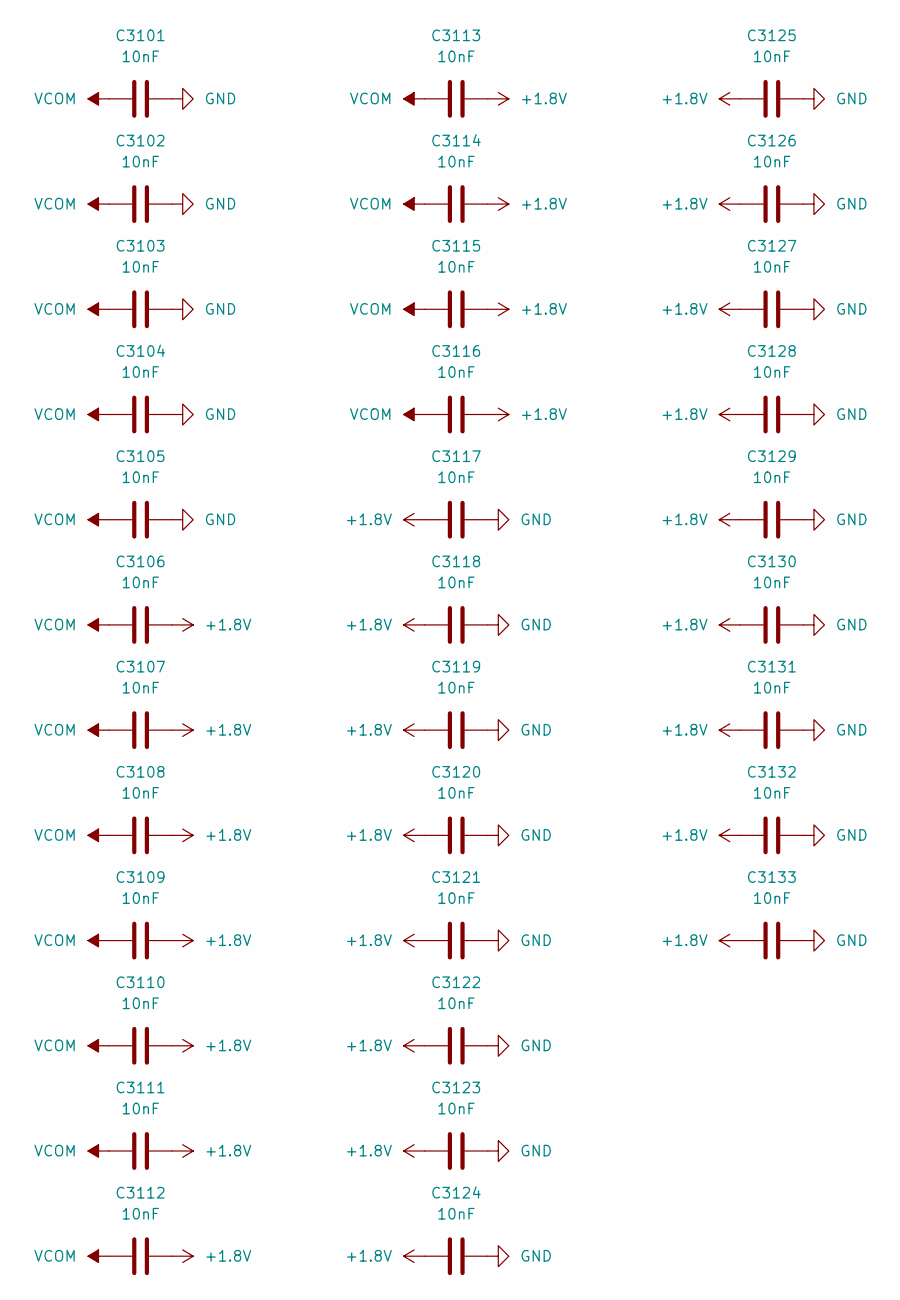
[picture p32: schematic stitching_caps.kicad_sch]

Parts:
C3101, C3102, C3103, C3104, C3105, C3106, C3107, C3108, C3109, C3110, C3111, C3112, C3113, C3114, C3115, C3116, C3117, C3118, C3119, C3120, C3121, C3122, C3123, C3124, C3125, C3126, C3127, C3128, C3129, C3130, C3131, C3132, C3133: 10nF; C_0402; Voltage 50V; Digi-Key PN 445-12201-1-ND

Connections:
+1.8V: C3106.2, C3107.2, C3108.2, C3109.2, C3110.2, C3111.2, C3112.2, C3113.2, C3114.2, C3115.2, C3116.2, C3117.1, C3118.1, C3119.1, C3120.1, C3121.1, C3122.1, C3123.1, C3124.1, C3125.1, C3126.1, C3127.1, C3128.1, C3129.1, C3130.1, C3131.1, C3132.1, C3133.1
GND: C3101.2, C3102.2, C3103.2, C3104.2, C3105.2, C3117.2, C3118.2, C3119.2, C3120.2, C3121.2, C3122.2, C3123.2, C3124.2, C3125.2, C3126.2, C3127.2, C3128.2, C3129.2, C3130.2, C3131.2, C3132.2, C3133.2
VCOM: C3101.1, C3102.1, C3103.1, C3104.1, C3105.1, C3106.1, C3107.1, C3108.1, C3109.1, C3110.1, C3111.1, C3112.1, C3113.1, C3114.1, C3115.1, C3116.1
