drewsum/Thermal_Camera/rev_a/sfw/U1701_firmware/Thermal_Camera/core/32mzda_interrupt_control.c

#include <xc.h>
#include <stdio.h>

#include "core/32mzda_interrupt_control.h"
#include "usb_uart/terminal_control.h"

// This function configures the system for multi-interrupt operation and
// assigns shadow registers sets to priority level ISRs
bool interruptControllerInitialize(void) {
 
    // Enable multi-vector interrupt mode
    INTCONbits.MVEC = 1;
    
    // Assign shadow register sets to interrupt priorities
    // assign shadow set #7-#1 to priority level #7-#1 ISRs
    PRISS = 0x76543210;

    // Report success if multi-vector interrupt mode is enabled
    return (INTCONbits.MVEC == 1);

}

// This function enables global interrupts
void enableGlobalInterrupts(void) {
 
    // This is built into the XC32 compiler
    __builtin_enable_interrupts();
    
}

// This function disables global interrupts
void disableGlobalInterrupts(void) {
 
    // This is built into the XC32 compiler
    __builtin_disable_interrupts();
    
}

// This function returns the state of global interrupt enable
// Returns 0 if global interrupts are disabled
// returns 1 if global interrupts are enabled
uint8_t getGlobalInterruptsState(void) {
 
    return __builtin_get_isr_state();
    
}

// This function explicitly sets the state of global interrupts
void setGlobalInterruptsState(uint8_t input_state) {

    __builtin_set_isr_state(input_state);
    
}


// This function allows for the setting/clearing of a given interrupt
// It manipulates that interrupt's 'Interrupt Enable' bit
void setInterruptEnable(interrupt_source_t input_interrupt, uint8_t input_state) {

    // Decide which interrupt control bits to manipulate based on which interrupt
    // is being enabled or disabled
    switch (input_interrupt) {
            
        case core_timer_interrupt:
            IEC0bits.CTIE = input_state;
            break;

        case core_software_interrupt_0:
            IEC0bits.CS0IE = input_state;
            break;

        case core_software_interrupt_1:
            IEC0bits.CS1IE = input_state;
            break;

        case external_interrupt_0:
            IEC0bits.INT0IE = input_state;
            break;

        case timer1:
            IEC0bits.T1IE = input_state;
            break;

        case input_capture_1_error:
            IEC0bits.IC1EIE = input_state;
            break;

        case input_capture_1:
            IEC0bits.IC1IE = input_state;
            break;

        case output_compare_1:
            IEC0bits.OC1IE = input_state;
            break;

        case external_interrupt_1:
            IEC0bits.INT1IE = input_state;
            break;

        case timer2:
            IEC0bits.T2IE = input_state;
            break;

        case input_capture_2_error:
            IEC0bits.IC2EIE = input_state;
            break;

        case input_capture_2:
            IEC0bits.IC2IE = input_state;
            break;

        case output_compare_2:
            IEC0bits.OC2IE = input_state;
            break;

        case external_interrupt_2:
            IEC0bits.INT2IE = input_state;
            break;

        case timer3:
            IEC0bits.T3IE = input_state;
            break;

        case input_capture_3_error:
            IEC0bits.IC3EIE = input_state;
            break;

        case input_capture_3:
            IEC0bits.IC3IE = input_state;
            break;

        case output_compare_3:
            IEC0bits.OC3IE = input_state;
            break;

        case external_interrupt_3:
            IEC0bits.INT3IE = input_state;
            break;

        case timer4:
            IEC0bits.T4IE = input_state;
            break;

        case input_capture_4_error:
            IEC0bits.IC4EIE = input_state;
            break;

        case input_capture_4:
            IEC0bits.IC4IE = input_state;
            break;

        case output_compare_4:
            IEC0bits.OC4IE = input_state;
            break;

        case external_interrupt_4:
            IEC0bits.INT4IE = input_state;
            break;

        case timer5:
            IEC0bits.T5IE = input_state;
            break;

        case input_capture_5_error:
            IEC0bits.IC5EIE = input_state;
            break;

        case input_capture_5:
            IEC0bits.IC5IE = input_state;
            break;

        case output_compare_5:
            IEC0bits.OC5IE = input_state;
            break;

        case timer6:
            IEC0bits.T6IE = input_state;
            break;

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
            IEC3bits.CFDCIE = input_state;
            break;

        case system_bus_protection_violation:
            IEC3bits.SBIE = input_state;
            break;

        case spi1_fault:
            IEC3bits.SPI1EIE = input_state;
            break;

        case spi1_receive_done:
            IEC3bits.SPI1RXIE = input_state;
            break;

        case spi1_transfer_done:
            IEC3bits.SPI1TXIE = input_state;
            break;

        case uart1_fault:
            IEC3bits.U1EIE = input_state;
            break;

        case uart1_receive_done:
            IEC3bits.U1RXIE = input_state;
            break;

        case uart1_transfer_done:
            IEC3bits.U1TXIE = input_state;
            break;

        case i2c1_bus_collision_event:
            IEC3bits.I2C1BIE = input_state;
            break;

        case i2c1_client_event:
            IEC3bits.I2C1SIE = input_state;
            break;

        case i2c1_host_event:
            IEC3bits.I2C1MIE = input_state;
            break;

        case porta_input_change_interrupt:
            IEC3bits.CNAIE = input_state;
            break;

        case portb_input_change_interrupt:
            IEC3bits.CNBIE = input_state;
            break;

        case portc_input_change_interrupt:
            IEC3bits.CNCIE = input_state;
            break;

        case portd_input_change_interrupt:
            IEC3bits.CNDIE = input_state;
            break;

        case porte_input_change_interrupt:
            IEC3bits.CNEIE = input_state;
            break;

        case portf_input_change_interrupt:
            IEC3bits.CNFIE = input_state;
            break;

        case portg_input_change_interrupt:
            IEC3bits.CNGIE = input_state;
            break;

        case porth_input_change_interrupt:
            IEC3bits.CNHIE = input_state;
            break;

        case portj_input_change_interrupt:
            IEC3bits.CNJIE = input_state;
            break;

        case portk_input_change_interrupt:
            IEC3bits.CNKIE = input_state;
            break;

        case pmp:
            IEC4bits.PMPIE = input_state;
            break;

        case pmp_error:
            IEC4bits.PMPEIE = input_state;
            break;

        case comparator_1_interrupt:
            IEC4bits.CMP1IE = input_state;
            break;

        case comparator_2_interrupt:
            IEC4bits.CMP2IE = input_state;
            break;

        case usb_general_event:
            IEC4bits.USBIE = input_state;
            break;

        case usb_dma_event:
            IEC4bits.USBDMAIE = input_state;
            break;

        case dma_channel_0:
            IEC4bits.DMA0IE = input_state;
            break;

        case dma_channel_1:
            IEC4bits.DMA1IE = input_state;
            break;

        case dma_channel_2:
            IEC4bits.DMA2IE = input_state;
            break;

        case dma_channel_3:
            IEC4bits.DMA3IE = input_state;
            break;

        case dma_channel_4:
            IEC4bits.DMA4IE = input_state;
            break;

        case dma_channel_5:
            IEC4bits.DMA5IE = input_state;
            break;

        case dma_channel_6:
            IEC4bits.DMA6IE = input_state;
            break;

        case dma_channel_7:
            IEC4bits.DMA7IE = input_state;
            break;

        case spi2_fault:
            IEC4bits.SPI2EIE = input_state;
            break;

        case spi2_receive_done:
            IEC4bits.SPI2RXIE = input_state;
            break;

        case spi2_transfer_done:
            IEC4bits.SPI2TXIE = input_state;
            break;

        case uart2_fault:
            IEC4bits.U2EIE = input_state;
            break;

        case uart2_receive_done:
            IEC4bits.U2RXIE = input_state;
            break;

        case uart2_transfer_done:
            IEC4bits.U2TXIE = input_state;
            break;

        case i2c2_bus_collision_event:
            IEC4bits.I2C2BIE = input_state;
            break;

        case i2c2_client_event:
            IEC4bits.I2C2SIE = input_state;
            break;

        case i2c2_host_event:
            IEC4bits.I2C2MIE = input_state;
            break;

        case control_area_network_1:
            IEC4bits.CAN1IE = input_state;
            break;

        case control_area_network_2:
            IEC4bits.CAN2IE = input_state;
            break;

        case ethernet_interrupt:
            IEC4bits.ETHIE = input_state;
            break;

        case spi3_fault:
            IEC4bits.SPI3EIE = input_state;
            break;

        case spi3_receive_done:
            IEC4bits.SPI3RXIE = input_state;
            break;

        case spi3_transfer_done:
            IEC4bits.SPI3TXIE = input_state;
            break;

        case uart3_fault:
            IEC4bits.U3EIE = input_state;
            break;

        case uart3_receive_done:
            IEC4bits.U3RXIE = input_state;
            break;

        case uart3_transfer_done:
            IEC4bits.U3TXIE = input_state;
            break;

        case i2c3_bus_collision_event:
            IEC5bits.I2C3BIE = input_state;
            break;

        case i2c3_client_event:
            IEC5bits.I2C3SIE = input_state;
            break;

        case i2c3_host_event:
            IEC5bits.I2C3MIE = input_state;
            break;

        case spi4_fault:
            IEC5bits.SPI4EIE = input_state;
            break;

        case spi4_receive_done:
            IEC5bits.SPI4RXIE = input_state;
            break;

        case spi4_transfer_done:
            IEC5bits.SPI4TXIE = input_state;
            break;

        case real_time_clock:
            IEC5bits.RTCCIE = input_state;
            break;

        case flash_control_event:
            IEC5bits.FCEIE = input_state;
            break;

        case prefetch_module_sec_event:
            IEC5bits.PREIE = input_state;
            break;

        case sqi1_event:
            IEC5bits.SQI1IE = input_state;
            break;

        case uart4_fault:
            IEC5bits.U4EIE = input_state;
            break;

        case uart4_receive_done:
            IEC5bits.U4RXIE = input_state;
            break;

        case uart4_transfer_done:
            IEC5bits.U4TXIE = input_state;
            break;

        case i2c4_bus_collision_event:
            IEC5bits.I2C4BIE = input_state;
            break;

        case i2c4_client_event:
            IEC5bits.I2C4SIE = input_state;
            break;

        case i2c4_host_event:
            IEC5bits.I2C4MIE = input_state;
            break;

        case spi5_fault:
            IEC5bits.SPI5EIE = input_state;
            break;

        case spi5_receive_done:
            IEC5bits.SPI5RXIE = input_state;
            break;

        case spi5_transfer_done:
            IEC5bits.SPI5TXIE = input_state;
            break;

        case uart5_fault:
            IEC5bits.U5EIE = input_state;
            break;

        case uart5_receive_done:
            IEC5bits.U5RXIE = input_state;
            break;

        case uart5_transfer_done:
            IEC5bits.U5TXIE = input_state;
            break;

        case i2c5_bus_collision_event:
            IEC5bits.I2C5BIE = input_state;
            break;

        case i2c5_client_event:
            IEC5bits.I2C5SIE = input_state;
            break;

        case i2c5_host_event:
            IEC5bits.I2C5MIE = input_state;
            break;

        case spi6_fault:
            IEC5bits.SPI6IE = input_state;
            break;

        case spi6_receive_done:
            IEC5bits.SPI6RXIE = input_state;
            break;

        case spi6_transfer_done:
            IEC5bits.SPI6TXIE = input_state;
            break;

        case uart6_fault:
            IEC5bits.U6EIE = input_state;
            break;

        case uart6_receive_done:
            IEC5bits.U6RXIE = input_state;
            break;

        case uart6_transfer_done:
            IEC5bits.U6TXIE = input_state;
            break;

        case sdhc_interrupt:
            IEC5bits.SDHCIE = input_state;
            break;

        case glcd_interrupt:
            IEC6bits.GLCDIE = input_state;
            break;

        case gpu_interrupt:
            IEC6bits.GPUIE = input_state;
            break;

        case ctmu_interrupt:
            IEC6bits.CTMUIE = input_state;
            break;

        case adc_end_of_scan:
            IEC6bits.ADCEOSIE = input_state;
            break;

        case adc_analog_circuit_ready:
            IEC6bits.ADCARDYIE = input_state;
            break;

        case adc_update_ready:
            IEC6bits.ADCURDYIE = input_state;
            break;

        case adc0_early_interrupt:
            IEC6bits.ADC0EIE = input_state;
            break;

        case adc1_early_interrupt:
            IEC6bits.ADC1EIE = input_state;
            break;

        case adc2_early_interrupt:
            IEC6bits.ADC2EIE = input_state;
            break;

        case adc3_early_interrupt:
            IEC6bits.ADC3EIE = input_state;
            break;

        case adc4_early_interrupt:
            IEC6bits.ADC4EIE = input_state;
            break;

        case adc_group_early_interrupt_request:
            IEC6bits.ADCGRPIE = input_state;
            break;

        case adc7_early_interrupt:
            IEC6bits.ADC7EIE = input_state;
            break;

        case adc0_warm_interrupt:
            IEC6bits.ADC0WIE = input_state;
            break;

        case adc1_warm_interrupt:
            IEC6bits.ADC1WIE = input_state;
            break;

        case adc2_warm_interrupt:
            IEC6bits.ADC2WIE = input_state;
            break;

        case adc3_warm_interrupt:
            IEC6bits.ADC3WIE = input_state;
            break;

        case adc4_warm_interrupt:
            IEC6bits.ADC4WIE = input_state;
            break;

        case adc7_warm_interrupt:
            IEC6bits.ADC7WIE = input_state;
            break;

        case mpll_fault_interrupt:
            IEC6bits.MPLLFLTIE = input_state;
            break;
            
        default:
            break;
            
    }

}

// This function allows for the reading of a given interrupt enable
// It reads the interrupt's 'Interrupt Enable' bit with IEC registers
// Returns the state of the given interrupt
uint8_t getInterruptEnable(interrupt_source_t input_interrupt) {

    // Decide which interrupt control bits to manipulate based on which interrupt
    // is being enabled or disabled
    switch (input_interrupt) {

        case core_timer_interrupt:
            return IEC0bits.CTIE;
            break;

        case core_software_interrupt_0:
            return IEC0bits.CS0IE;
            break;

        case core_software_interrupt_1:
            return IEC0bits.CS1IE;
            break;

        case external_interrupt_0:
            return IEC0bits.INT0IE;
            break;

        case timer1:
            return IEC0bits.T1IE;
            break;

        case input_capture_1_error:
            return IEC0bits.IC1EIE;
            break;

        case input_capture_1:
            return IEC0bits.IC1IE;
            break;

        case output_compare_1:
            return IEC0bits.OC1IE;
            break;

        case external_interrupt_1:
            return IEC0bits.INT1IE;
            break;

        case timer2:
            return IEC0bits.T2IE;
            break;

        case input_capture_2_error:
            return IEC0bits.IC2EIE;
            break;

        case input_capture_2:
            return IEC0bits.IC2IE;
            break;

        case output_compare_2:
            return IEC0bits.OC2IE;
            break;

        case external_interrupt_2:
            return IEC0bits.INT2IE;
            break;

        case timer3:
            return IEC0bits.T3IE;
            break;

        case input_capture_3_error:
            return IEC0bits.IC3EIE;
            break;

        case input_capture_3:
            return IEC0bits.IC3IE;
            break;

        case output_compare_3:
            return IEC0bits.OC3IE;
            break;

        case external_interrupt_3:
            return IEC0bits.INT3IE;
            break;

        case timer4:
            return IEC0bits.T4IE;
            break;

        case input_capture_4_error:
            return IEC0bits.IC4EIE;
            break;

        case input_capture_4:
            return IEC0bits.IC4IE;
            break;

        case output_compare_4:
            return IEC0bits.OC4IE;
            break;

        case external_interrupt_4:
            return IEC0bits.INT4IE;
            break;

        case timer5:
            return IEC0bits.T5IE;
            break;

        case input_capture_5_error:
            return IEC0bits.IC5EIE;
            break;

        case input_capture_5:
            return IEC0bits.IC5IE;
            break;

        case output_compare_5:
            return IEC0bits.OC5IE;
            break;

        case timer6:
            return IEC0bits.T6IE;
            break;

        case input_capture_6_error:
            return IEC0bits.IC6EIE;
            break;

        case input_capture_6:
            return IEC0bits.IC6IE;
            break;

        case output_compare_6:
            return IEC0bits.OC6IE;
            break;

        case timer7:
            return IEC1bits.T7IE;
            break;

        case input_capture_7_error:
            return IEC1bits.IC7EIE;
            break;

        case input_capture_7:
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
            break;

        case adc_data_24:
            return IEC2bits.ADCD24IE;
            break;

        case adc_data_25:
            return IEC2bits.ADCD25IE;
            break;

        case adc_data_26:
            return IEC2bits.ADCD26IE;
            break;

        case adc_data_27:
            return IEC2bits.ADCD27IE;
            break;

        case adc_data_28:
            return IEC2bits.ADCD28IE;
            break;

        case adc_data_29:
            return IEC2bits.ADCD29IE;
            break;

        case adc_data_30:
            return IEC2bits.ADCD30IE;
            break;

        case adc_data_31:
            return IEC2bits.ADCD31IE;
            break;

        case adc_data_32:
            return IEC2bits.ADCD32IE;
            break;

        case adc_data_33:
            return IEC2bits.ADCD33IE;
            break;

        case adc_data_34:
            return IEC2bits.ADCD34IE;
            break;

        case adc_data_35:
            return IEC2bits.ADCD35IE;
            break;

        case adc_data_36:
            return IEC2bits.ADCD36IE;
            break;

        case adc_data_37:
            return IEC3bits.ADCD37IE;
            break;

        case adc_data_38:
            return IEC3bits.ADCD38IE;
            break;

        case adc_data_39:
            return IEC3bits.ADCD39IE;
            break;

        case adc_data_40:
            return IEC3bits.ADCD40IE;
            break;

        case adc_data_41:
            return IEC3bits.ADCD41IE;
            break;

        case adc_data_42:
            return IEC3bits.ADCD42IE;
            break;

        case adc_data_43:
            return IEC3bits.ADCD43IE;
            break;

        case usb_suspend_resume_event:
            return IEC3bits.USBSRIE;
            break;

        case core_performance_counter_interrupt:
            return IEC3bits.CPCIE;
            break;

        case core_fast_debug_channel_interrupt:
            return IEC3bits.CFDCIE;
            break;

        case system_bus_protection_violation:
            return IEC3bits.SBIE;
            break;

        case spi1_fault:
            return IEC3bits.SPI1EIE;
            break;

        case spi1_receive_done:
            return IEC3bits.SPI1RXIE;
            break;

        case spi1_transfer_done:
            return IEC3bits.SPI1TXIE;
            break;

        case uart1_fault:
            return IEC3bits.U1EIE;
            break;

        case uart1_receive_done:
            return IEC3bits.U1RXIE;
            break;

        case uart1_transfer_done:
            return IEC3bits.U1TXIE;
            break;

        case i2c1_bus_collision_event:
            return IEC3bits.I2C1BIE;
            break;

        case i2c1_client_event:
            return IEC3bits.I2C1SIE;
            break;

        case i2c1_host_event:
            return IEC3bits.I2C1MIE;
            break;

        case porta_input_change_interrupt:
            return IEC3bits.CNAIE;
            break;

        case portb_input_change_interrupt:
            return IEC3bits.CNBIE;
            break;

        case portc_input_change_interrupt:
            return IEC3bits.CNCIE;
            break;

        case portd_input_change_interrupt:
            return IEC3bits.CNDIE;
            break;

        case porte_input_change_interrupt:
            return IEC3bits.CNEIE;
            break;

        case portf_input_change_interrupt:
            return IEC3bits.CNFIE;
            break;

        case portg_input_change_interrupt:
            return IEC3bits.CNGIE;
            break;

        case porth_input_change_interrupt:
            return IEC3bits.CNHIE;
            break;

        case portj_input_change_interrupt:
            return IEC3bits.CNJIE;
            break;

        case portk_input_change_interrupt:
            return IEC3bits.CNKIE;
            break;

        case pmp:
            return IEC4bits.PMPIE;
            break;

        case pmp_error:
            return IEC4bits.PMPEIE;
            break;

        case comparator_1_interrupt:
            return IEC4bits.CMP1IE;
            break;

        case comparator_2_interrupt:
            return IEC4bits.CMP2IE;
            break;

        case usb_general_event:
            return IEC4bits.USBIE;
            break;

        case usb_dma_event:
            return IEC4bits.USBDMAIE;
            break;

        case dma_channel_0:
            return IEC4bits.DMA0IE;
            break;

        case dma_channel_1:
            return IEC4bits.DMA1IE;
            break;

        case dma_channel_2:
            return IEC4bits.DMA2IE;
            break;

        case dma_channel_3:
            return IEC4bits.DMA3IE;
            break;

        case dma_channel_4:
            return IEC4bits.DMA4IE;
            break;

        case dma_channel_5:
            return IEC4bits.DMA5IE;
            break;

        case dma_channel_6:
            return IEC4bits.DMA6IE;
            break;

        case dma_channel_7:
            return IEC4bits.DMA7IE;
            break;

        case spi2_fault:
            return IEC4bits.SPI2EIE;
            break;

        case spi2_receive_done:
            return IEC4bits.SPI2RXIE;
            break;

        case spi2_transfer_done:
            return IEC4bits.SPI2TXIE;
            break;

        case uart2_fault:
            return IEC4bits.U2EIE;
            break;

        case uart2_receive_done:
            return IEC4bits.U2RXIE;
            break;

        case uart2_transfer_done:
            return IEC4bits.U2TXIE;
            break;

        case i2c2_bus_collision_event:
            return IEC4bits.I2C2BIE;
            break;

        case i2c2_client_event:
            return IEC4bits.I2C2SIE;
            break;

        case i2c2_host_event:
            return IEC4bits.I2C2MIE;
            break;

        case control_area_network_1:
            return IEC4bits.CAN1IE;
            break;

        case control_area_network_2:
            return IEC4bits.CAN2IE;
            break;

        case ethernet_interrupt:
            return IEC4bits.ETHIE;
            break;

        case spi3_fault:
            return IEC4bits.SPI3EIE;
            break;

        case spi3_receive_done:
            return IEC4bits.SPI3RXIE;
            break;

        case spi3_transfer_done:
            return IEC4bits.SPI3TXIE;
            break;

        case uart3_fault:
            return IEC4bits.U3EIE;
            break;

        case uart3_receive_done:
            return IEC4bits.U3RXIE;
            break;

        case uart3_transfer_done:
            return IEC4bits.U3TXIE;
            break;

        case i2c3_bus_collision_event:
            return IEC5bits.I2C3BIE;
            break;

        case i2c3_client_event:
            return IEC5bits.I2C3SIE;
            break;

        case i2c3_host_event:
            return IEC5bits.I2C3MIE;
            break;

        case spi4_fault:
            return IEC5bits.SPI4EIE;
            break;

        case spi4_receive_done:
            return IEC5bits.SPI4RXIE;
            break;

        case spi4_transfer_done:
            return IEC5bits.SPI4TXIE;
            break;

        case real_time_clock:
            return IEC5bits.RTCCIE;
            break;

        case flash_control_event:
            return IEC5bits.FCEIE;
            break;

        case prefetch_module_sec_event:
            return IEC5bits.PREIE;
            break;

        case sqi1_event:
            return IEC5bits.SQI1IE;
            break;

        case uart4_fault:
            return IEC5bits.U4EIE;
            break;

        case uart4_receive_done:
            return IEC5bits.U4RXIE;
            break;

        case uart4_transfer_done:
            return IEC5bits.U4TXIE;
            break;

        case i2c4_bus_collision_event:
            return IEC5bits.I2C4BIE;
            break;

        case i2c4_client_event:
            return IEC5bits.I2C4SIE;
            break;

        case i2c4_host_event:
            return IEC5bits.I2C4MIE;
            break;

        case spi5_fault:
            return IEC5bits.SPI5EIE;
            break;

        case spi5_receive_done:
            return IEC5bits.SPI5RXIE;
            break;

        case spi5_transfer_done:
            return IEC5bits.SPI5TXIE;
            break;

        case uart5_fault:
            return IEC5bits.U5EIE;
            break;

        case uart5_receive_done:
            return IEC5bits.U5RXIE;
            break;

        case uart5_transfer_done:
            return IEC5bits.U5TXIE;
            break;

        case i2c5_bus_collision_event:
            return IEC5bits.I2C5BIE;
            break;

        case i2c5_client_event:
            return IEC5bits.I2C5SIE;
            break;

        case i2c5_host_event:
            return IEC5bits.I2C5MIE;
            break;

        case spi6_fault:
            return IEC5bits.SPI6IE;
            break;

        case spi6_receive_done:
            return IEC5bits.SPI6RXIE;
            break;

        case spi6_transfer_done:
            return IEC5bits.SPI6TXIE;
            break;

        case uart6_fault:
            return IEC5bits.U6EIE;
            break;

        case uart6_receive_done:
            return IEC5bits.U6RXIE;
            break;

        case uart6_transfer_done:
            return IEC5bits.U6TXIE;
            break;

        case sdhc_interrupt:
            return IEC5bits.SDHCIE;
            break;

        case glcd_interrupt:
            return IEC6bits.GLCDIE;
            break;

        case gpu_interrupt:
            return IEC6bits.GPUIE;
            break;

        case ctmu_interrupt:
            return IEC6bits.CTMUIE;
            break;

        case adc_end_of_scan:
            return IEC6bits.ADCEOSIE;
            break;

        case adc_analog_circuit_ready:
            return IEC6bits.ADCARDYIE;
            break;

        case adc_update_ready:
            return IEC6bits.ADCURDYIE;
            break;

        case adc0_early_interrupt:
            return IEC6bits.ADC0EIE;
            break;

        case adc1_early_interrupt:
            return IEC6bits.ADC1EIE;
            break;

        case adc2_early_interrupt:
            return IEC6bits.ADC2EIE;
            break;

        case adc3_early_interrupt:
            return IEC6bits.ADC3EIE;
            break;

        case adc4_early_interrupt:
            return IEC6bits.ADC4EIE;
            break;

        case adc_group_early_interrupt_request:
            return IEC6bits.ADCGRPIE;
            break;

        case adc7_early_interrupt:
            return IEC6bits.ADC7EIE;
            break;

        case adc0_warm_interrupt:
            return IEC6bits.ADC0WIE;
            break;

        case adc1_warm_interrupt:
            return IEC6bits.ADC1WIE;
            break;

        case adc2_warm_interrupt:
            return IEC6bits.ADC2WIE;
            break;

        case adc3_warm_interrupt:
            return IEC6bits.ADC3WIE;
            break;

        case adc4_warm_interrupt:
            return IEC6bits.ADC4WIE;
            break;

        case adc7_warm_interrupt:
            return IEC6bits.ADC7WIE;
            break;

        case mpll_fault_interrupt:
            return IEC6bits.MPLLFLTIE;
            break;
            
        default:
            break;
            
    }

}

// This function allows for the modification of a given interrupt flag
// It sets the interrupt's 'Interrupt Flag' bit
void setInterruptFlag(interrupt_source_t input_interrupt, uint8_t flag_state) {
    
    // Decide which interrupt control bits to manipulate based on which interrupt
    // is being enabled or disabled
    switch (input_interrupt) {
        

        case core_timer_interrupt:
            IFS0bits.CTIF = flag_state;
            break;

        case core_software_interrupt_0:
            IFS0bits.CS0IF = flag_state;
            break;

        case core_software_interrupt_1:
            IFS0bits.CS1IF = flag_state;
            break;

        case external_interrupt_0:
            IFS0bits.INT0IF = flag_state;
            break;

        case timer1:
            IFS0bits.T1IF = flag_state;
            break;

        case input_capture_1_error:
            IFS0bits.IC1EIF = flag_state;
            break;

        case input_capture_1:
            IFS0bits.IC1IF = flag_state;
            break;

        case output_compare_1:
            IFS0bits.OC1IF = flag_state;
            break;

        case external_interrupt_1:
            IFS0bits.INT1IF = flag_state;
            break;

        case timer2:
            IFS0bits.T2IF = flag_state;
            break;

        case input_capture_2_error:
            IFS0bits.IC2EIF = flag_state;
            break;

        case input_capture_2:
            IFS0bits.IC2IF = flag_state;
            break;

        case output_compare_2:
            IFS0bits.OC2IF = flag_state;
            break;

        case external_interrupt_2:
            IFS0bits.INT2IF = flag_state;
            break;

        case timer3:
            IFS0bits.T3IF = flag_state;
            break;

        case input_capture_3_error:
            IFS0bits.IC3EIF = flag_state;
            break;

        case input_capture_3:
            IFS0bits.IC3IF = flag_state;
            break;

        case output_compare_3:
            IFS0bits.OC3IF = flag_state;
            break;

        case external_interrupt_3:
            IFS0bits.INT3IF = flag_state;
            break;

        case timer4:
            IFS0bits.T4IF = flag_state;
            break;

        case input_capture_4_error:
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
            break;

        case adc_data_38:
            IFS3bits.ADCD38IF = flag_state;
            break;

        case adc_data_39:
            IFS3bits.ADCD39IF = flag_state;
            break;

        case adc_data_40:
            IFS3bits.ADCD40IF = flag_state;
            break;

        case adc_data_41:
            IFS3bits.ADCD41IF = flag_state;
            break;

        case adc_data_42:
            IFS3bits.ADCD42IF = flag_state;
            break;

        case adc_data_43:
            IFS3bits.ADCD43IF = flag_state;
            break;

        case usb_suspend_resume_event:
            IFS3bits.USBSRIF = flag_state;
            break;

        case core_performance_counter_interrupt:
            IFS3bits.CPCIF = flag_state;
            break;

        case core_fast_debug_channel_interrupt:
            IFS3bits.CFDCIF = flag_state;
            break;

        case system_bus_protection_violation:
            IFS3bits.SBIF = flag_state;
            break;

        case spi1_fault:
            IFS3bits.SPI1EIF = flag_state;
            break;

        case spi1_receive_done:
            IFS3bits.SPI1RXIF = flag_state;
            break;

        case spi1_transfer_done:
            IFS3bits.SPI1TXIF = flag_state;
            break;

        case uart1_fault:
            IFS3bits.U1EIF = flag_state;
            break;

        case uart1_receive_done:
            IFS3bits.U1RXIF = flag_state;
            break;

        case uart1_transfer_done:
            IFS3bits.U1TXIF = flag_state;
            break;

        case i2c1_bus_collision_event:
            IFS3bits.I2C1BIF = flag_state;
            break;

        case i2c1_client_event:
            IFS3bits.I2C1SIF = flag_state;
            break;

        case i2c1_host_event:
            IFS3bits.I2C1MIF = flag_state;
            break;

        case porta_input_change_interrupt:
            IFS3bits.CNAIF = flag_state;
            break;

        case portb_input_change_interrupt:
            IFS3bits.CNBIF = flag_state;
            break;

        case portc_input_change_interrupt:
            IFS3bits.CNCIF = flag_state;
            break;

        case portd_input_change_interrupt:
            IFS3bits.CNDIF = flag_state;
            break;

        case porte_input_change_interrupt:
            IFS3bits.CNEIF = flag_state;
            break;

        case portf_input_change_interrupt:
            IFS3bits.CNFIF = flag_state;
            break;

        case portg_input_change_interrupt:
            IFS3bits.CNGIF = flag_state;
            break;

        case porth_input_change_interrupt:
            IFS3bits.CNHIF = flag_state;
            break;

        case portj_input_change_interrupt:
            IFS3bits.CNJIF = flag_state;
            break;

        case portk_input_change_interrupt:
            IFS3bits.CNKIF = flag_state;
            break;

        case pmp:
            IFS4bits.PMPIF = flag_state;
            break;

        case pmp_error:
            IFS4bits.PMPEIF = flag_state;
            break;

        case comparator_1_interrupt:
            IFS4bits.CMP1IF = flag_state;
            break;

        case comparator_2_interrupt:
            IFS4bits.CMP2IF = flag_state;
            break;

        case usb_general_event:
            IFS4bits.USBIF = flag_state;
            break;

        case usb_dma_event:
            IFS4bits.USBDMAIF = flag_state;
            break;

        case dma_channel_0:
            IFS4bits.DMA0IF = flag_state;
            break;

        case dma_channel_1:
            IFS4bits.DMA1IF = flag_state;
            break;

        case dma_channel_2:
            IFS4bits.DMA2IF = flag_state;
            break;

        case dma_channel_3:
            IFS4bits.DMA3IF = flag_state;
            break;

        case dma_channel_4:
            IFS4bits.DMA4IF = flag_state;
            break;

        case dma_channel_5:
            IFS4bits.DMA5IF = flag_state;
            break;

        case dma_channel_6:
            IFS4bits.DMA6IF = flag_state;
            break;

        case dma_channel_7:
            IFS4bits.DMA7IF = flag_state;
            break;

        case spi2_fault:
            IFS4bits.SPI2EIF = flag_state;
            break;

        case spi2_receive_done:
            IFS4bits.SPI2RXIF = flag_state;
            break;

        case spi2_transfer_done:
            IFS4bits.SPI2TXIF = flag_state;
            break;

        case uart2_fault:
            IFS4bits.U2EIF = flag_state;
            break;

        case uart2_receive_done:
            IFS4bits.U2RXIF = flag_state;
            break;

        case uart2_transfer_done:
            IFS4bits.U2TXIF = flag_state;
            break;

        case i2c2_bus_collision_event:
            IFS4bits.I2C2BIF = flag_state;
            break;

        case i2c2_client_event:
            IFS4bits.I2C2SIF = flag_state;
            break;

        case i2c2_host_event:
            IFS4bits.I2C2MIF = flag_state;
            break;

        case control_area_network_1:
            IFS4bits.CAN1IF = flag_state;
            break;

        case control_area_network_2:
            IFS4bits.CAN2IF = flag_state;
            break;

        case ethernet_interrupt:
            IFS4bits.ETHIF = flag_state;
            break;

        case spi3_fault:
            IFS4bits.SPI3EIF = flag_state;
            break;

        case spi3_receive_done:
            IFS4bits.SPI3RXIF = flag_state;
            break;

        case spi3_transfer_done:
            IFS4bits.SPI3TXIF = flag_state;
            break;

        case uart3_fault:
            IFS4bits.U3EIF = flag_state;
            break;

        case uart3_receive_done:
            IFS4bits.U3RXIF = flag_state;
            break;

        case uart3_transfer_done:
            IFS4bits.U3TXIF = flag_state;
            break;

        case i2c3_bus_collision_event:
            IFS5bits.I2C3BIF = flag_state;
            break;

        case i2c3_client_event:
            IFS5bits.I2C3SIF = flag_state;
            break;

        case i2c3_host_event:
            IFS5bits.I2C3MIF = flag_state;
            break;

        case spi4_fault:
            IFS5bits.SPI4EIF = flag_state;
            break;

        case spi4_receive_done:
            IFS5bits.SPI4RXIF = flag_state;
            break;

        case spi4_transfer_done:
            IFS5bits.SPI4TXIF = flag_state;
            break;

        case real_time_clock:
            IFS5bits.RTCCIF = flag_state;
            break;

        case flash_control_event:
            IFS5bits.FCEIF = flag_state;
            break;

        case prefetch_module_sec_event:
            IFS5bits.PREIF = flag_state;
            break;

        case sqi1_event:
            IFS5bits.SQI1IF = flag_state;
            break;

        case uart4_fault:
            IFS5bits.U4EIF = flag_state;
            break;

        case uart4_receive_done:
            IFS5bits.U4RXIF = flag_state;
            break;

        case uart4_transfer_done:
            IFS5bits.U4TXIF = flag_state;
            break;

        case i2c4_bus_collision_event:
            IFS5bits.I2C4BIF = flag_state;
            break;

        case i2c4_client_event:
            IFS5bits.I2C4SIF = flag_state;
            break;

        case i2c4_host_event:
            IFS5bits.I2C4MIF = flag_state;
            break;

        case spi5_fault:
            IFS5bits.SPI5EIF = flag_state;
            break;

        case spi5_receive_done:
            IFS5bits.SPI5RXIF = flag_state;
            break;

        case spi5_transfer_done:
            IFS5bits.SPI5TXIF = flag_state;
            break;

        case uart5_fault:
            IFS5bits.U5EIF = flag_state;
            break;

        case uart5_receive_done:
            IFS5bits.U5RXIF = flag_state;
            break;

        case uart5_transfer_done:
            IFS5bits.U5TXIF = flag_state;
            break;

        case i2c5_bus_collision_event:
            IFS5bits.I2C5BIF = flag_state;
            break;

        case i2c5_client_event:
            IFS5bits.I2C5SIF = flag_state;
            break;

        case i2c5_host_event:
            IFS5bits.I2C5MIF = flag_state;
            break;

        case spi6_fault:
            IFS5bits.SPI6IF = flag_state;
            break;

        case spi6_receive_done:
            IFS5bits.SPI6RXIF = flag_state;
            break;

        case spi6_transfer_done:
            IFS5bits.SPI6TX = flag_state;
            break;

        case uart6_fault:
            IFS5bits.U6EIF = flag_state;
            break;

        case uart6_receive_done:
            IFS5bits.U6RXIF = flag_state;
            break;

        case uart6_transfer_done:
            IFS5bits.U6TXIF = flag_state;
            break;

        case sdhc_interrupt:
            IFS5bits.SDHCIF = flag_state;
            break;

        case glcd_interrupt:
            IFS6bits.GLCDIF = flag_state;
            break;

        case gpu_interrupt:
            IFS6bits.GPUIF = flag_state;
            break;

        case ctmu_interrupt:
            IFS6bits.CTMUIF = flag_state;
            break;

        case adc_end_of_scan:
            IFS6bits.ADCEOSIF = flag_state;
            break;

        case adc_analog_circuit_ready:
            IFS6bits.ADCARDYIF = flag_state;
            break;

        case adc_update_ready:
            IFS6bits.ADCURDYIF = flag_state;
            break;

        case adc0_early_interrupt:
            IFS6bits.ADC0EIF = flag_state;
            break;

        case adc1_early_interrupt:
            IFS6bits.ADC1EIF = flag_state;
            break;

        case adc2_early_interrupt:
            IFS6bits.ADC2EIF = flag_state;
            break;

        case adc3_early_interrupt:
            IFS6bits.ADC3EIF = flag_state;
            break;

        case adc4_early_interrupt:
            IFS6bits.ADC4EIF = flag_state;
            break;

        case adc_group_early_interrupt_request:
            IFS6bits.ADCGRPIF = flag_state;
            break;

        case adc7_early_interrupt:
            IFS6bits.ADC7EIF = flag_state;
            break;

        case adc0_warm_interrupt:
            IFS6bits.ADC0WIF = flag_state;
            break;

        case adc1_warm_interrupt:
            IFS6bits.ADC1WIF = flag_state;
            break;

        case adc2_warm_interrupt:
            IFS6bits.ADC2WIF = flag_state;
            break;

        case adc3_warm_interrupt:
            IFS6bits.ADC3WIF = flag_state;
            break;

        case adc4_warm_interrupt:
            IFS6bits.ADC4WIF = flag_state;
            break;

        case adc7_warm_interrupt:
            IFS6bits.ADC7WIF = flag_state;
            break;

        case mpll_fault_interrupt:
            IFS6bits.MPLLFLTIF = flag_state;
            break;
            
        default:
            break;
            
    }
    
}


// This function allows for the reading of a given interrupt flag
// It reads the interrupt's 'Interrupt Flag' bit
// Returns the state of the given interrupt flag
uint8_t getInterruptFlag(interrupt_source_t input_interrupt) {
    
    // Decide which interrupt control bits to manipulate based on which interrupt
    // is being enabled or disabled
    switch (input_interrupt) {
        

        case core_timer_interrupt:
            return IFS0bits.CTIF;
            break;

        case core_software_interrupt_0:
            return IFS0bits.CS0IF;
            break;

        case core_software_interrupt_1:
            return IFS0bits.CS1IF;
            break;

        case external_interrupt_0:
            return IFS0bits.INT0IF;
            break;

        case timer1:
            return IFS0bits.T1IF;
            break;

        case input_capture_1_error:
            return IFS0bits.IC1EIF;
            break;

        case input_capture_1:
            return IFS0bits.IC1IF;
            break;

        case output_compare_1:
            return IFS0bits.OC1IF;
            break;

        case external_interrupt_1:
            return IFS0bits.INT1IF;
            break;

        case timer2:
            return IFS0bits.T2IF;
            break;

        case input_capture_2_error:
            return IFS0bits.IC2EIF;
            break;

        case input_capture_2:
            return IFS0bits.IC2IF;
            break;

        case output_compare_2:
            return IFS0bits.OC2IF;
            break;

        case external_interrupt_2:
            return IFS0bits.INT2IF;
            break;

        case timer3:
            return IFS0bits.T3IF;
            break;

        case input_capture_3_error:
            return IFS0bits.IC3EIF;
            break;

        case input_capture_3:
            return IFS0bits.IC3IF;
            break;

        case output_compare_3:
            return IFS0bits.OC3IF;
            break;

        case external_interrupt_3:
            return IFS0bits.INT3IF;
            break;

        case timer4:
            return IFS0bits.T4IF;
            break;

        case input_capture_4_error:
            return IFS0bits.IC4EIF;
            break;

        case input_capture_4:
            return IFS0bits.IC4IF;
            break;

        case output_compare_4:
            return IFS0bits.OC4IF;
            break;

        case external_interrupt_4:
            return IFS0bits.INT4IF;
            break;

        case timer5:
            return IFS0bits.T5IF;
            break;

        case input_capture_5_error:
            return IFS0bits.IC5EIF;
            break;

        case input_capture_5:
            return IFS0bits.IC5IF;
            break;

        case output_compare_5:
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
            break;

        case uart1_fault:
            return IFS3bits.U1EIF;
            break;

        case uart1_receive_done:
            return IFS3bits.U1RXIF;
            break;

        case uart1_transfer_done:
            return IFS3bits.U1TXIF;
            break;

        case i2c1_bus_collision_event:
            return IFS3bits.I2C1BIF;
            break;

        case i2c1_client_event:
            return IFS3bits.I2C1SIF;
            break;

        case i2c1_host_event:
            return IFS3bits.I2C1MIF;
            break;

        case porta_input_change_interrupt:
            return IFS3bits.CNAIF;
            break;

        case portb_input_change_interrupt:
            return IFS3bits.CNBIF;
            break;

        case portc_input_change_interrupt:
            return IFS3bits.CNCIF;
            break;

        case portd_input_change_interrupt:
            return IFS3bits.CNDIF;
            break;

        case porte_input_change_interrupt:
            return IFS3bits.CNEIF;
            break;

        case portf_input_change_interrupt:
            return IFS3bits.CNFIF;
            break;

        case portg_input_change_interrupt:
            return IFS3bits.CNGIF;
            break;

        case porth_input_change_interrupt:
            return IFS3bits.CNHIF;
            break;

        case portj_input_change_interrupt:
            return IFS3bits.CNJIF;
            break;

        case portk_input_change_interrupt:
            return IFS3bits.CNKIF;
            break;

        case pmp:
            return IFS4bits.PMPIF;
            break;

        case pmp_error:
            return IFS4bits.PMPEIF;
            break;

        case comparator_1_interrupt:
            return IFS4bits.CMP1IF;
            break;

        case comparator_2_interrupt:
            return IFS4bits.CMP2IF;
            break;

        case usb_general_event:
            return IFS4bits.USBIF;
            break;

        case usb_dma_event:
            return IFS4bits.USBDMAIF;
            break;

        case dma_channel_0:
            return IFS4bits.DMA0IF;
            break;

        case dma_channel_1:
            return IFS4bits.DMA1IF;
            break;

        case dma_channel_2:
            return IFS4bits.DMA2IF;
            break;

        case dma_channel_3:
            return IFS4bits.DMA3IF;
            break;

        case dma_channel_4:
            return IFS4bits.DMA4IF;
            break;

        case dma_channel_5:
            return IFS4bits.DMA5IF;
            break;

        case dma_channel_6:
            return IFS4bits.DMA6IF;
            break;

        case dma_channel_7:
            return IFS4bits.DMA7IF;
            break;

        case spi2_fault:
            return IFS4bits.SPI2EIF;
            break;

        case spi2_receive_done:
            return IFS4bits.SPI2RXIF;
            break;

        case spi2_transfer_done:
            return IFS4bits.SPI2TXIF;
            break;

        case uart2_fault:
            return IFS4bits.U2EIF;
            break;

        case uart2_receive_done:
            return IFS4bits.U2RXIF;
            break;

        case uart2_transfer_done:
            return IFS4bits.U2TXIF;
            break;

        case i2c2_bus_collision_event:
            return IFS4bits.I2C2BIF;
            break;

        case i2c2_client_event:
            return IFS4bits.I2C2SIF;
            break;

        case i2c2_host_event:
            return IFS4bits.I2C2MIF;
            break;

        case control_area_network_1:
            return IFS4bits.CAN1IF;
            break;

        case control_area_network_2:
            return IFS4bits.CAN2IF;
            break;

        case ethernet_interrupt:
            return IFS4bits.ETHIF;
            break;

        case spi3_fault:
            return IFS4bits.SPI3EIF;
            break;

        case spi3_receive_done:
            return IFS4bits.SPI3RXIF;
            break;

        case spi3_transfer_done:
            return IFS4bits.SPI3TXIF;
            break;

        case uart3_fault:
            return IFS4bits.U3EIF;
            break;

        case uart3_receive_done:
            return IFS4bits.U3RXIF;
            break;

        case uart3_transfer_done:
            return IFS4bits.U3TXIF;
            break;

        case i2c3_bus_collision_event:
            return IFS5bits.I2C3BIF;
            break;

        case i2c3_client_event:
            return IFS5bits.I2C3SIF;
            break;

        case i2c3_host_event:
            return IFS5bits.I2C3MIF;
            break;

        case spi4_fault:
            return IFS5bits.SPI4EIF;
            break;

        case spi4_receive_done:
            return IFS5bits.SPI4RXIF;
            break;

        case spi4_transfer_done:
            return IFS5bits.SPI4TXIF;
            break;

        case real_time_clock:
            return IFS5bits.RTCCIF;
            break;

        case flash_control_event:
            return IFS5bits.FCEIF;
            break;

        case prefetch_module_sec_event:
            return IFS5bits.PREIF;
            break;

        case sqi1_event:
            return IFS5bits.SQI1IF;
            break;

        case uart4_fault:
            return IFS5bits.U4EIF;
            break;

        case uart4_receive_done:
            return IFS5bits.U4RXIF;
            break;

        case uart4_transfer_done:
            return IFS5bits.U4TXIF;
            break;

        case i2c4_bus_collision_event:
            return IFS5bits.I2C4BIF;
            break;

        case i2c4_client_event:
            return IFS5bits.I2C4SIF;
            break;

        case i2c4_host_event:
            return IFS5bits.I2C4MIF;
            break;

        case spi5_fault:
            return IFS5bits.SPI5EIF;
            break;

        case spi5_receive_done:
            return IFS5bits.SPI5RXIF;
            break;

        case spi5_transfer_done:
            return IFS5bits.SPI5TXIF;
            break;

        case uart5_fault:
            return IFS5bits.U5EIF;
            break;

        case uart5_receive_done:
            return IFS5bits.U5RXIF;
            break;

        case uart5_transfer_done:
            return IFS5bits.U5TXIF;
            break;

        case i2c5_bus_collision_event:
            return IFS5bits.I2C5BIF;
            break;

        case i2c5_client_event:
            return IFS5bits.I2C5SIF;
            break;

        case i2c5_host_event:
            return IFS5bits.I2C5MIF;
            break;

        case spi6_fault:
            return IFS5bits.SPI6IF;
            break;

        case spi6_receive_done:
            return IFS5bits.SPI6RXIF;
            break;

        case spi6_transfer_done:
            return IFS5bits.SPI6TX;
            break;

        case uart6_fault:
            return IFS5bits.U6EIF;
            break;

        case uart6_receive_done:
            return IFS5bits.U6RXIF;
            break;

        case uart6_transfer_done:
            return IFS5bits.U6TXIF;
            break;

        case sdhc_interrupt:
            return IFS5bits.SDHCIF;
            break;

        case glcd_interrupt:
            return IFS6bits.GLCDIF;
            break;

        case gpu_interrupt:
            return IFS6bits.GPUIF;
            break;

        case ctmu_interrupt:
            return IFS6bits.CTMUIF;
            break;

        case adc_end_of_scan:
            return IFS6bits.ADCEOSIF;
            break;

        case adc_analog_circuit_ready:
            return IFS6bits.ADCARDYIF;
            break;

        case adc_update_ready:
            return IFS6bits.ADCURDYIF;
            break;

        case adc0_early_interrupt:
            return IFS6bits.ADC0EIF;
            break;

        case adc1_early_interrupt:
            return IFS6bits.ADC1EIF;
            break;

        case adc2_early_interrupt:
            return IFS6bits.ADC2EIF;
            break;

        case adc3_early_interrupt:
            return IFS6bits.ADC3EIF;
            break;

        case adc4_early_interrupt:
            return IFS6bits.ADC4EIF;
            break;

        case adc_group_early_interrupt_request:
            return IFS6bits.ADCGRPIF;
            break;

        case adc7_early_interrupt:
            return IFS6bits.ADC7EIF;
            break;

        case adc0_warm_interrupt:
            return IFS6bits.ADC0WIF;
            break;

        case adc1_warm_interrupt:
            return IFS6bits.ADC1WIF;
            break;

        case adc2_warm_interrupt:
            return IFS6bits.ADC2WIF;
            break;

        case adc3_warm_interrupt:
            return IFS6bits.ADC3WIF;
            break;

        case adc4_warm_interrupt:
            return IFS6bits.ADC4WIF;
            break;

        case adc7_warm_interrupt:
            return IFS6bits.ADC7WIF;
            break;

        case mpll_fault_interrupt:
            return IFS6bits.MPLLFLTIF;
            break;
            
        default:
            return 0;
            break;
            
    }
    
}

// This function sets the priority for a given interrupt
void setInterruptPriority(interrupt_source_t input_interrupt, uint8_t input_priority) {
    
    // verify input priority is between 0 and 7
    if (input_priority > 7) {
        
        input_priority = 7;
    
    }
    
    // Decide which interrupt control bits to manipulate based on which interrupt
    // is having its priority set
    switch (input_interrupt) {

        case core_timer_interrupt:
            IPC0bits.CTIP = input_priority;
            break;

        case core_software_interrupt_0:
            IPC0bits.CS0IP = input_priority;
            break;

        case core_software_interrupt_1:
            IPC0bits.CS1IP = input_priority;
            break;

        case external_interrupt_0:
            IPC0bits.INT0IP = input_priority;
            break;

        case timer1:
            IPC1bits.T1IP = input_priority;
            break;

        case input_capture_1_error:
            IPC1bits.IC1EIP = input_priority;
            break;

        case input_capture_1:
            IPC1bits.IC1IP = input_priority;
            break;

        case output_compare_1:
            IPC1bits.OC1IP = input_priority;
            break;

        case external_interrupt_1:
            IPC2bits.INT1IP = input_priority;
            break;

        case timer2:
            IPC2bits.T2IP = input_priority;
            break;

        case input_capture_2_error:
            IPC2bits.IC2EIP = input_priority;
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

        case adc_data_23:
            IPC20bits.ADCD23IP = input_priority;
            break;

        case adc_data_24:
            IPC20bits.ADCD24IP = input_priority;
            break;

        case adc_data_25:
            IPC21bits.ADCD25IP = input_priority;
            break;

        case adc_data_26:
            IPC21bits.ADCD26IP = input_priority;
            break;

        case adc_data_27:
            IPC21bits.ADCD27IP = input_priority;
            break;

        case adc_data_28:
            IPC21bits.ADCD28IP = input_priority;
            break;

        case adc_data_29:
            IPC22bits.ADCD29IP = input_priority;
            break;

        case adc_data_30:
            IPC22bits.ADCD30IP = input_priority;
            break;

        case adc_data_31:
            IPC22bits.ADCD31IP = input_priority;
            break;

        case adc_data_32:
            IPC22bits.ADCD32IP = input_priority;
            break;

        case adc_data_33:
            IPC23bits.ADCD33IP = input_priority;
            break;

        case adc_data_34:
            IPC23bits.ADCD34IP = input_priority;
            break;

        case adc_data_35:
            IPC23bits.ADCD35IP = input_priority;
            break;

        case adc_data_36:
            IPC23bits.ADCD36IP = input_priority;
            break;

        case adc_data_37:
            IPC24bits.ADCD37IP = input_priority;
            break;

        case adc_data_38:
            IPC24bits.ADCD38IP = input_priority;
            break;

        case adc_data_39:
            IPC24bits.ADCD39IP = input_priority;
            break;

        case adc_data_40:
            IPC24bits.ADCD40IP = input_priority;
            break;

        case adc_data_41:
            IPC25bits.ADCD41IP = input_priority;
            break;

        case adc_data_42:
            IPC25bits.ADCD42IP = input_priority;
            break;

        case adc_data_43:
            IPC25bits.ADCD43IP = input_priority;
            break;

        case usb_suspend_resume_event:
            IPC25bits.USBSRIP = input_priority;
            break;

        case core_performance_counter_interrupt:
            IPC26bits.CPCIP = input_priority;
            break;

        case core_fast_debug_channel_interrupt:
            IPC26bits.CFDCIP = input_priority;
            break;

        case system_bus_protection_violation:
            IPC26bits.SBIP = input_priority;
            break;

        case spi1_fault:
            IPC27bits.SPI1EIP = input_priority;
            break;

        case spi1_receive_done:
            IPC27bits.SPI1RXIP = input_priority;
            break;

        case spi1_transfer_done:
            IPC27bits.SPI1TXIP = input_priority;
            break;

        case uart1_fault:
            IPC28bits.U1EIP = input_priority;
            break;

        case uart1_receive_done:
            IPC28bits.U1RXIP = input_priority;
            break;

        case uart1_transfer_done:
            IPC28bits.U1TXIP = input_priority;
            break;

        case i2c1_bus_collision_event:
            IPC28bits.I2C1BIP = input_priority;
            break;

        case i2c1_client_event:
            IPC29bits.I2C1SIP = input_priority;
            break;

        case i2c1_host_event:
            IPC29bits.I2C1MIP = input_priority;
            break;

        case porta_input_change_interrupt:
            IPC29bits.CNAIP = input_priority;
            break;

        case portb_input_change_interrupt:
            IPC29bits.CNBIP = input_priority;
            break;

        case portc_input_change_interrupt:
            IPC30bits.CNCIP = input_priority;
            break;

        case portd_input_change_interrupt:
            IPC30bits.CNDIP = input_priority;
            break;

        case porte_input_change_interrupt:
            IPC30bits.CNEIP = input_priority;
            break;

        case portf_input_change_interrupt:
            IPC30bits.CNFIP = input_priority;
            break;

        case portg_input_change_interrupt:
            IPC31bits.CNGIP = input_priority;
            break;

        case porth_input_change_interrupt:
            IPC31bits.CNHIP = input_priority;
            break;

        case portj_input_change_interrupt:
            IPC31bits.CNJIP = input_priority;
            break;

        case portk_input_change_interrupt:
            IPC31bits.CNKIP = input_priority;
            break;

        case pmp:
            IPC32bits.PMPIP = input_priority;
            break;

        case pmp_error:
            IPC32bits.PMPEIP = input_priority;
            break;

        case comparator_1_interrupt:
            IPC32bits.CMP1IP = input_priority;
            break;

        case comparator_2_interrupt:
            IPC32bits.CMP2IP = input_priority;
            break;

        case usb_general_event:
            IPC33bits.USBIP = input_priority;
            break;

        case usb_dma_event:
            IPC33bits.USBDMAIP = input_priority;
            break;

        case dma_channel_0:
            IPC33bits.DMA0IP = input_priority;
            break;

        case dma_channel_1:
            IPC33bits.DMA1IP = input_priority;
            break;

        case dma_channel_2:
            IPC34bits.DMA2IP = input_priority;
            break;

        case dma_channel_3:
            IPC34bits.DMA3IP = input_priority;
            break;

        case dma_channel_4:
            IPC34bits.DMA4IP = input_priority;
            break;

        case dma_channel_5:
            IPC34bits.DMA5IP = input_priority;
            break;

        case dma_channel_6:
            IPC35bits.DMA6IP = input_priority;
            break;

        case dma_channel_7:
            IPC35bits.DMA7IP = input_priority;
            break;

        case spi2_fault:
            IPC35bits.SPI2EIP = input_priority;
            break;

        case spi2_receive_done:
            IPC35bits.SPI2RXIP = input_priority;
            break;

        case spi2_transfer_done:
            IPC36bits.SPI2TXIP = input_priority;
            break;

        case uart2_fault:
            IPC36bits.U2EIP = input_priority;
            break;

        case uart2_receive_done:
            IPC36bits.U2RXIP = input_priority;
            break;

        case uart2_transfer_done:
            IPC36bits.U2TXIP = input_priority;
            break;

        case i2c2_bus_collision_event:
            IPC37bits.I2C2BIP = input_priority;
            break;

        case i2c2_client_event:
            IPC37bits.I2C2SIP = input_priority;
            break;

        case i2c2_host_event:
            IPC37bits.I2C2MIP = input_priority;
            break;

        case control_area_network_1:
            IPC37bits.CAN1IP = input_priority;
            break;

        case control_area_network_2:
            IPC38bits.CAN2IP = input_priority;
            break;

        case ethernet_interrupt:
            IPC38bits.ETHIP = input_priority;
            break;

        case spi3_fault:
            IPC38bits.SPI3EIP = input_priority;
            break;

        case spi3_receive_done:
            IPC38bits.SPI3RXIP = input_priority;
            break;

        case spi3_transfer_done:
            IPC39bits.SPI3TXIP = input_priority;
            break;

        case uart3_fault:
            IPC39bits.U3EIP = input_priority;
            break;

        case uart3_receive_done:
            IPC39bits.U3RXIP = input_priority;
            break;

        case uart3_transfer_done:
            IPC39bits.U3TXIP = input_priority;
            break;

        case i2c3_bus_collision_event:
            IPC40bits.I2C3BIP = input_priority;
            break;

        case i2c3_client_event:
            IPC40bits.I2C3SIP = input_priority;
            break;

        case i2c3_host_event:
            IPC40bits.I2C3MIP = input_priority;
            break;

        case spi4_fault:
            IPC40bits.SPI4EIP = input_priority;
            break;

        case spi4_receive_done:
            IPC41bits.SPI4RXIP = input_priority;
            break;

        case spi4_transfer_done:
            IPC41bits.SPI4TXIP = input_priority;
            break;

        case real_time_clock:
            IPC41bits.RTCCIP = input_priority;
            break;

        case flash_control_event:
            IPC41bits.FCEIP = input_priority;
            break;

        case prefetch_module_sec_event:
            IPC42bits.PREIP = input_priority;
            break;

        case sqi1_event:
            IPC42bits.SQI1IP = input_priority;
            break;

        case uart4_fault:
            IPC42bits.U4EIP = input_priority;
            break;

        case uart4_receive_done:
            IPC42bits.U4RXIP = input_priority;
            break;

        case uart4_transfer_done:
            IPC43bits.U4TXIP = input_priority;
            break;

        case i2c4_bus_collision_event:
            IPC43bits.I2C4BIP = input_priority;
            break;

        case i2c4_client_event:
            IPC43bits.I2C4SIP = input_priority;
            break;

        case i2c4_host_event:
            IPC43bits.I2C4MIP = input_priority;
            break;

        case spi5_fault:
            IPC44bits.SPI5EIP = input_priority;
            break;

        case spi5_receive_done:
            IPC44bits.SPI5RXIP = input_priority;
            break;

        case spi5_transfer_done:
            IPC44bits.SPI5TXIP = input_priority;
            break;

        case uart5_fault:
            IPC44bits.U5EIP = input_priority;
            break;

        case uart5_receive_done:
            IPC45bits.U5RXIP = input_priority;
            break;

        case uart5_transfer_done:
            IPC45bits.U5TXIP = input_priority;
            break;

        case i2c5_bus_collision_event:
            IPC45bits.I2C5BIP = input_priority;
            break;

        case i2c5_client_event:
            IPC45bits.I2C5SIP = input_priority;
            break;

        case i2c5_host_event:
            IPC46bits.I2C5MIP = input_priority;
            break;

        case spi6_fault:
            IPC46bits.SPI6EIP = input_priority;
            break;

        case spi6_receive_done:
            IPC46bits.SPI6RXIP = input_priority;
            break;

        case spi6_transfer_done:
            IPC46bits.SPI6TXIP = input_priority;
            break;

        case uart6_fault:
            IPC47bits.U6EIP = input_priority;
            break;

        case uart6_receive_done:
            IPC47bits.U6RXIP = input_priority;
            break;

        case uart6_transfer_done:
            IPC47bits.U6TXIP = input_priority;
            break;

        // IRQ 191 has no named IPC47 field on this device, so set it directly
        // IPC47<28:26> = priority, IPC47<25:24> = subpriority
        case sdhc_interrupt:
            IPC47CLR = 0x7 << 26;
            IPC47SET = input_priority << 26;
            break;

        case glcd_interrupt:
            IPC48bits.GLCDIP = input_priority;
            break;

        case gpu_interrupt:
            IPC48bits.GPUIP = input_priority;
            break;

        case ctmu_interrupt:
            IPC48bits.CTMUIP = input_priority;
            break;

        case adc_end_of_scan:
            IPC49bits.ADCEOSIP = input_priority;
            break;

        case adc_analog_circuit_ready:
            IPC49bits.ADCARDYIP = input_priority;
            break;

        case adc_update_ready:
            IPC49bits.ADCURDYIP = input_priority;
            break;

        case adc0_early_interrupt:
            IPC49bits.ADC0EIP = input_priority;
            break;

        case adc1_early_interrupt:
            IPC50bits.ADC1EIP = input_priority;
            break;

        case adc2_early_interrupt:
            IPC50bits.ADC2EIP = input_priority;
            break;

        case adc3_early_interrupt:
            IPC50bits.ADC3EIP = input_priority;
            break;

        case adc4_early_interrupt:
            IPC50bits.ADC4EIP = input_priority;
            break;

        case adc_group_early_interrupt_request:
            IPC51bits.ADCGRPEIP = input_priority;
            break;

        case adc7_early_interrupt:
            IPC51bits.ADC7EIP = input_priority;
            break;

        case adc0_warm_interrupt:
            IPC51bits.ADC0WIP = input_priority;
            break;

        case adc1_warm_interrupt:
            IPC52bits.ADC1WIP = input_priority;
            break;

        case adc2_warm_interrupt:
            IPC52bits.ADC2WIP = input_priority;
            break;

        case adc3_warm_interrupt:
            IPC52bits.ADC3WIP = input_priority;
            break;

        case adc4_warm_interrupt:
            IPC52bits.ADC4WIP = input_priority;
            break;

        case adc7_warm_interrupt:
            IPC53bits.ADC7WIP = input_priority;
            break;

        case mpll_fault_interrupt:
            IPC53bits.MPLLFLTIP = input_priority;
            break;
            
        default:
            break;
            
    }
    
}
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
