drewsum/Thermal_Camera/rev_a/sfw/U1701_firmware/Thermal_Camera/i2c/i2c_master.c

/*******************************************************************************
  I2C1 Master Driver

  File Name:
    i2c_master.c

  Summary:
    Interrupt-driven, queued driver for the I2C1 peripheral in master mode.
    See i2c_master.h for the queueing model.
*******************************************************************************/

#include "i2c/i2c_master.h"
#include "core/32mzda_interrupt_control.h"
#include "core/device_control.h"
#include <xc.h>

#include <stdio.h>
#include <string.h>

#include "usb_uart/terminal_control.h"
#include "application/error_handler.h"

// These are macros needed for defining ISRs, included in XC32
#include <sys/attribs.h>

// *****************************************************************************
// Section: Internal State
// *****************************************************************************

typedef enum
{
    I2C_TRANSFER_TYPE_WRITE = 0,
    I2C_TRANSFER_TYPE_READ,
} I2C_TRANSFER_TYPE;

typedef enum
{
    I2C_STATE_ADDR_BYTE_1_SEND,
    I2C_STATE_ADDR_BYTE_2_SEND,
    I2C_STATE_READ_10BIT_MODE,
    I2C_STATE_ADDR_BYTE_1_SEND_10BIT_ONLY,
    I2C_STATE_WRITE,
    I2C_STATE_READ,
    I2C_STATE_READ_BYTE,
    I2C_STATE_WAIT_ACK_COMPLETE,
    I2C_STATE_WAIT_STOP_CONDITION_COMPLETE,
    I2C_STATE_WAIT_BUS_FREE,
    I2C_STATE_IDLE,
} I2C_STATE;

// Working state of the transaction currently on the bus. Loaded from the
// queue head by I2C_EngineStart() and advanced by the I2C1 master ISR.
typedef struct
{
    uint16_t            address;
    const uint8_t       *writeBuffer;
    uint8_t             *readBuffer;
    size_t              writeSize;
    size_t              readSize;
    size_t              writeCount;
    size_t              readCount;
    I2C_TRANSFER_TYPE   transferType;
    I2C_STATE           state;
    I2C_ERROR           error;
} I2C_OBJ;

static volatile I2C_OBJ i2cObj;

// One queued transaction. Small write payloads (<= I2C_QUEUE_STAGED_MAX
// bytes) are copied into `staged` at enqueue time so the caller's buffer
// doesn't have to outlive the call; larger write buffers and all read
// buffers stay caller-owned until the callback fires.
typedef struct
{
    uint16_t              address;
    const uint8_t         *writeBuffer;
    uint8_t               *readBuffer;
    size_t                writeSize;
    size_t                readSize;
    uint8_t               staged[I2C_QUEUE_STAGED_MAX];
    I2C_TRANSFER_CALLBACK callback;
    uintptr_t             context;
} I2C_TRANSACTION;

// Must be a power of two: head/tail are free-running uint8_t indices and
// are reduced modulo the depth, so wraparound arithmetic stays correct.
#define I2C_QUEUE_DEPTH   32u

// Single-producer (thread context, with the I2C interrupts masked) /
// single-consumer (the I2C1 ISRs) FIFO. Slots [head, tail) are occupied;
// the head slot is the transaction currently on the bus.
static volatile I2C_TRANSACTION i2cQueue[I2C_QUEUE_DEPTH];
static volatile uint8_t i2cQueueHead;   // next transaction to execute/retire
static volatile uint8_t i2cQueueTail;   // next free slot

// CP0 count captured when the head transaction started, for I2C_Tasks()'s
// wedged-transfer watchdog.
static volatile uint32_t i2cTransferStartTick;

// CP0 count captured when the last stop condition completed, for the
// per-device bus-free timing below.
static volatile uint32_t i2cLastStopTick;
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
